gowenrw/g0dzilla_vs/art/g0dzilla_vs_3D_proto_combined.jpg

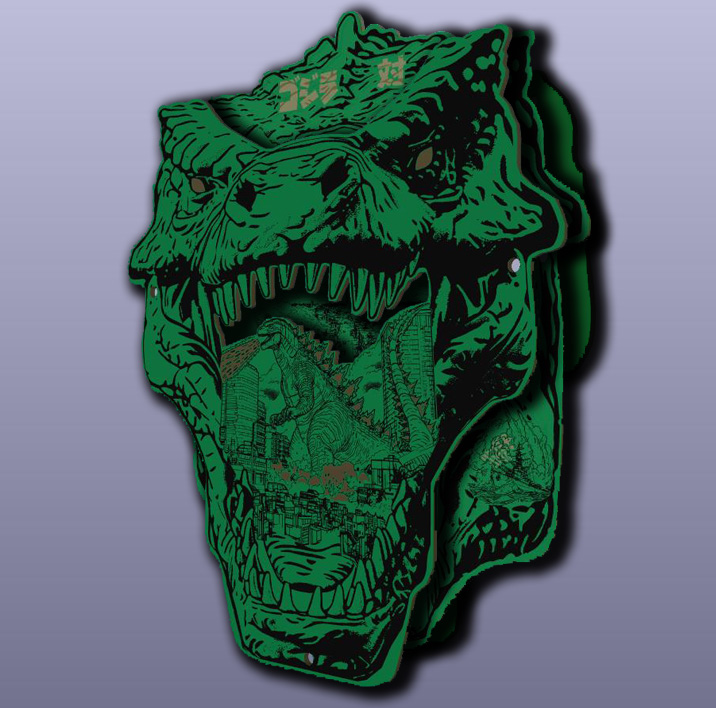
art/g0dzilla_vs_3D_proto_combined.jpg
