gowenrw/g0dzilla_vs/art/g0dzilla_vs_rev02_EdgeCuts-Export-04-01.jpg

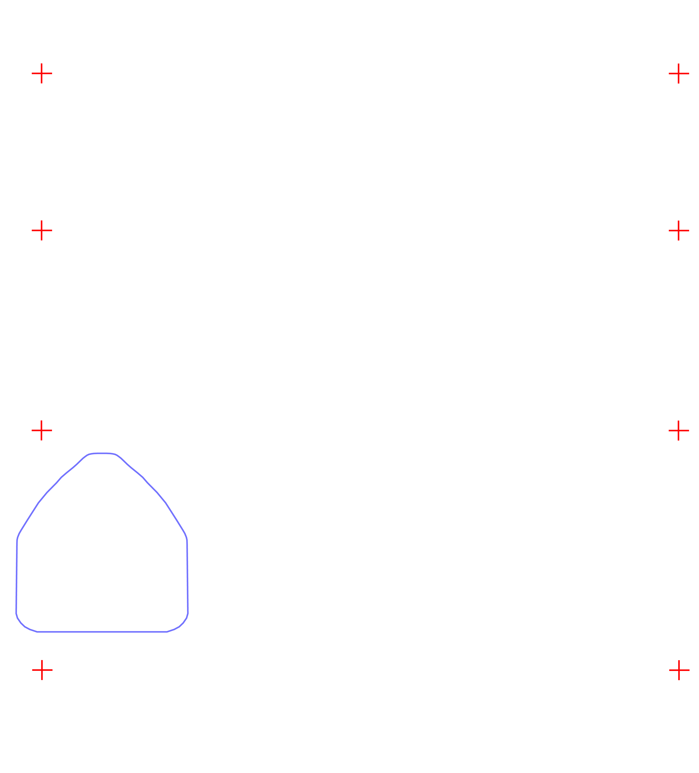
art/g0dzilla_vs_rev02_EdgeCuts-Export-04-01.jpg
