gowenrw/g0dzilla_vs/art/g0dzilla_vs_rev02_face_front.jpg

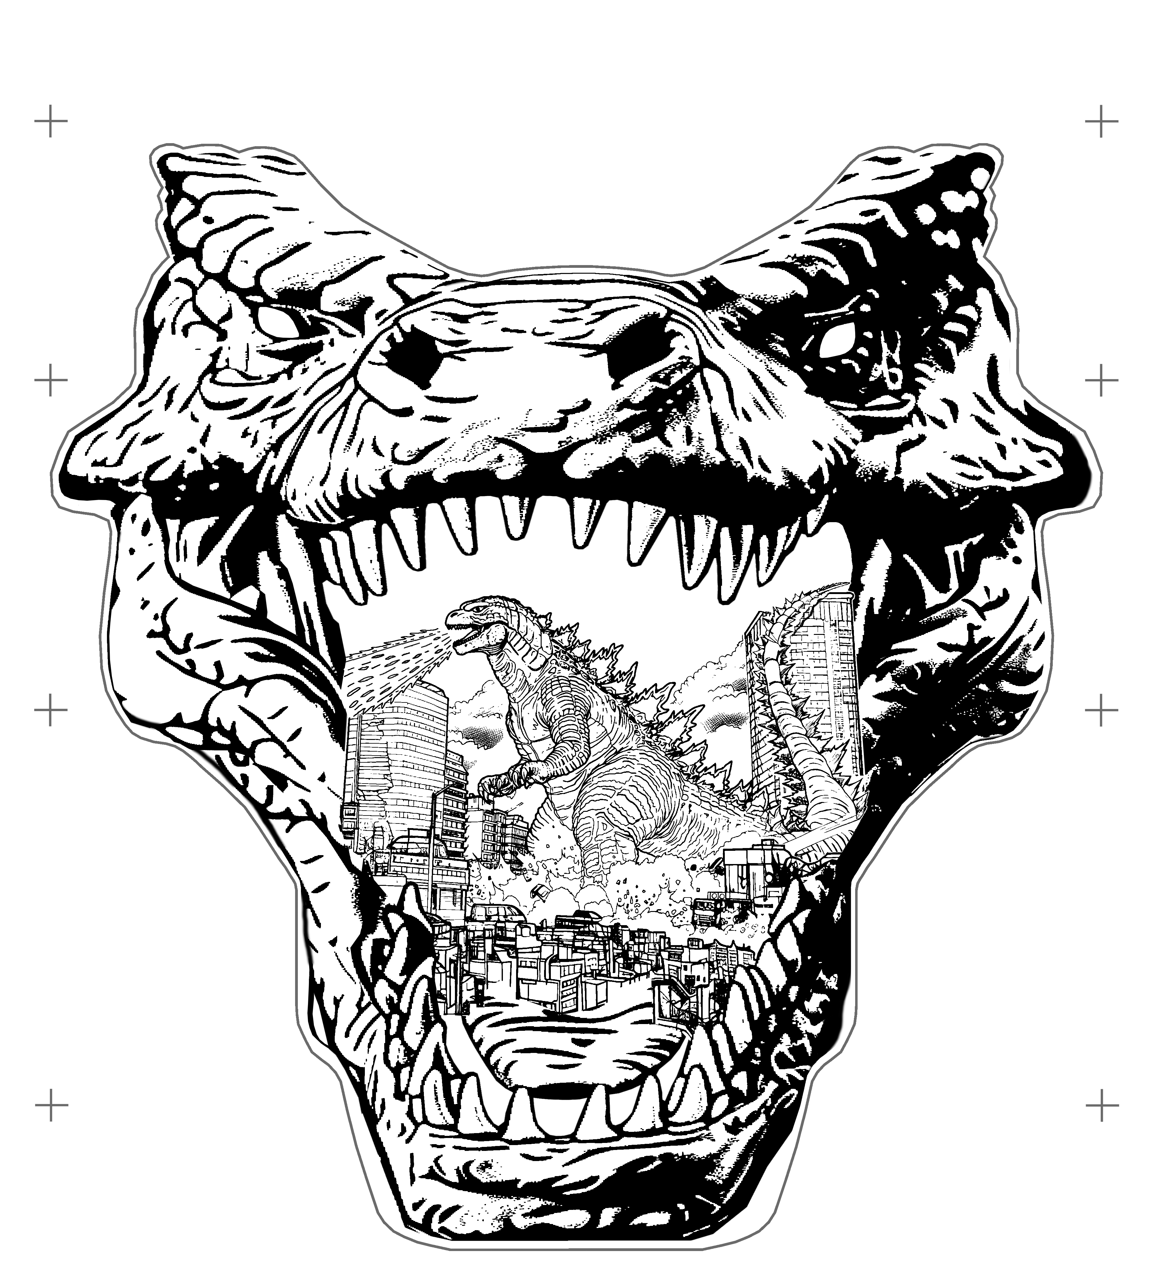
art/g0dzilla_vs_rev02_face_front.jpg
