gowenrw/g0dzilla_vs/art/g0dzilla_vs_rev02_face_front_centerg0dzilla_sm.png

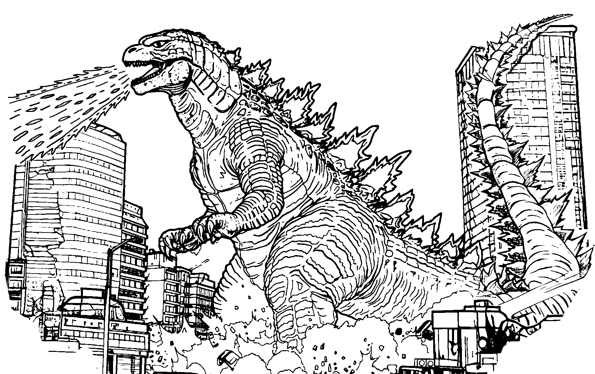
art/g0dzilla_vs_rev02_face_front_centerg0dzilla_sm.png
