gowenrw/g0dzilla_vs/art/g0dzilla_vs_rev02_face_mask_b.jpg

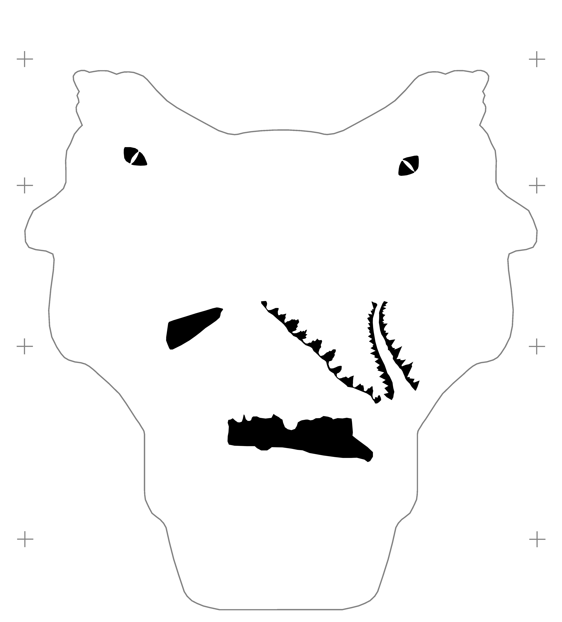
art/g0dzilla_vs_rev02_face_mask_b.jpg
