gowenrw/g0dzilla_vs/art/g0dzilla_vs_rev02_face_mask_f.jpg

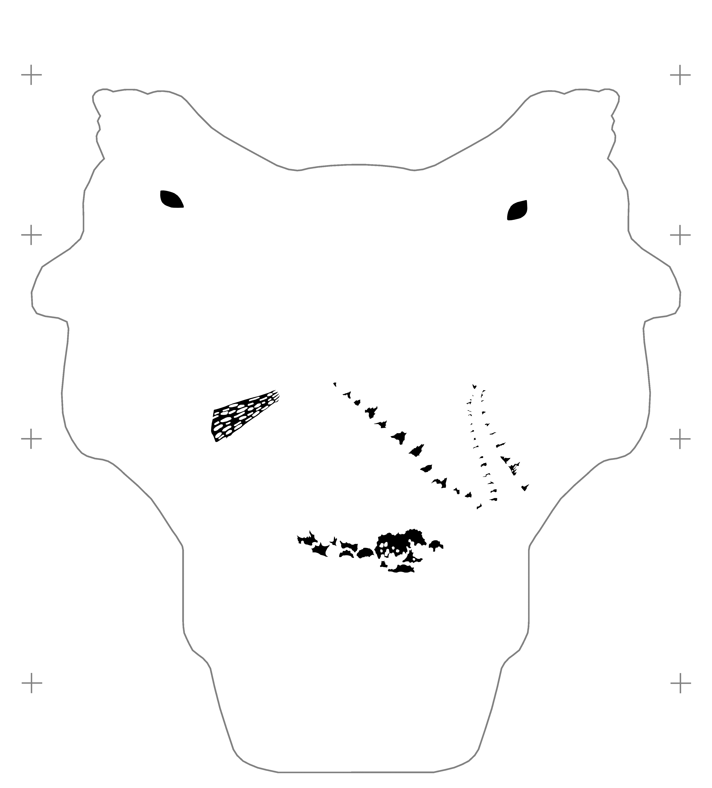
art/g0dzilla_vs_rev02_face_mask_f.jpg
