gowenrw/g0dzilla_vs/art/g0dzilla_vs_rev02_middle_back_mask.jpg

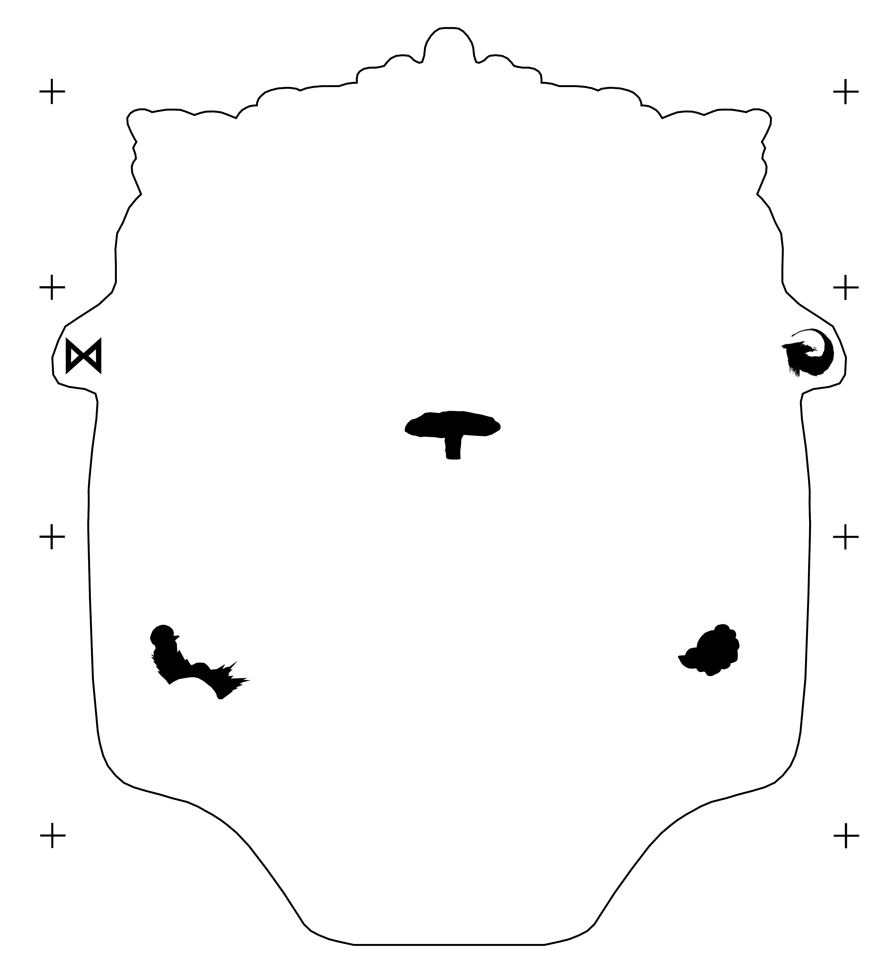
art/g0dzilla_vs_rev02_middle_back_mask.jpg
