gowenrw/g0dzilla_vs/art/g0dzilla_vs_rev02_middle_front_centermod_silk.jpg

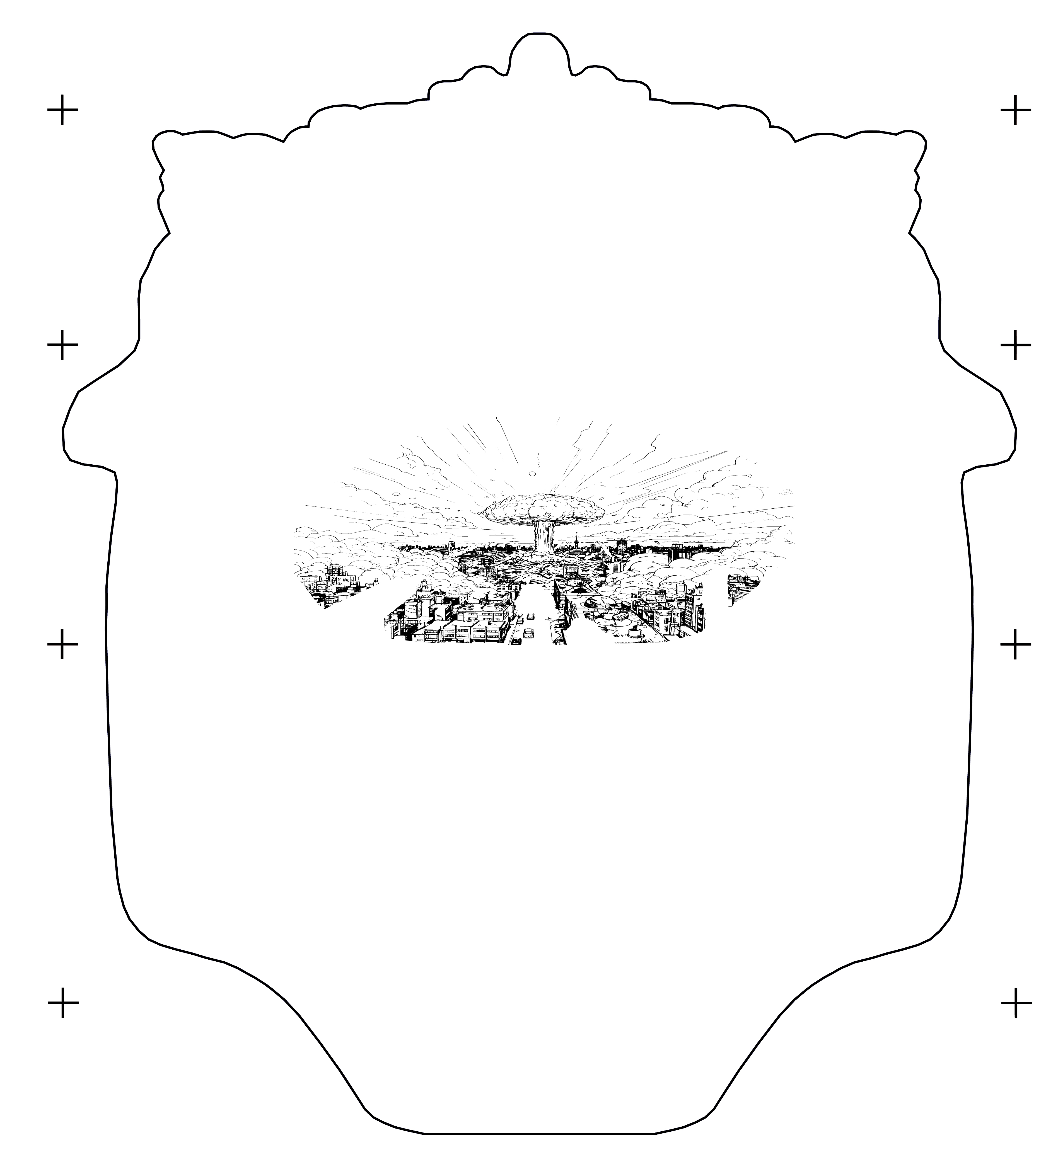
art/g0dzilla_vs_rev02_middle_front_centermod_silk.jpg
