gowenrw/g0dzilla_vs/art/g0dzilla_vs_rev02_middle_reference.jpg

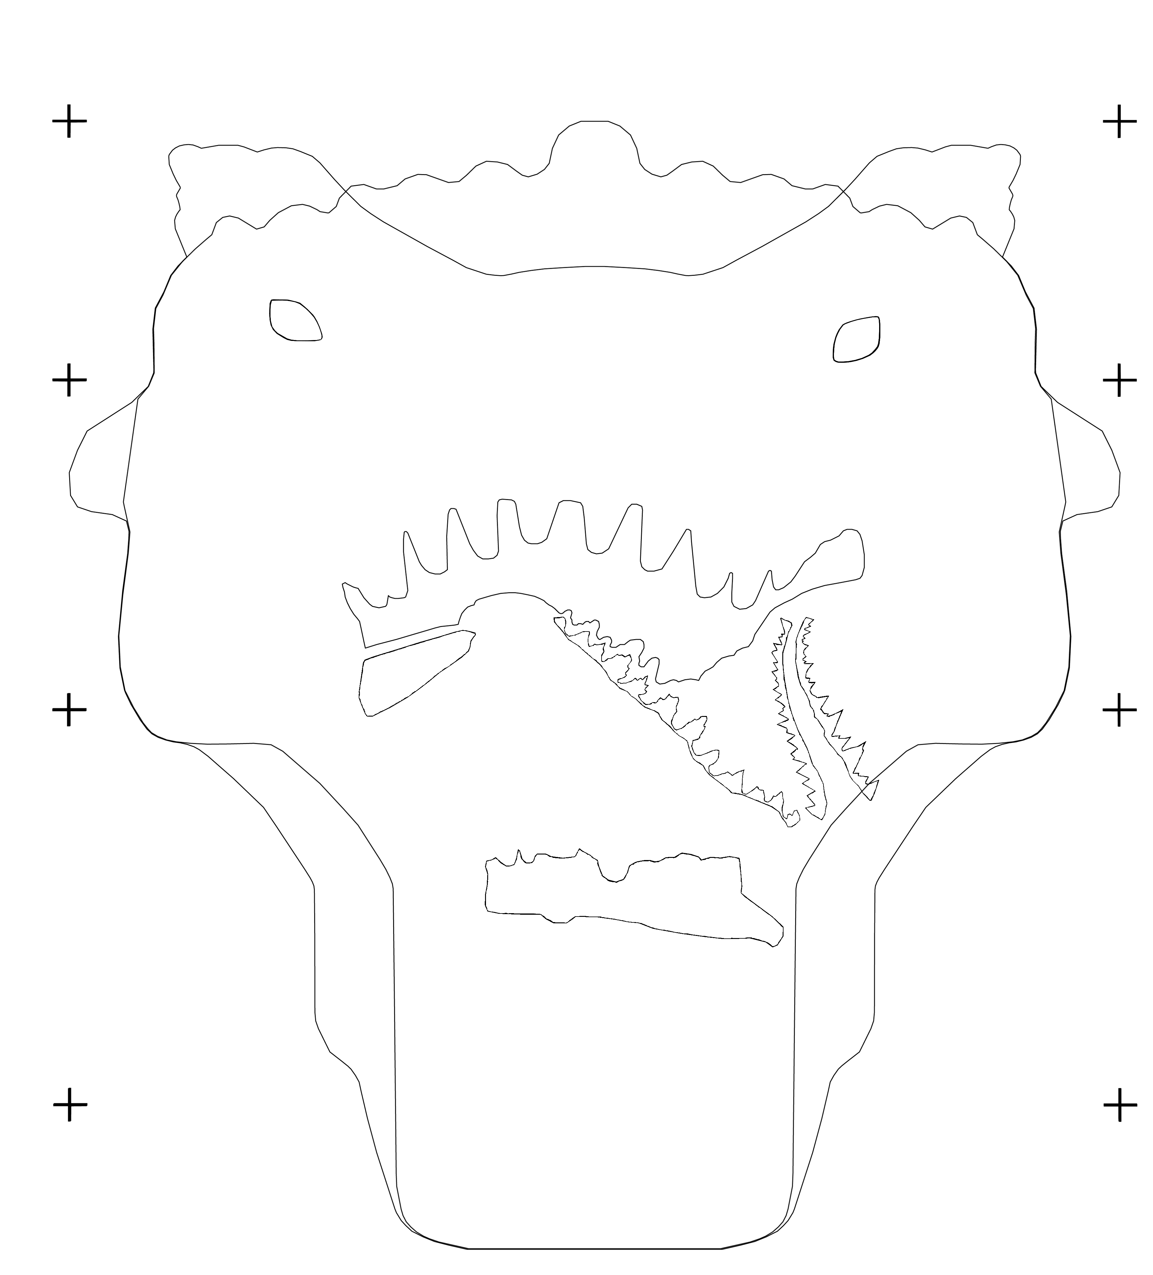
art/g0dzilla_vs_rev02_middle_reference.jpg
