gowenrw/g0dzilla_vs/art/g0dzilla_vs_rev02_SAO_H3lloKitty_mask_b.jpg

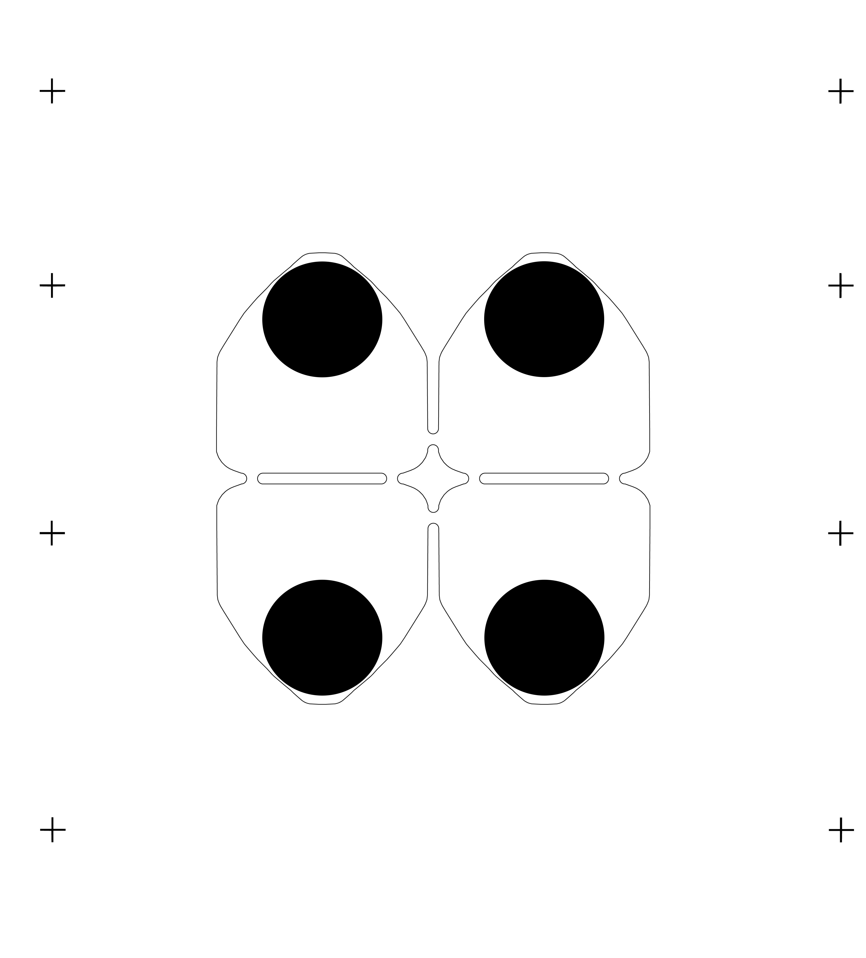
art/g0dzilla_vs_rev02_SAO_H3lloKitty_mask_b.jpg
