gowenrw/g0dzilla_vs/art/g0dzilla_vs_rev02_SAO_silk_f_flipped.jpg

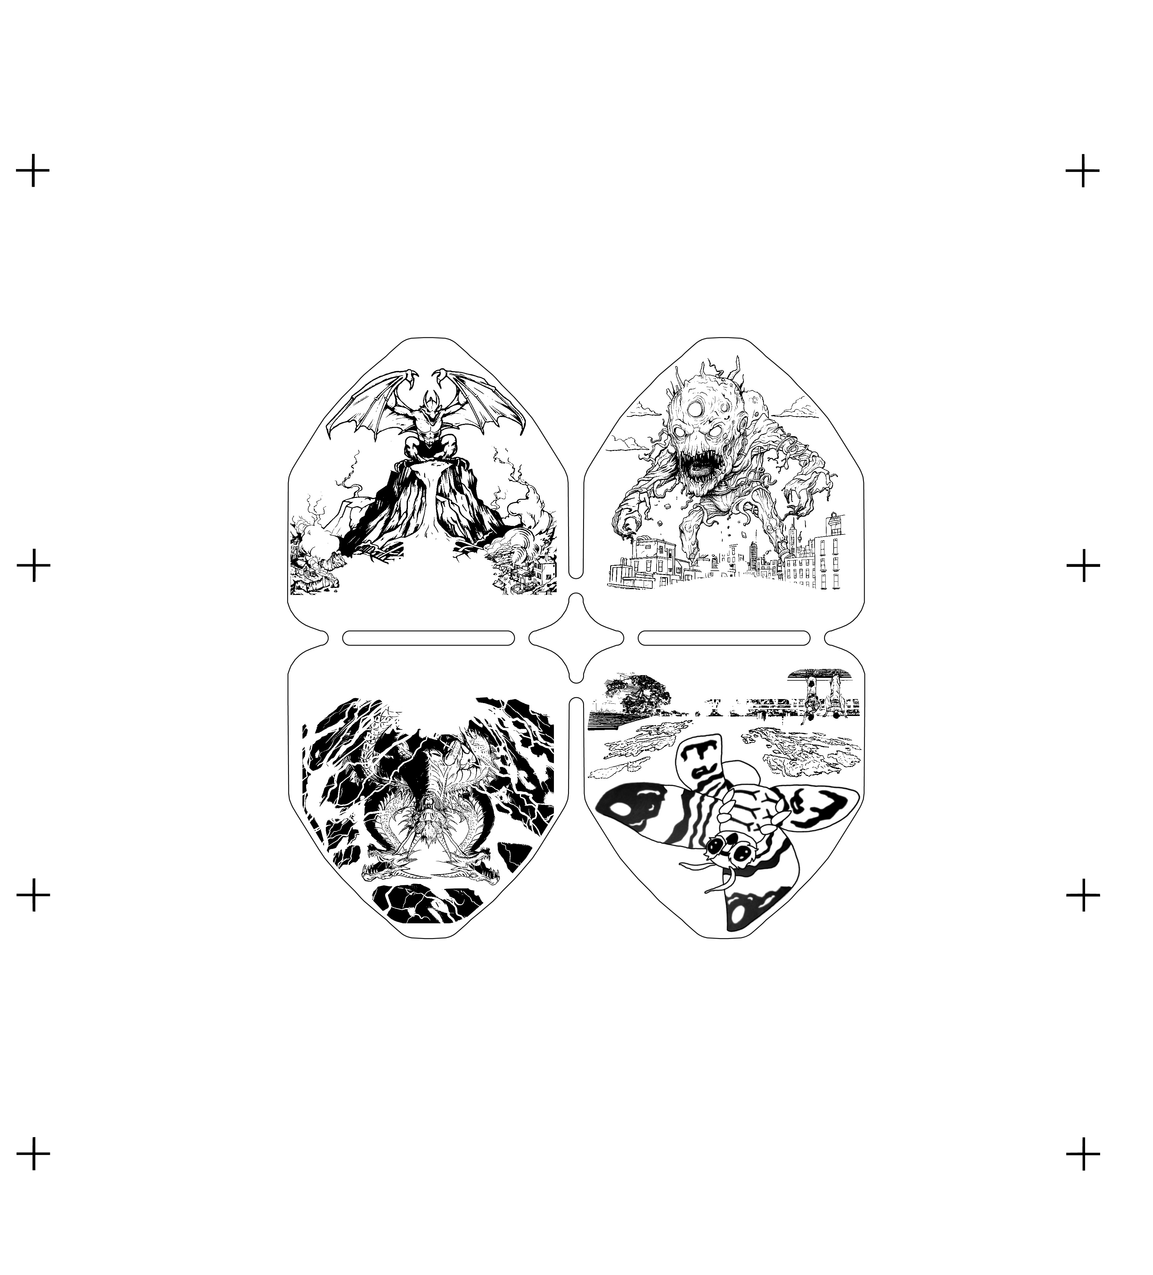
art/g0dzilla_vs_rev02_SAO_silk_f_flipped.jpg
