gowenrw/g0dzilla_vs/art/H3llo_Kitty-01.jpg

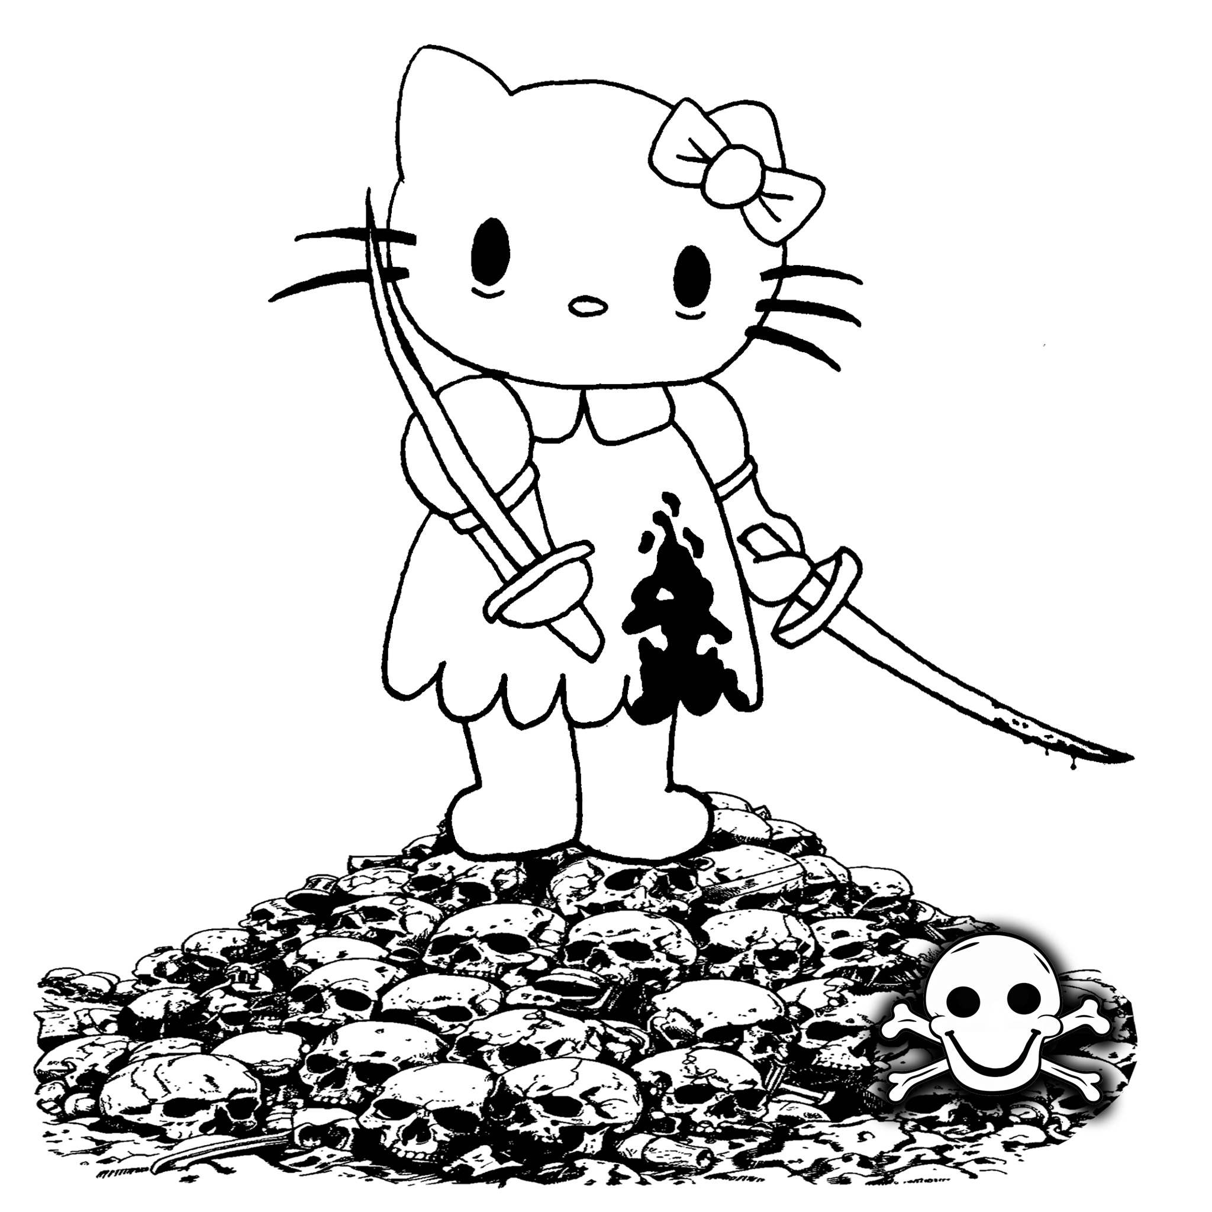
art/H3llo_Kitty-01.jpg
