gowenrw/g0dzilla_vs/art/H3llo_Kitty-02.jpg

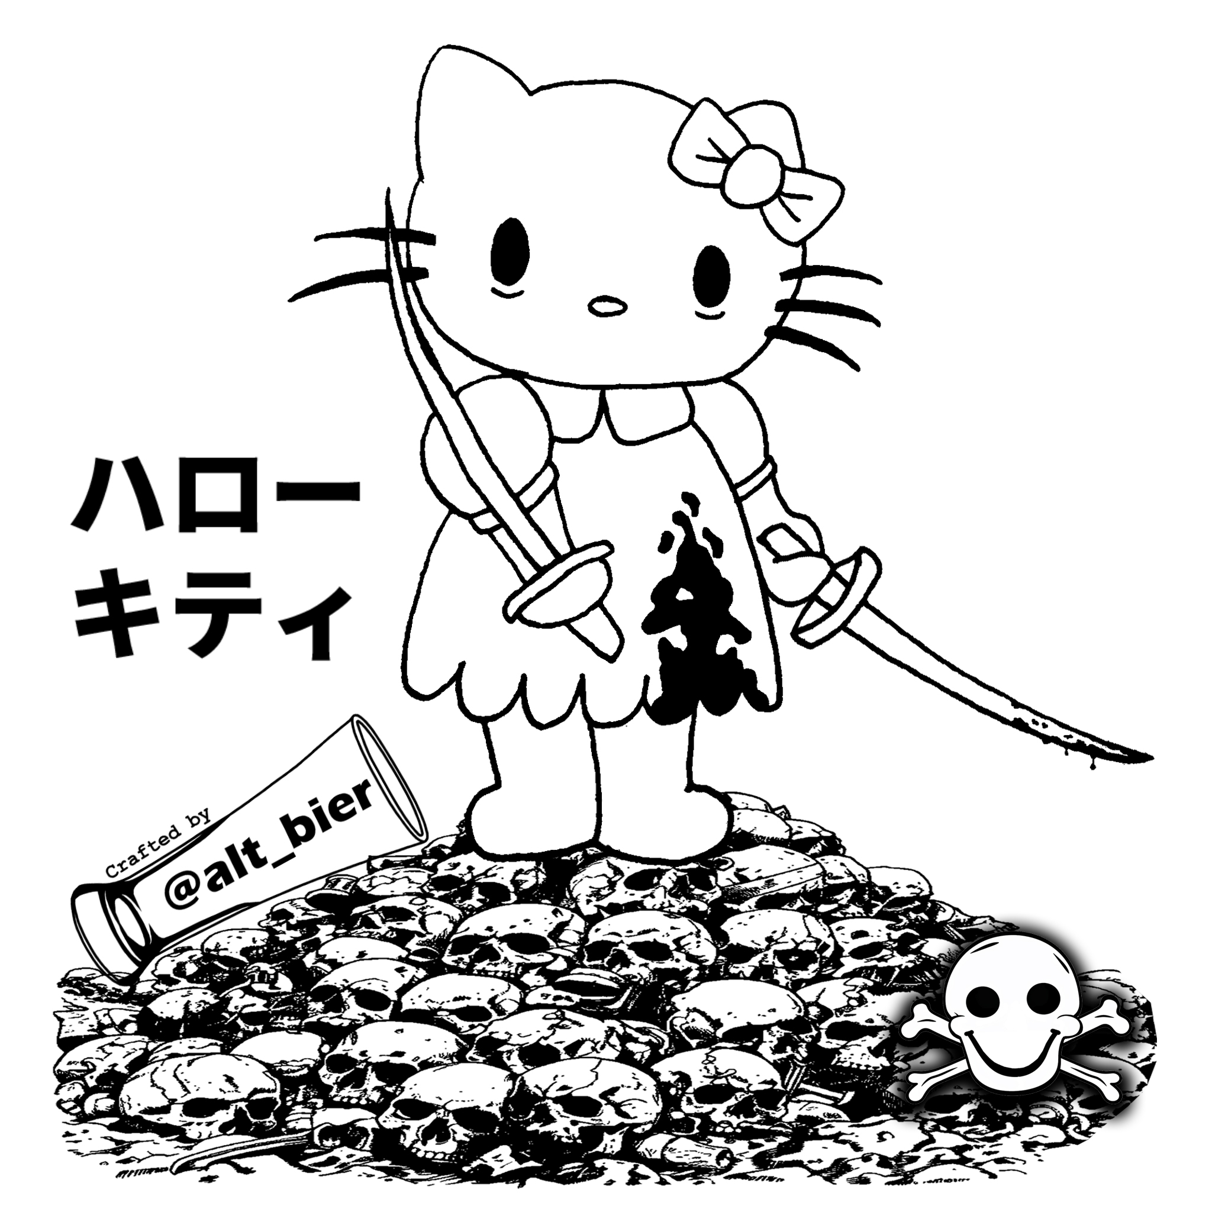
art/H3llo_Kitty-02.jpg
