gowenrw/g0dzilla_vs/art/H3lloKitty3Dexample.png

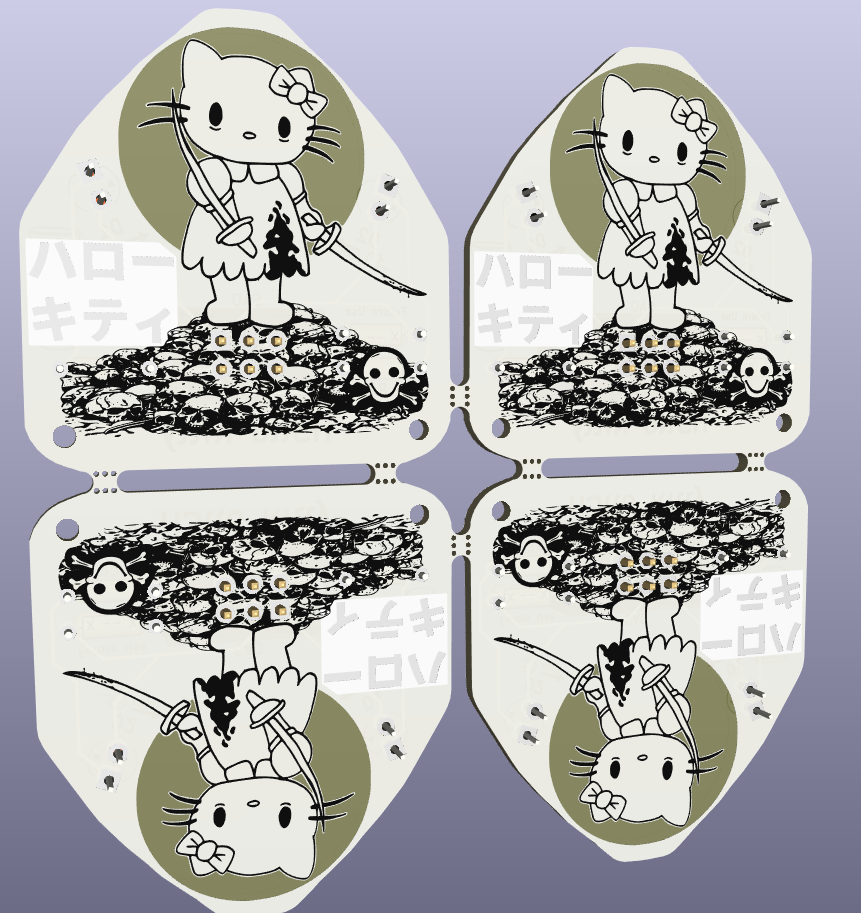
art/H3lloKitty3Dexample.png
