gowenrw/g0dzilla_vs/art/Happy_hacker_sticker.jpg

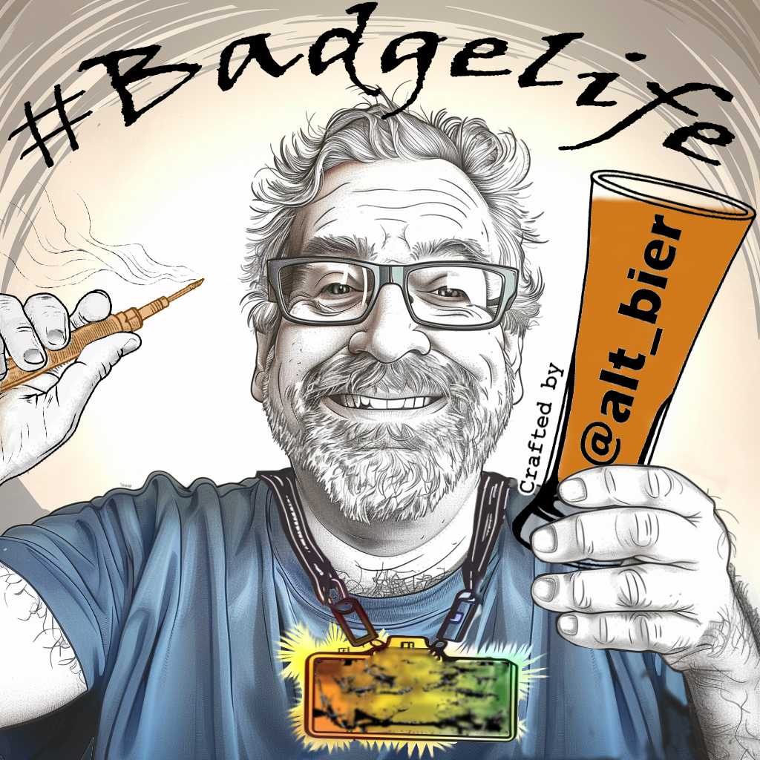
art/Happy_hacker_sticker.jpg
