gowenrw/g0dzilla_vs/art/hellokittty.jpg

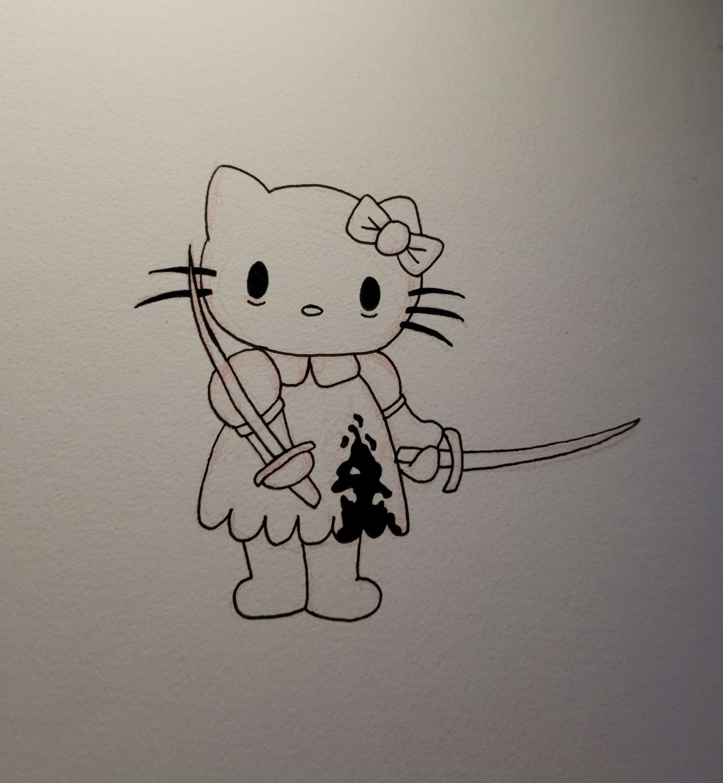
art/hellokittty.jpg
