gowenrw/g0dzilla_vs/art/inspiration/alt_bier_a_battleship_shooting_at_a_distant_target_with_smoke_p_59e326bd-52f1-43b2-ad76-d917be9670b9.png

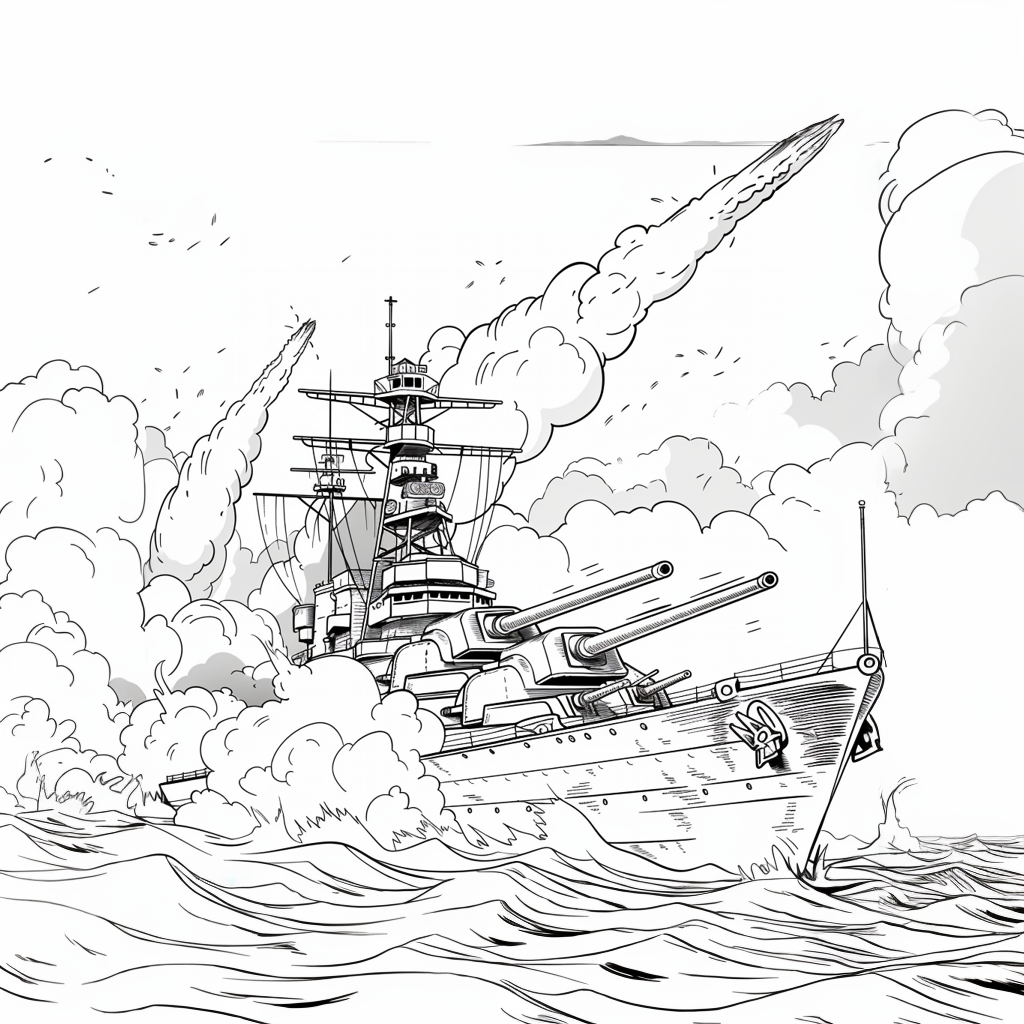
art/inspiration/alt_bier_a_battleship_shooting_at_a_distant_target_with_smoke_p_59e326bd-52f1-43b2-ad76-d917be9670b9.png
