gowenrw/g0dzilla_vs/art/inspiration/alt_bier_a_battleship_shooting_at_a_distant_target_with_smoke_p_f5903057-d492-474e-93da-c5aac78df1b0.png

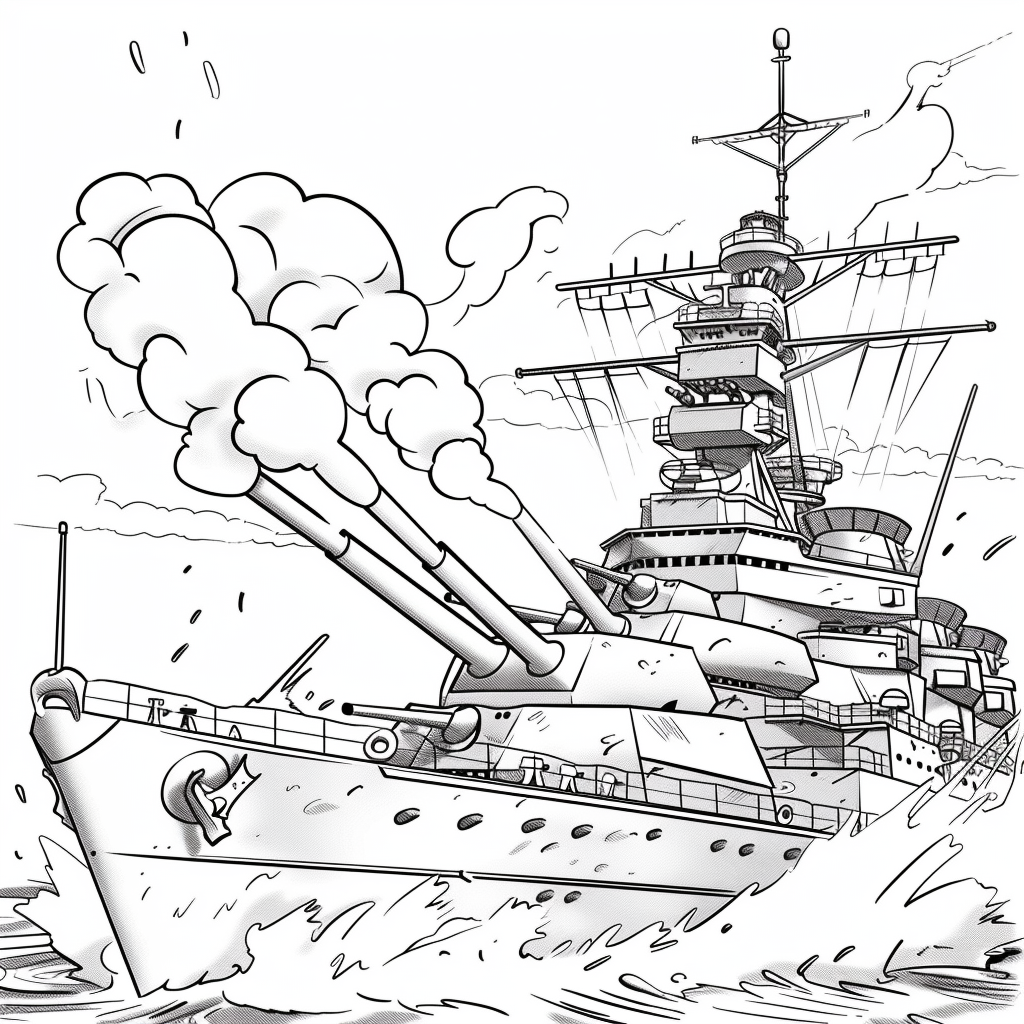
art/inspiration/alt_bier_a_battleship_shooting_at_a_distant_target_with_smoke_p_f5903057-d492-474e-93da-c5aac78df1b0.png
