gowenrw/g0dzilla_vs/art/inspiration/alt_bier_a_battleship_shooting_at_a_distant_target_with_smoke_p_fb66c47e-e783-47bd-8b08-65bacfc6591c.png

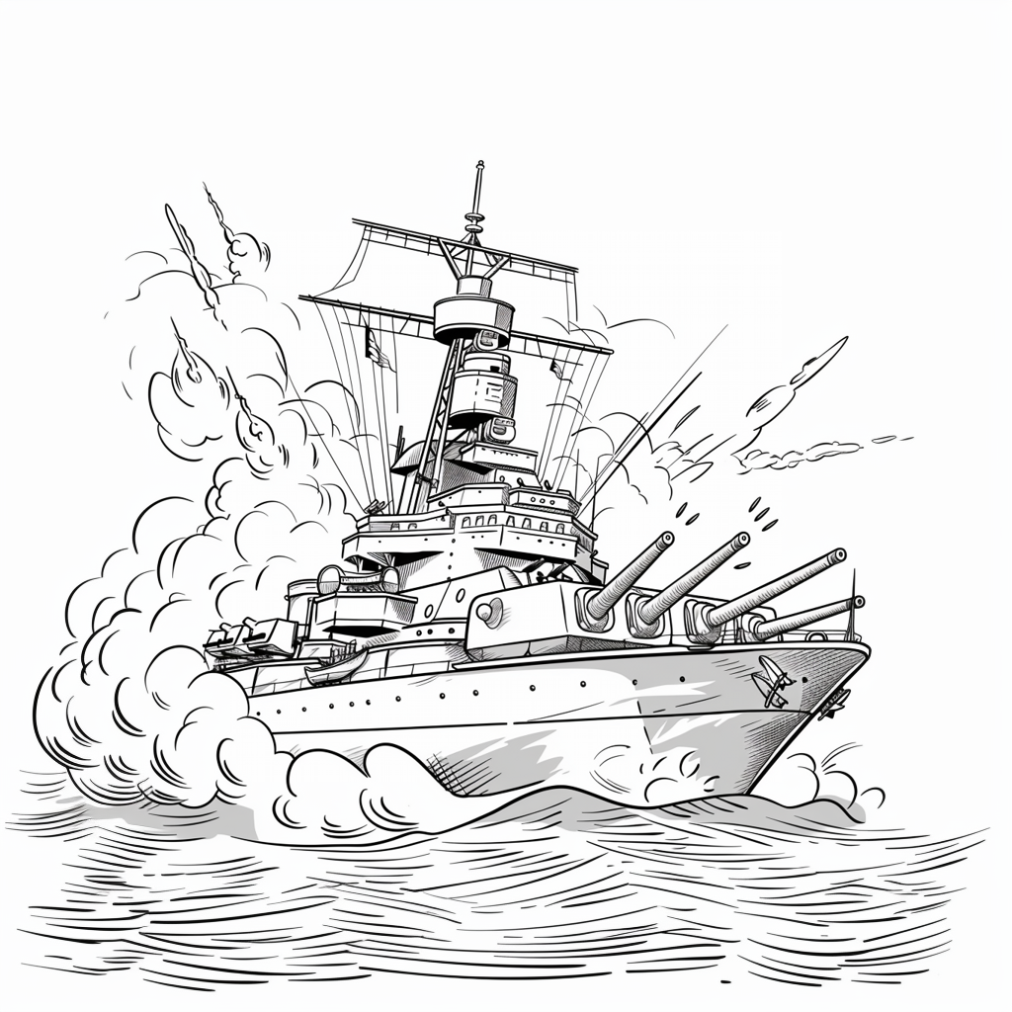
art/inspiration/alt_bier_a_battleship_shooting_at_a_distant_target_with_smoke_p_fb66c47e-e783-47bd-8b08-65bacfc6591c.png
