gowenrw/g0dzilla_vs/art/inspiration/alt_bier_black_and_white_coloring_page_black_lines_no_color_no__a32ff452-0e3a-46d1-adf2-12769ea9052f.png

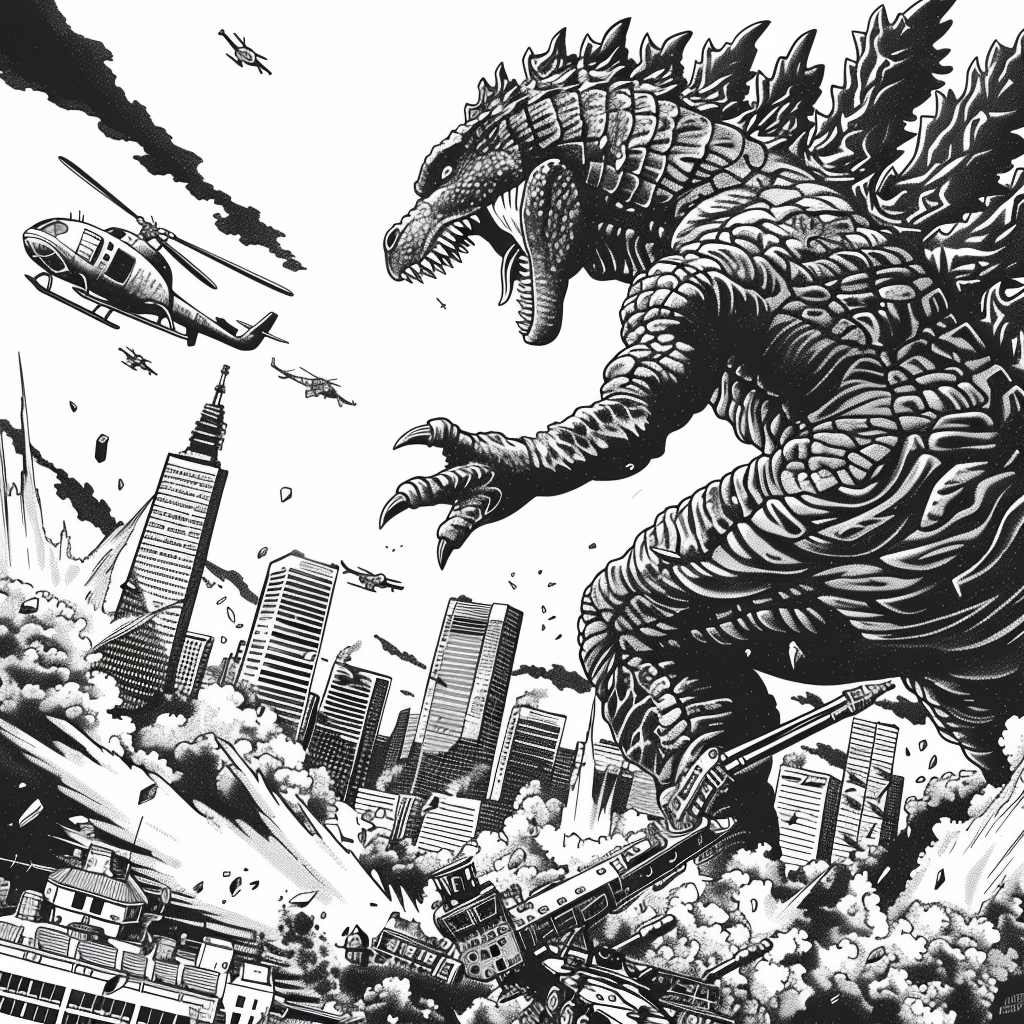
art/inspiration/alt_bier_black_and_white_coloring_page_black_lines_no_color_no__a32ff452-0e3a-46d1-adf2-12769ea9052f.png
