gowenrw/g0dzilla_vs/art/inspiration/alt_bier_black_and_white_coloring_page_black_lines_no_color_no__cfd4e92b-0c43-4593-8ce6-b8f9310a5832.png

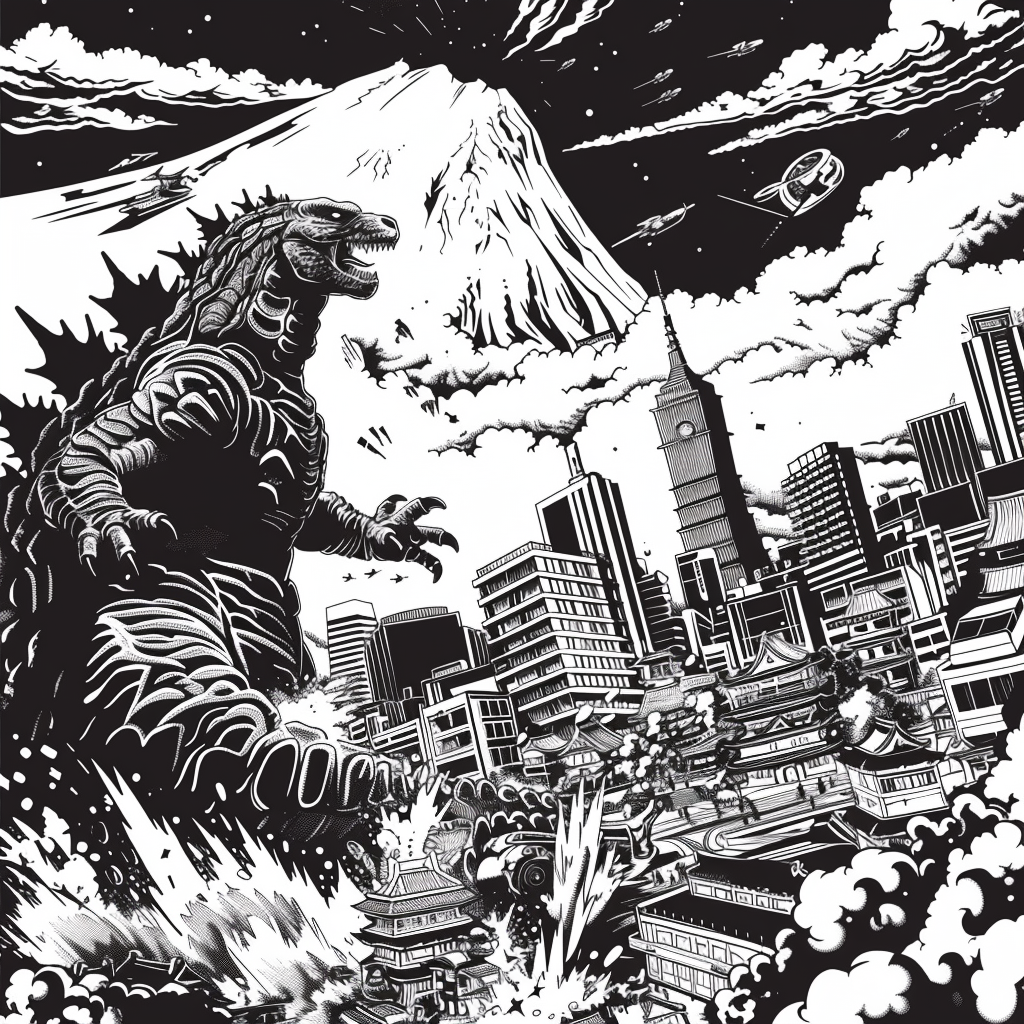
art/inspiration/alt_bier_black_and_white_coloring_page_black_lines_no_color_no__cfd4e92b-0c43-4593-8ce6-b8f9310a5832.png
