gowenrw/g0dzilla_vs/art/inspiration/alt_bier_black_and_white_coloring_page_black_outlines_no_shadin_79cd9181-edb0-4174-a10c-7cebca9cc1b9.png

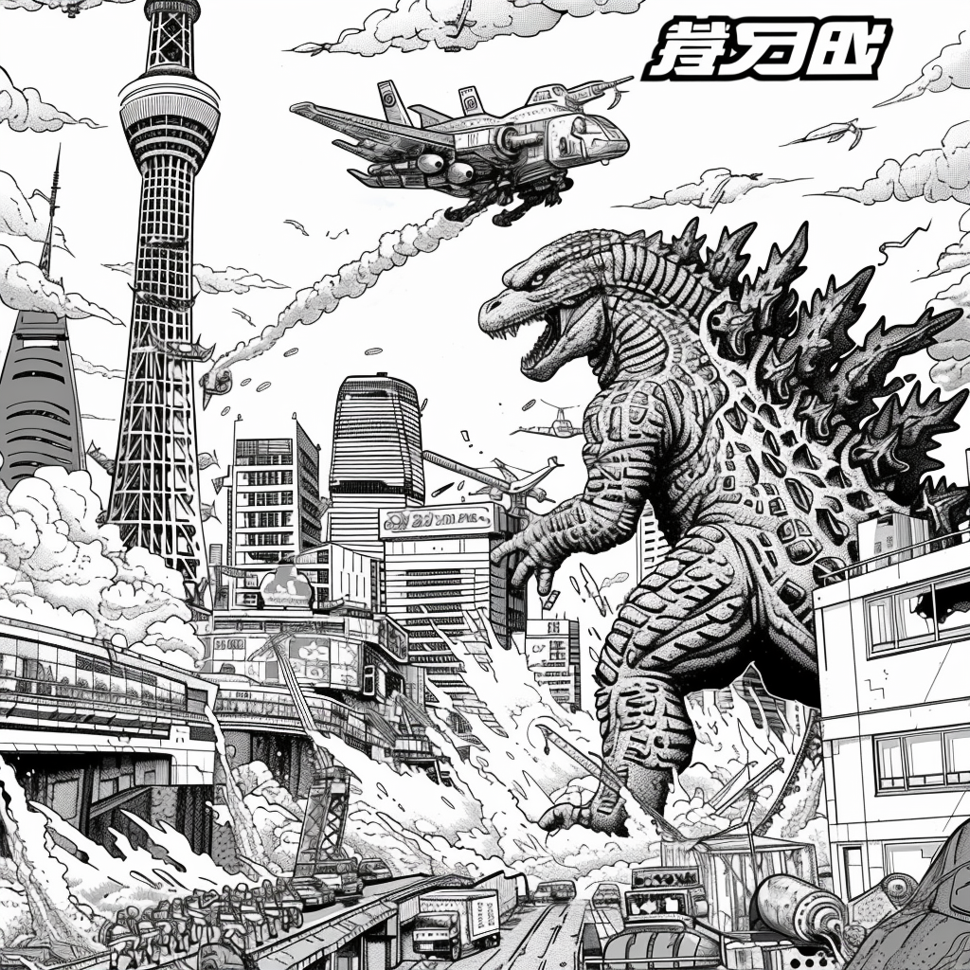
art/inspiration/alt_bier_black_and_white_coloring_page_black_outlines_no_shadin_79cd9181-edb0-4174-a10c-7cebca9cc1b9.png
