gowenrw/g0dzilla_vs/art/inspiration/alt_bier_Ghidorah_The_Three-Headed_Monster_lineart_in_the_style_86dc54b7-110f-4f28-985a-e487389cda8e.png

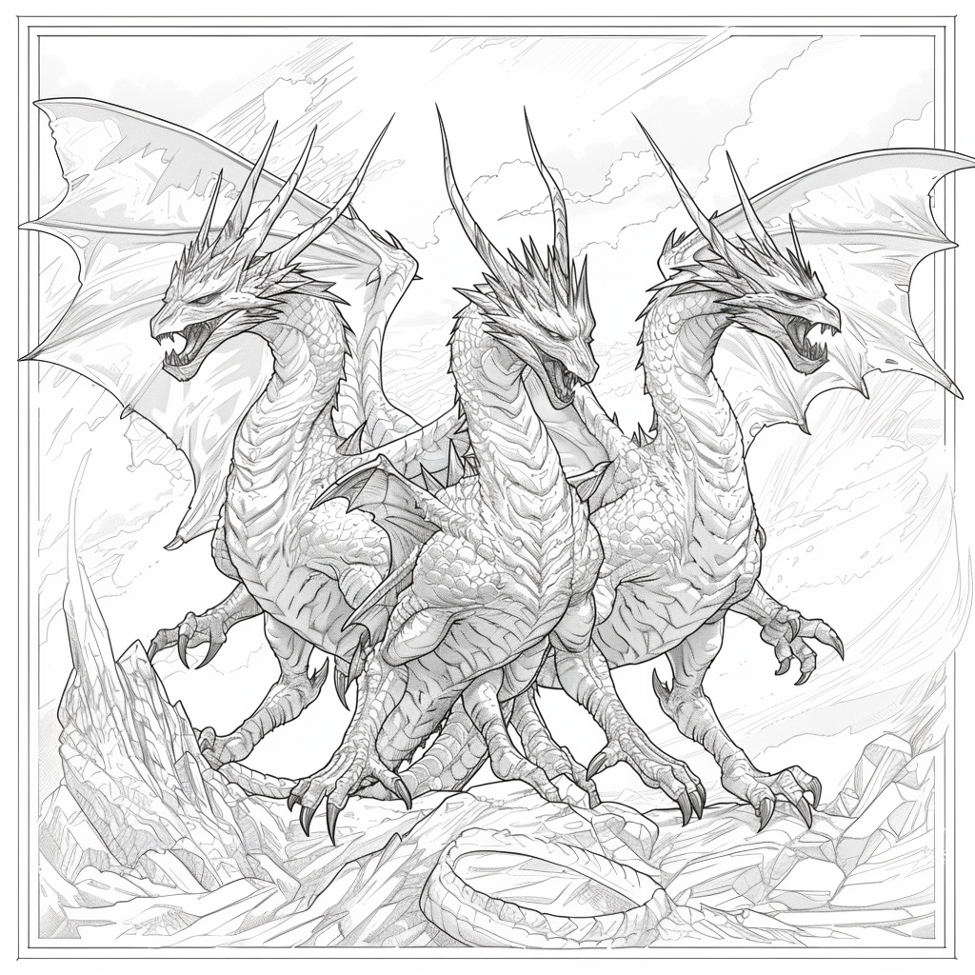
art/inspiration/alt_bier_Ghidorah_The_Three-Headed_Monster_lineart_in_the_style_86dc54b7-110f-4f28-985a-e487389cda8e.png
