gowenrw/g0dzilla_vs/art/inspiration/alt_bier_godzilla_destroying_a_city_while_tanks_shoot_at_him_si_82caa747-4cf3-47df-a6cb-602a75737ce2.png

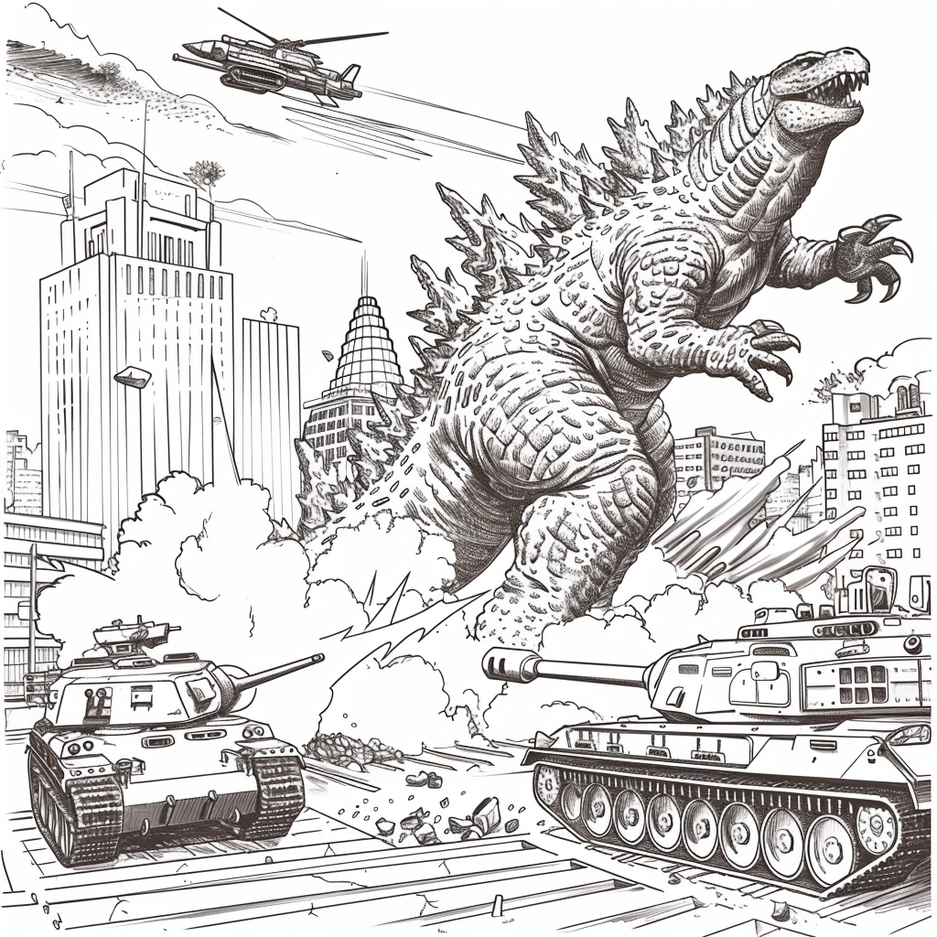
art/inspiration/alt_bier_godzilla_destroying_a_city_while_tanks_shoot_at_him_si_82caa747-4cf3-47df-a6cb-602a75737ce2.png
