gowenrw/g0dzilla_vs/art/inspiration/alt_bier_godzilla_destroying_a_city_while_tanks_shoot_at_him_si_bd4bd75f-41e4-4a65-852b-48508166c79f.png

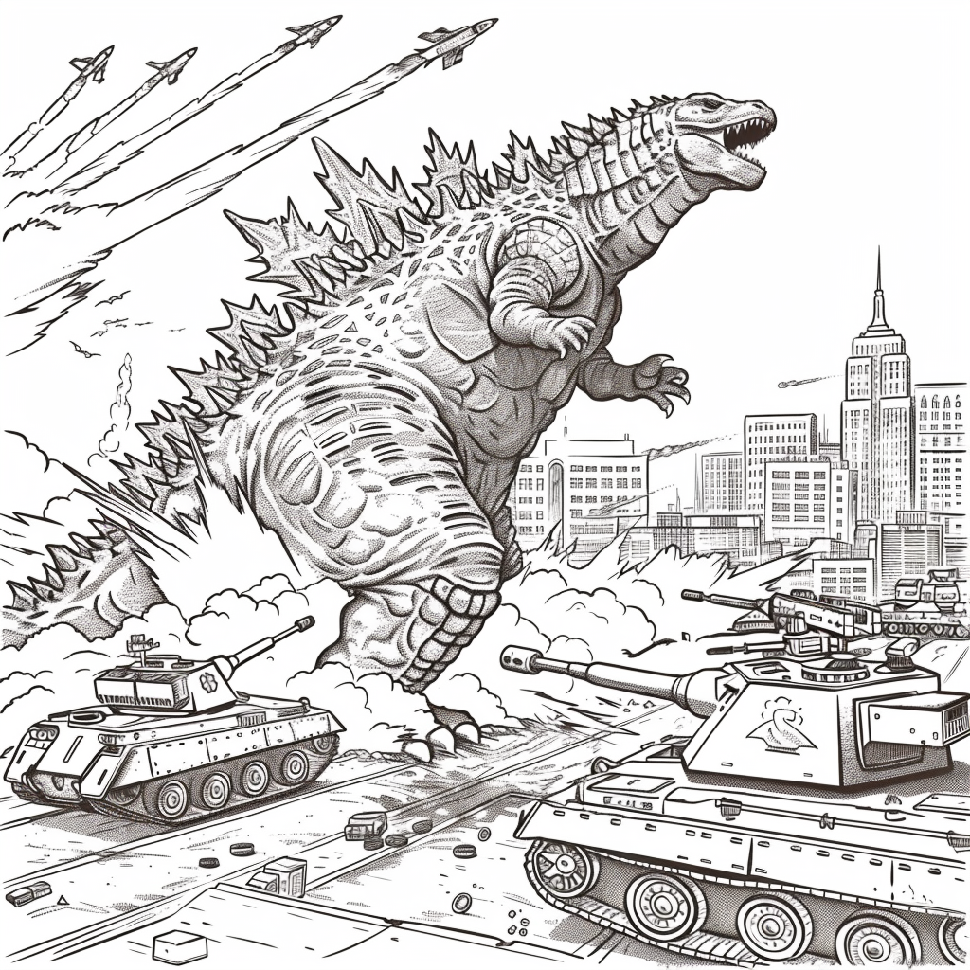
art/inspiration/alt_bier_godzilla_destroying_a_city_while_tanks_shoot_at_him_si_bd4bd75f-41e4-4a65-852b-48508166c79f.png
