gowenrw/g0dzilla_vs/art/inspiration/alt_bier_Godzilla_destroying_Tokyo_lineart_in_the_style_of_colo_4d4a2086-2009-444f-8c58-504ba2b92d18.png

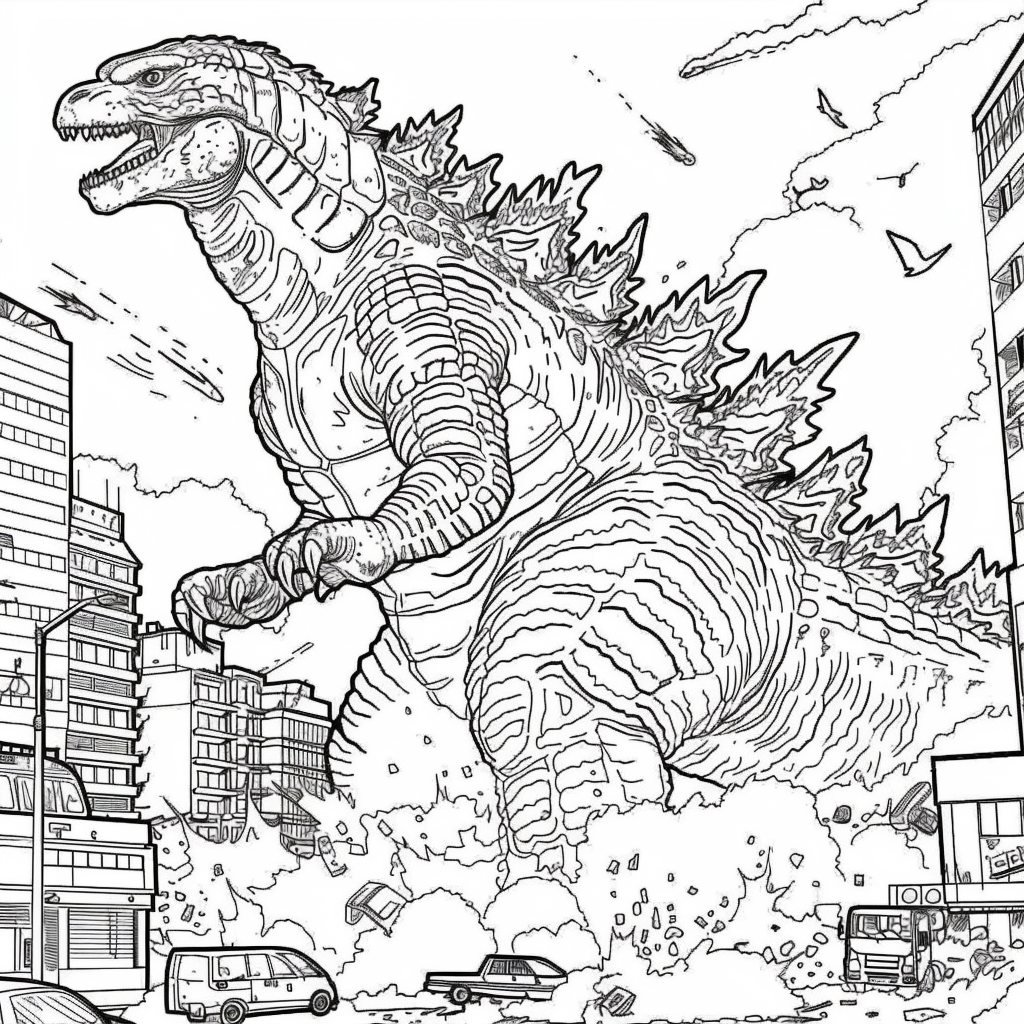
art/inspiration/alt_bier_Godzilla_destroying_Tokyo_lineart_in_the_style_of_colo_4d4a2086-2009-444f-8c58-504ba2b92d18.png
