gowenrw/g0dzilla_vs/art/inspiration/alt_bier_Godzilla_destroying_Tokyo_lineart_in_the_style_of_colo_d7bfe551-c640-41c3-b317-bbeb8b02db80.png

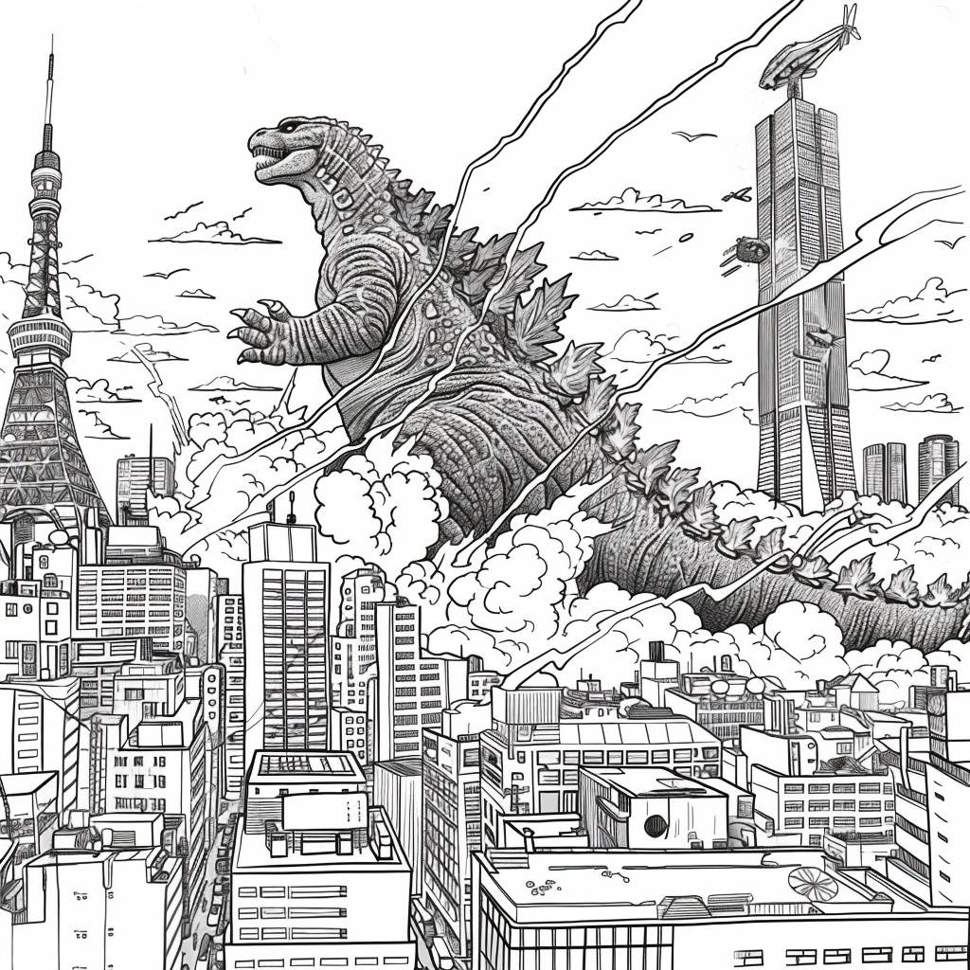
art/inspiration/alt_bier_Godzilla_destroying_Tokyo_lineart_in_the_style_of_colo_d7bfe551-c640-41c3-b317-bbeb8b02db80.png
