gowenrw/g0dzilla_vs/art/inspiration/alt_bier_Godzilla_destroying_Tokyo_lineart_in_the_style_of_colo_e03cd96b-dc8a-4526-982b-66ee4f9de8dd.png

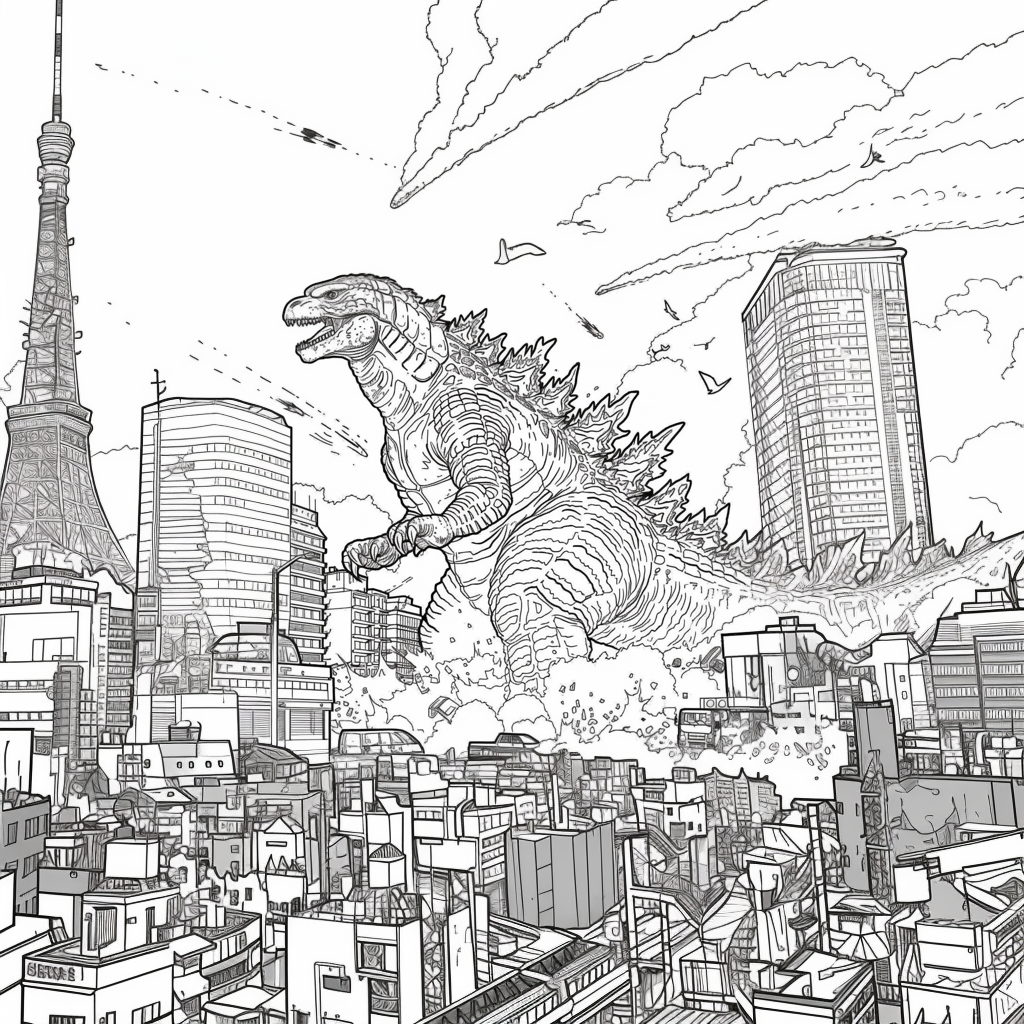
art/inspiration/alt_bier_Godzilla_destroying_Tokyo_lineart_in_the_style_of_colo_e03cd96b-dc8a-4526-982b-66ee4f9de8dd.png
