gowenrw/g0dzilla_vs/art/inspiration/alt_bier_Godzilla_destrying_Tokyo_while_military_defends_linear_1b44dcd3-306b-4535-a66b-cad9bfdc10d3.png

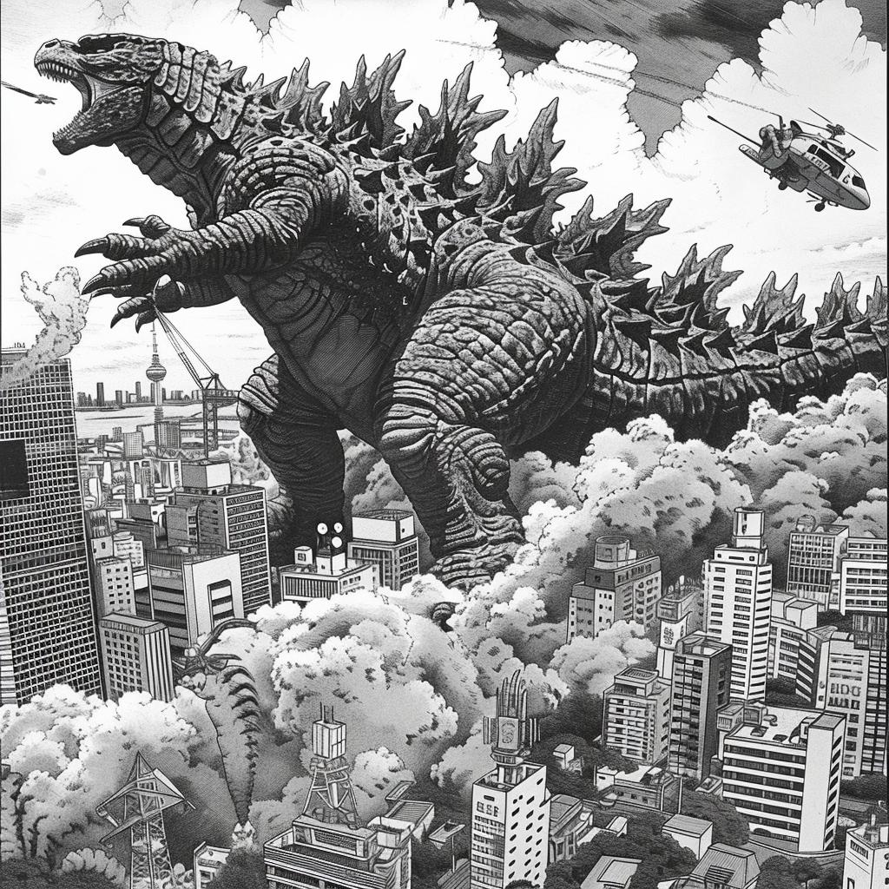
art/inspiration/alt_bier_Godzilla_destrying_Tokyo_while_military_defends_linear_1b44dcd3-306b-4535-a66b-cad9bfdc10d3.png
