gowenrw/g0dzilla_vs/art/inspiration/alt_bier_Godzilla_destrying_Tokyo_while_military_defends_linear_4e497d5a-1747-450a-990a-830911315ccd.png

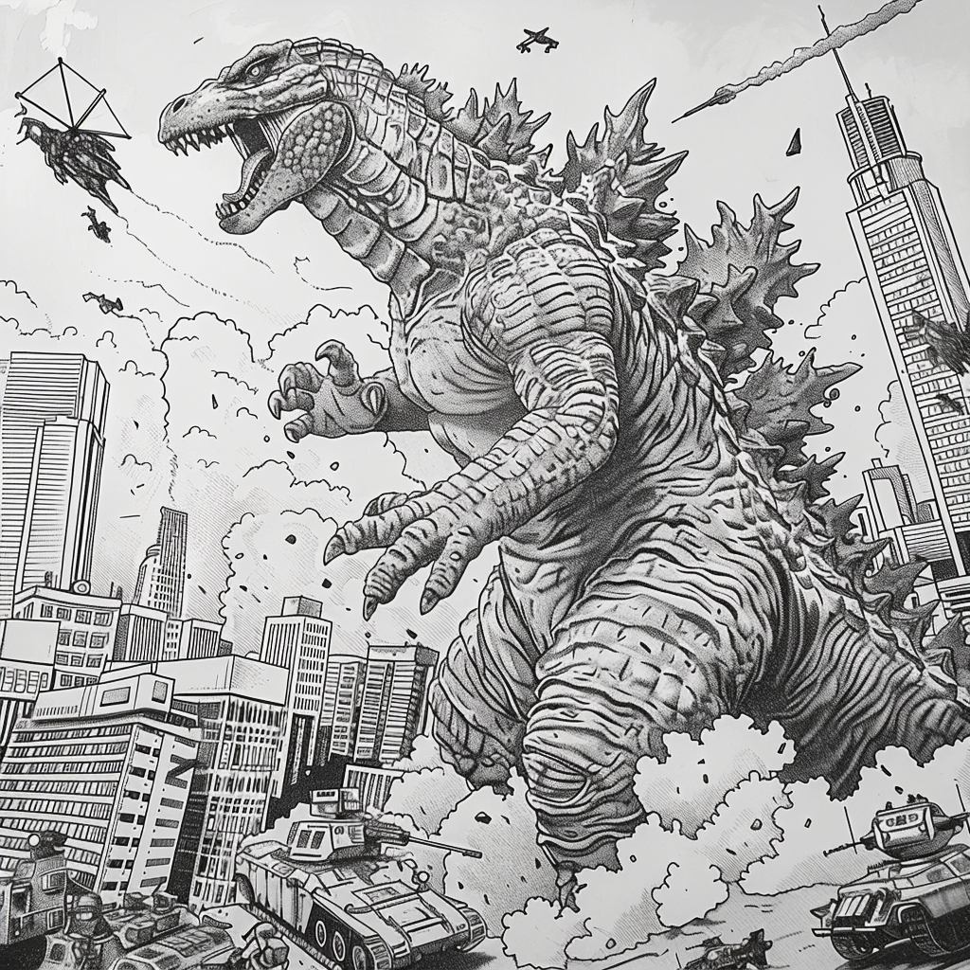
art/inspiration/alt_bier_Godzilla_destrying_Tokyo_while_military_defends_linear_4e497d5a-1747-450a-990a-830911315ccd.png
