gowenrw/g0dzilla_vs/art/inspiration/alt_bier_Godzilla_destrying_Tokyo_while_military_defends_linear_92e3e7ca-580a-4b75-b6aa-51d95cd60097.png

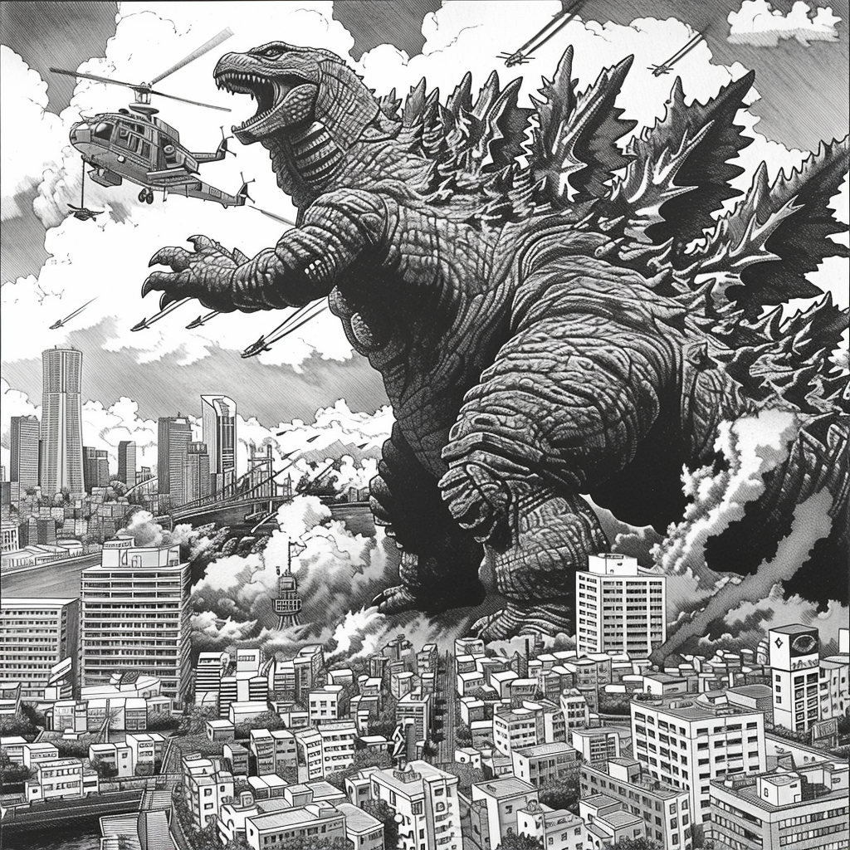
art/inspiration/alt_bier_Godzilla_destrying_Tokyo_while_military_defends_linear_92e3e7ca-580a-4b75-b6aa-51d95cd60097.png
