gowenrw/g0dzilla_vs/art/inspiration/alt_bier_Godzilla_destrying_Tokyo_while_military_defends_linear_70911870-9460-499b-9aaa-d368c7292fe0.png

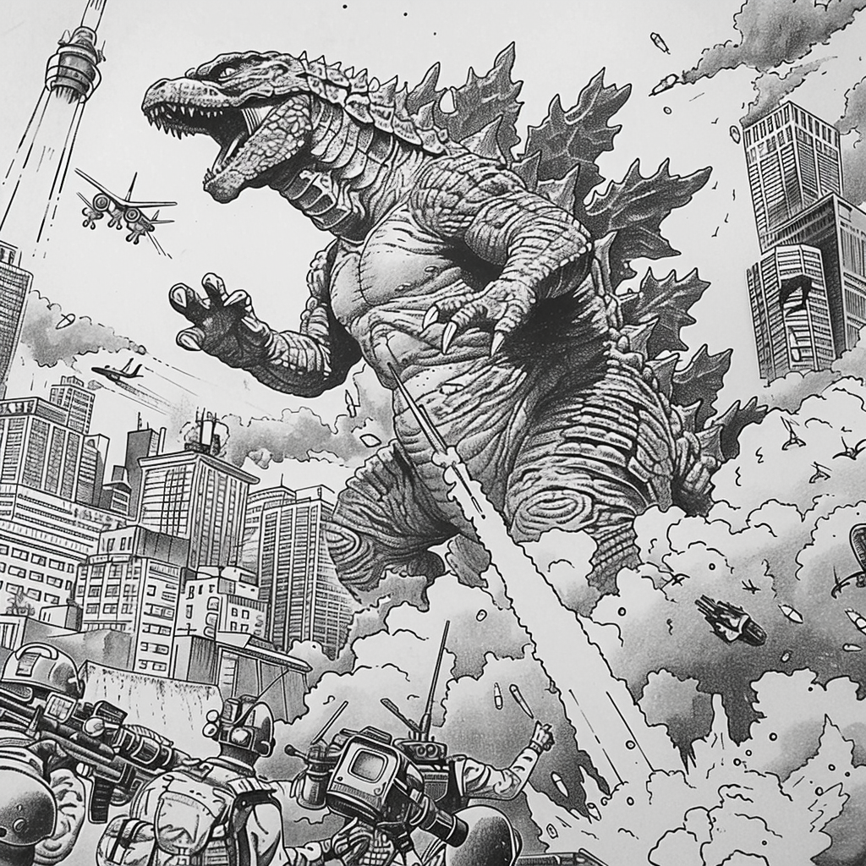
art/inspiration/alt_bier_Godzilla_destrying_Tokyo_while_military_defends_linear_70911870-9460-499b-9aaa-d368c7292fe0.png
