gowenrw/g0dzilla_vs/art/inspiration/alt_bier_Godzilla_destrying_Tokyo_while_military_defends_linear_e468670f-f13b-4f14-8b61-33f82d4c3400.png

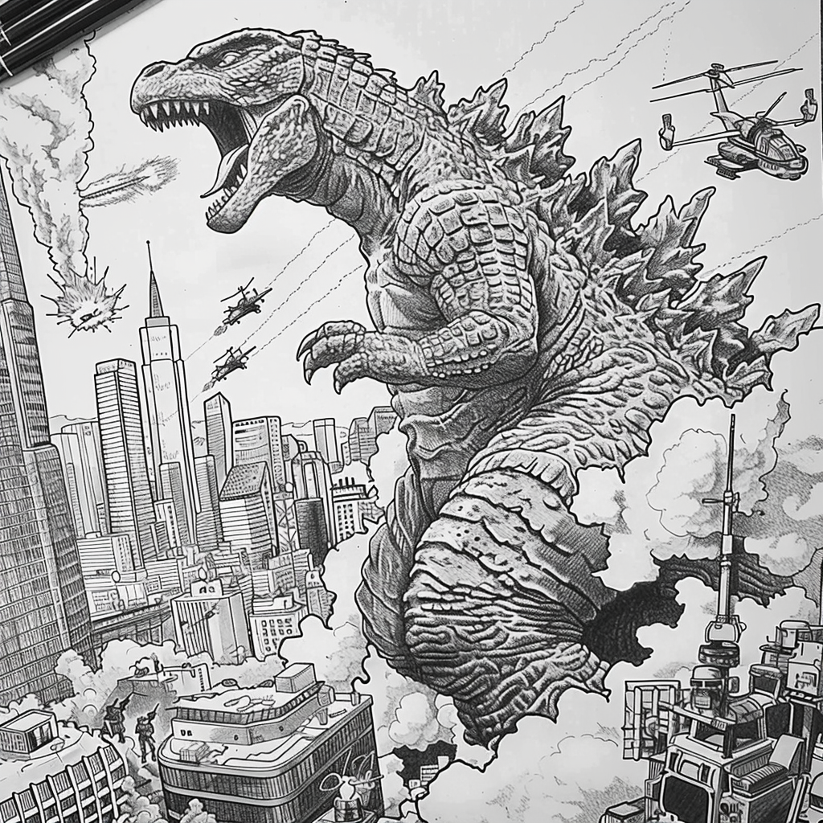
art/inspiration/alt_bier_Godzilla_destrying_Tokyo_while_military_defends_linear_e468670f-f13b-4f14-8b61-33f82d4c3400.png
