gowenrw/g0dzilla_vs/art/inspiration/alt_bier_godzilla_head_looking_at_you_with_mouth_partially_open_0b8898f7-95fb-49da-ae73-ee845933c083.png

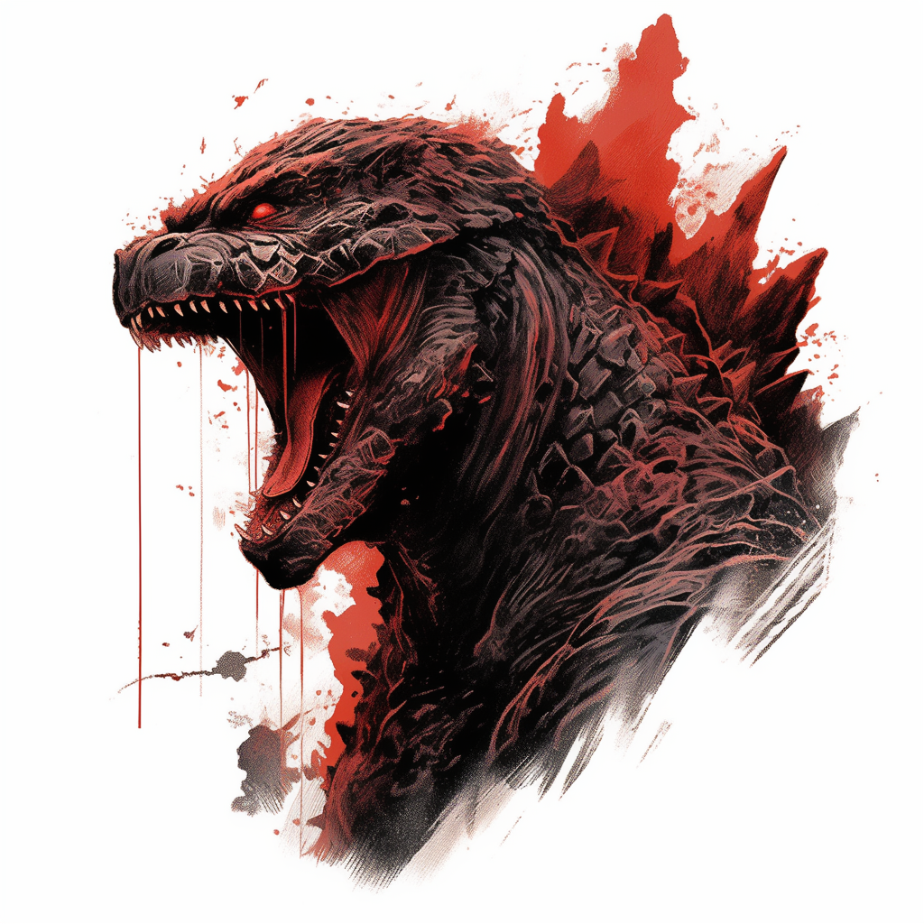
art/inspiration/alt_bier_godzilla_head_looking_at_you_with_mouth_partially_open_0b8898f7-95fb-49da-ae73-ee845933c083.png
