gowenrw/g0dzilla_vs/art/inspiration/alt_bier_godzilla_head_looking_at_you_with_mouth_partially_open_1bab6a91-75e9-4c20-a77d-6843088557c4.png

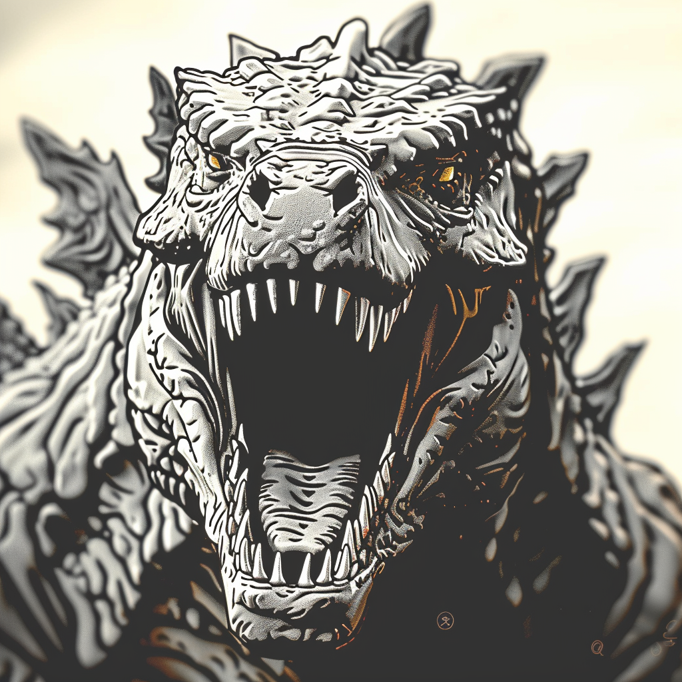
art/inspiration/alt_bier_godzilla_head_looking_at_you_with_mouth_partially_open_1bab6a91-75e9-4c20-a77d-6843088557c4.png
