gowenrw/g0dzilla_vs/art/inspiration/alt_bier_Godzilla_head_looking_at_you_with_mouth_partially_open_52278a28-6683-4eaa-83e5-dbef07206d8f.png

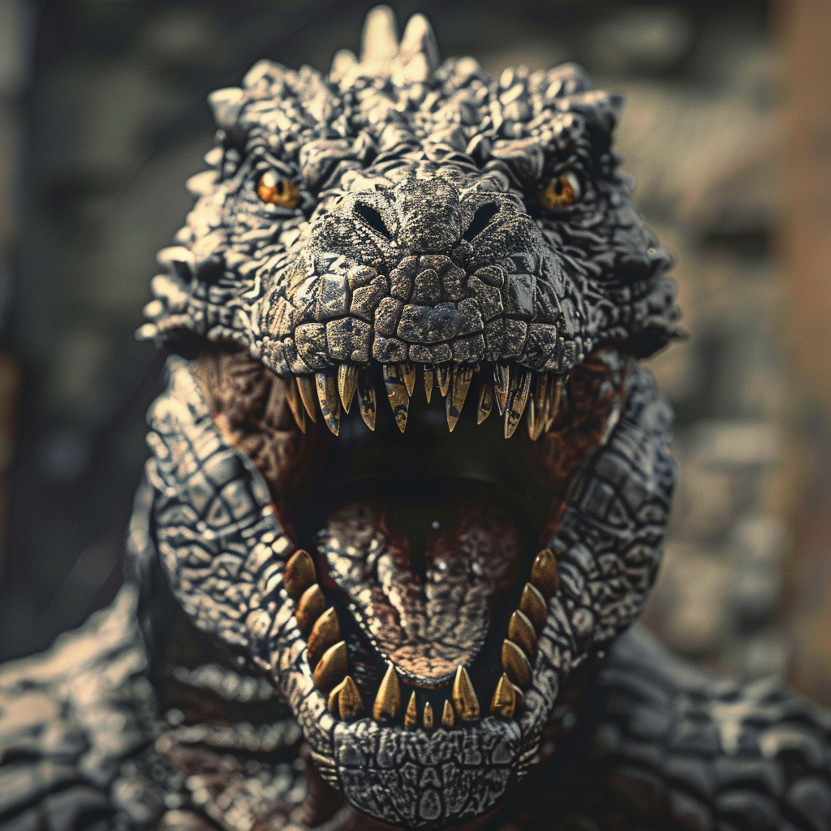
art/inspiration/alt_bier_Godzilla_head_looking_at_you_with_mouth_partially_open_52278a28-6683-4eaa-83e5-dbef07206d8f.png
