gowenrw/g0dzilla_vs/art/inspiration/alt_bier_jolly_roger_skull_and_crossed_bones_flag_with_a_smiley_87e2d1b3-ee7f-448f-9c2d-6f15fb3d7c87.png

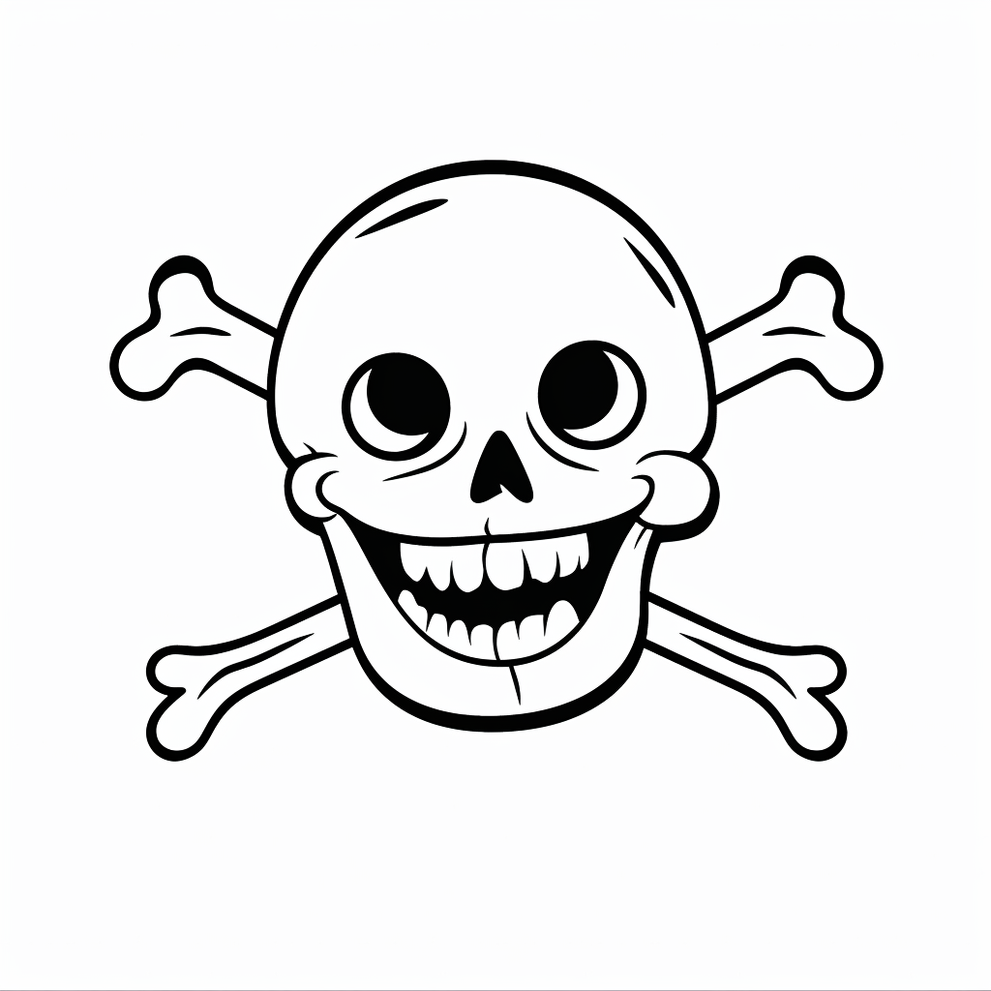
art/inspiration/alt_bier_jolly_roger_skull_and_crossed_bones_flag_with_a_smiley_87e2d1b3-ee7f-448f-9c2d-6f15fb3d7c87.png
