gowenrw/g0dzilla_vs/art/inspiration/alt_bier_lava_flowing_through_a_town_simple_lineart_in_the_styl_1f57ad40-6335-4cef-8548-7c2922ece847.png

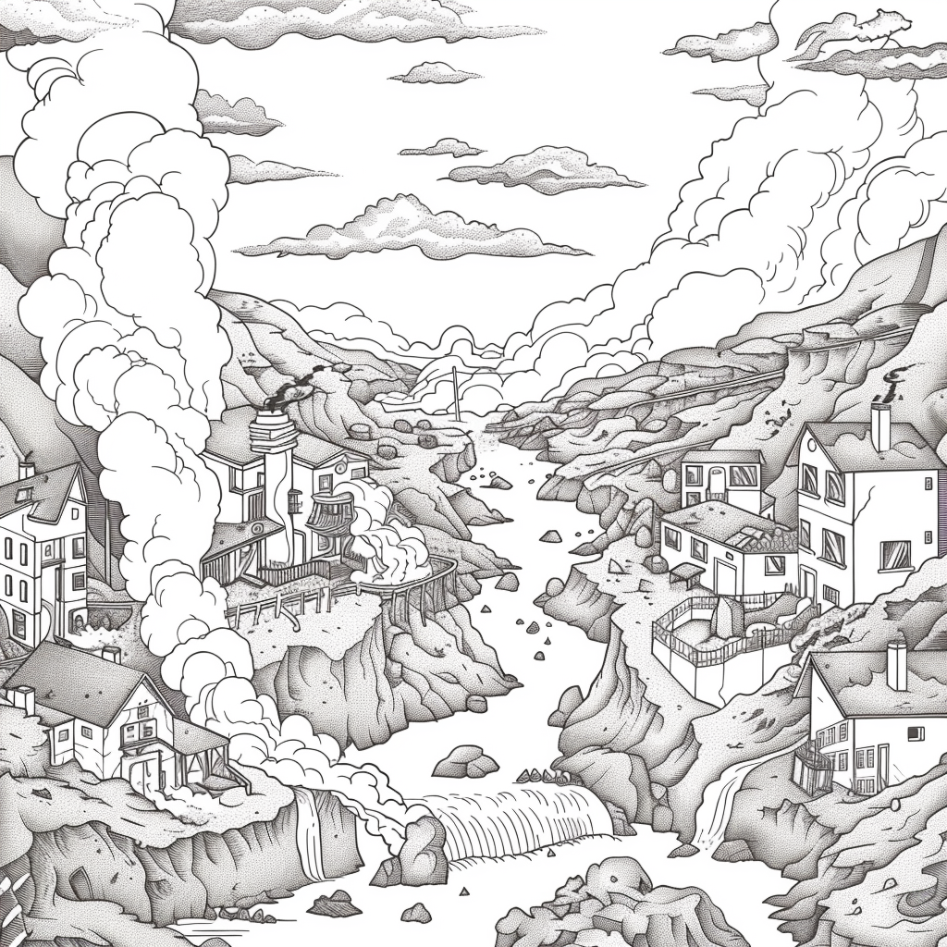
art/inspiration/alt_bier_lava_flowing_through_a_town_simple_lineart_in_the_styl_1f57ad40-6335-4cef-8548-7c2922ece847.png
