gowenrw/g0dzilla_vs/art/inspiration/alt_bier_Mechagodzilla_lineart_in_the_style_of_coloring_book_no_96901458-da0a-4c3d-b2eb-8a57ddeca94c.png

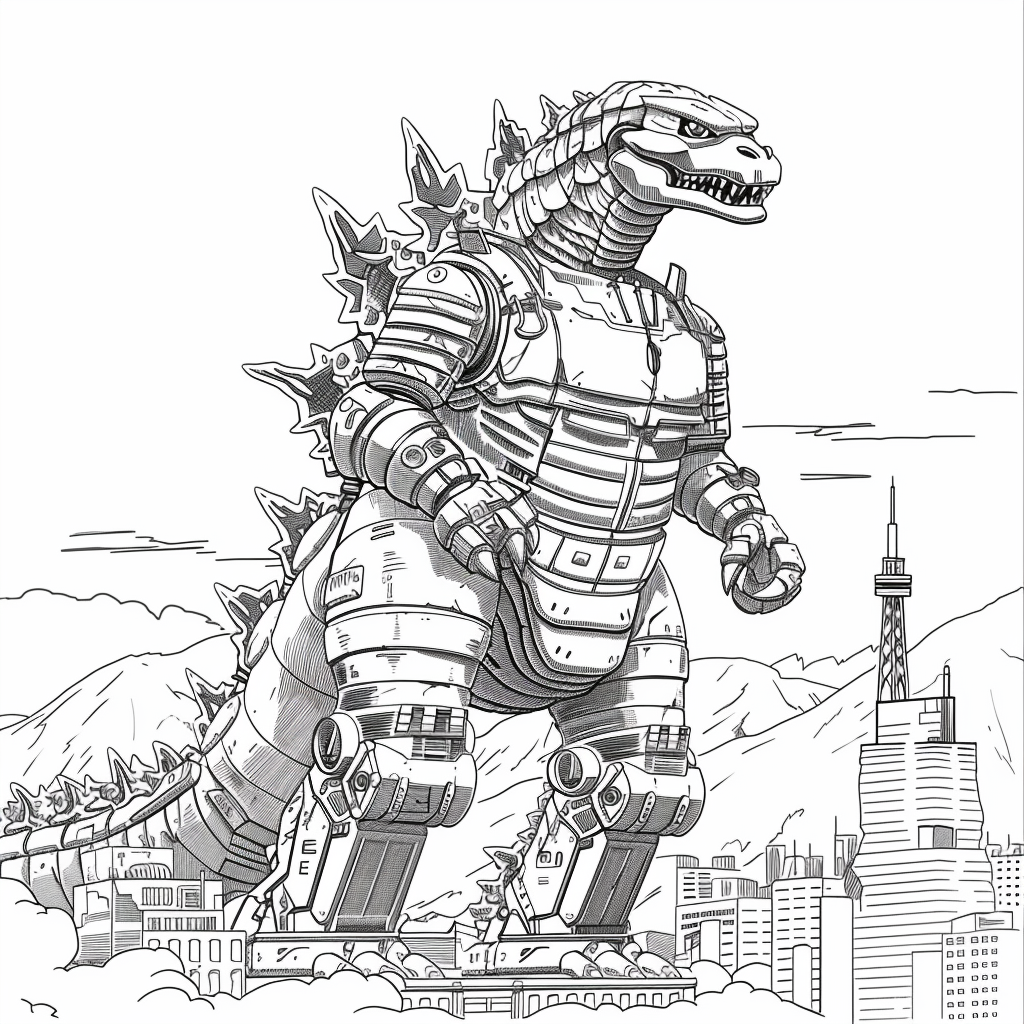
art/inspiration/alt_bier_Mechagodzilla_lineart_in_the_style_of_coloring_book_no_96901458-da0a-4c3d-b2eb-8a57ddeca94c.png
