gowenrw/g0dzilla_vs/art/inspiration/alt_bier_Mechagodzilla_lineart_in_the_style_of_coloring_book_no_f79dde8a-acef-4c68-b87b-5c6adfe6ed24.png

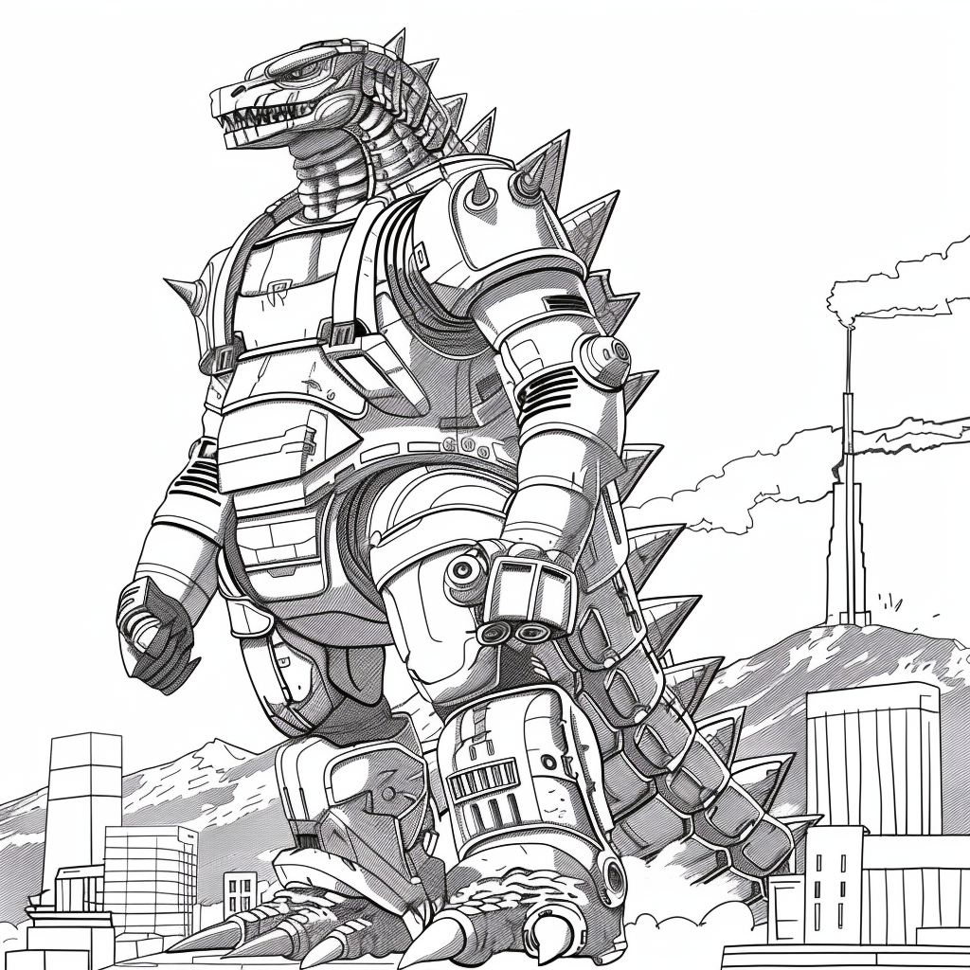
art/inspiration/alt_bier_Mechagodzilla_lineart_in_the_style_of_coloring_book_no_f79dde8a-acef-4c68-b87b-5c6adfe6ed24.png
