gowenrw/g0dzilla_vs/art/inspiration/alt_bier_Mothra_lineart_in_the_style_of_coloring_book_48df3580-6a39-4654-8a3f-f91f7401f0fe.png

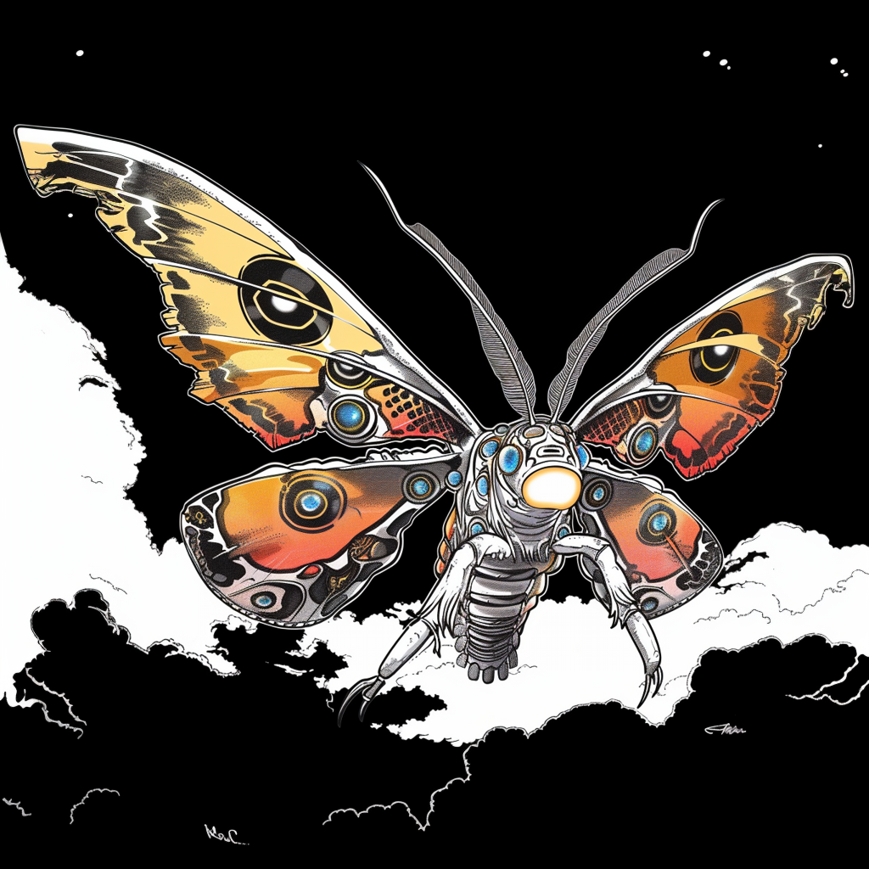
art/inspiration/alt_bier_Mothra_lineart_in_the_style_of_coloring_book_48df3580-6a39-4654-8a3f-f91f7401f0fe.png
