gowenrw/g0dzilla_vs/art/inspiration/alt_bier_Mothra_the_giant_flying_over_a_city_while_two_tiny_Gei_ae6aa13b-44c8-41c0-bbf3-922003255982.png

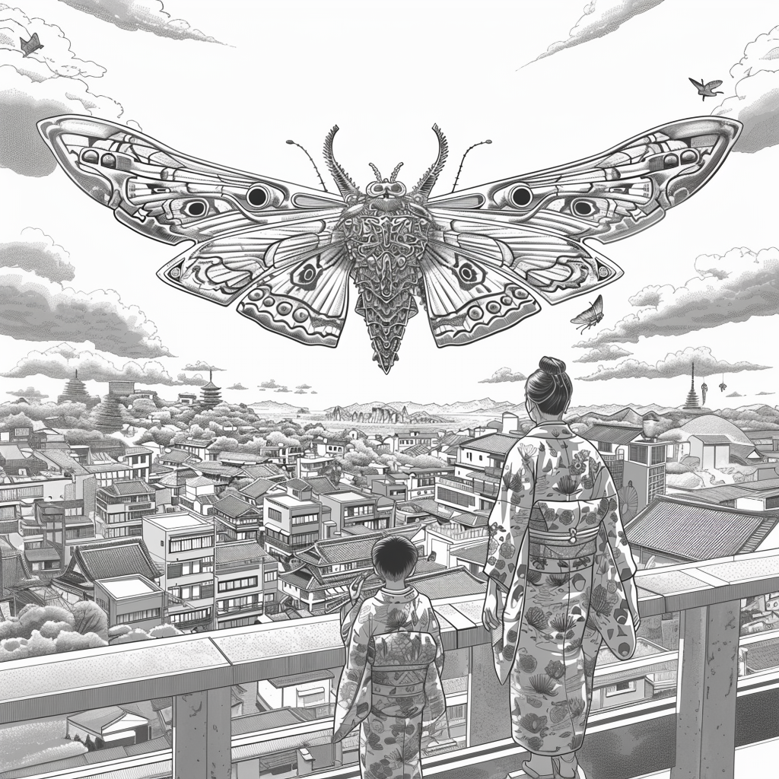
art/inspiration/alt_bier_Mothra_the_giant_flying_over_a_city_while_two_tiny_Gei_ae6aa13b-44c8-41c0-bbf3-922003255982.png
