gowenrw/g0dzilla_vs/art/inspiration/alt_bier_Mothra_using_ray_beam_while_two_tiny_Geisha_watch_in_t_78e0ea6d-941f-46cc-8e84-dd8c5e0b37d0.png

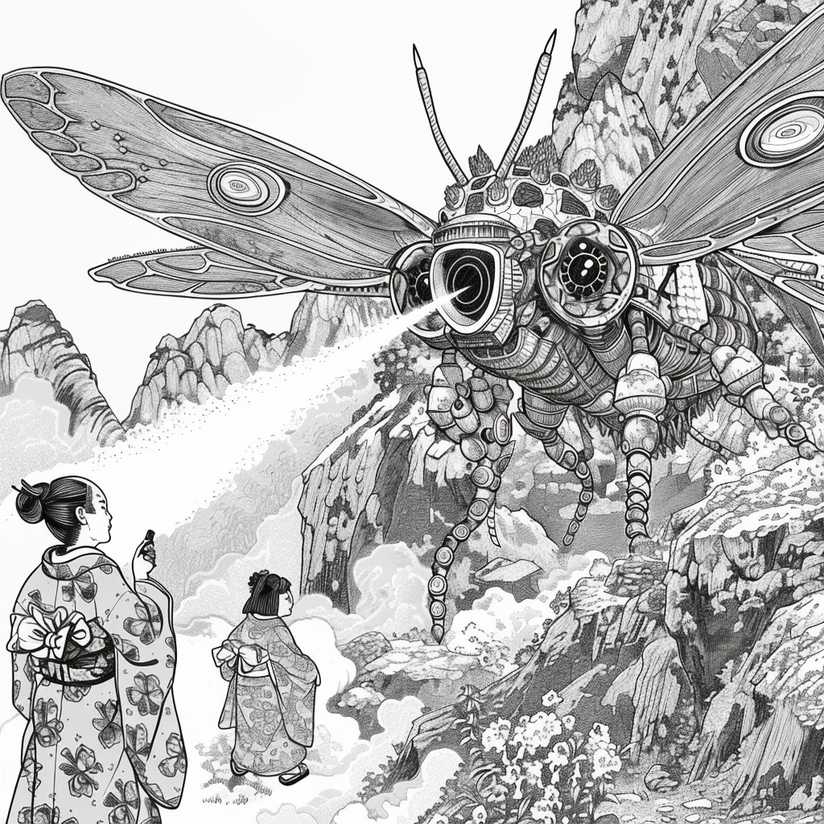
art/inspiration/alt_bier_Mothra_using_ray_beam_while_two_tiny_Geisha_watch_in_t_78e0ea6d-941f-46cc-8e84-dd8c5e0b37d0.png
