gowenrw/g0dzilla_vs/art/inspiration/alt_bier_Mothra_using_ray_beam_while_two_tiny_Geisha_watch_in_t_d98671a3-452d-44f1-8783-05ac841f5003.png

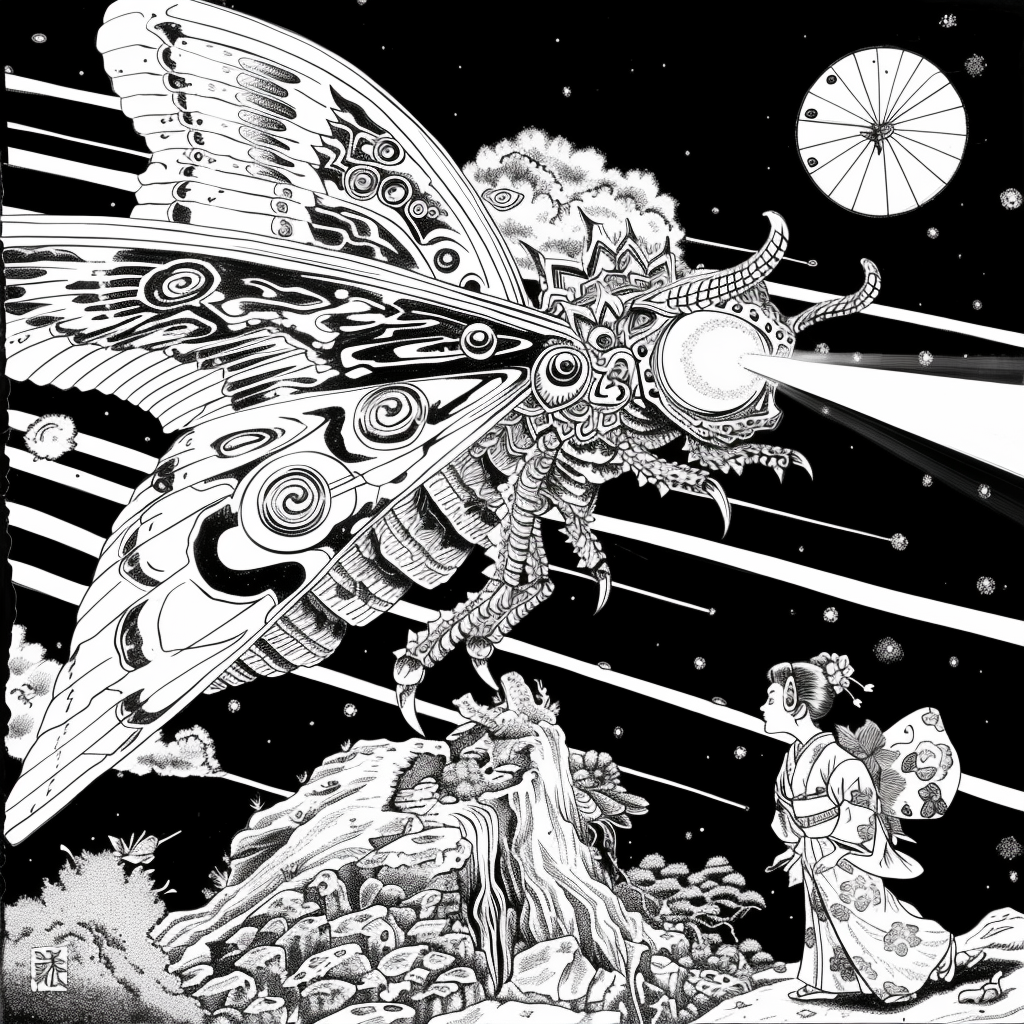
art/inspiration/alt_bier_Mothra_using_ray_beam_while_two_tiny_Geisha_watch_in_t_d98671a3-452d-44f1-8783-05ac841f5003.png
