gowenrw/g0dzilla_vs/art/inspiration/alt_bier_shoreline_of_a_city_with_a_dock_with_fishing_boats_moo_64d2cbc6-8444-4f8b-a3ce-91c841158d9d.png

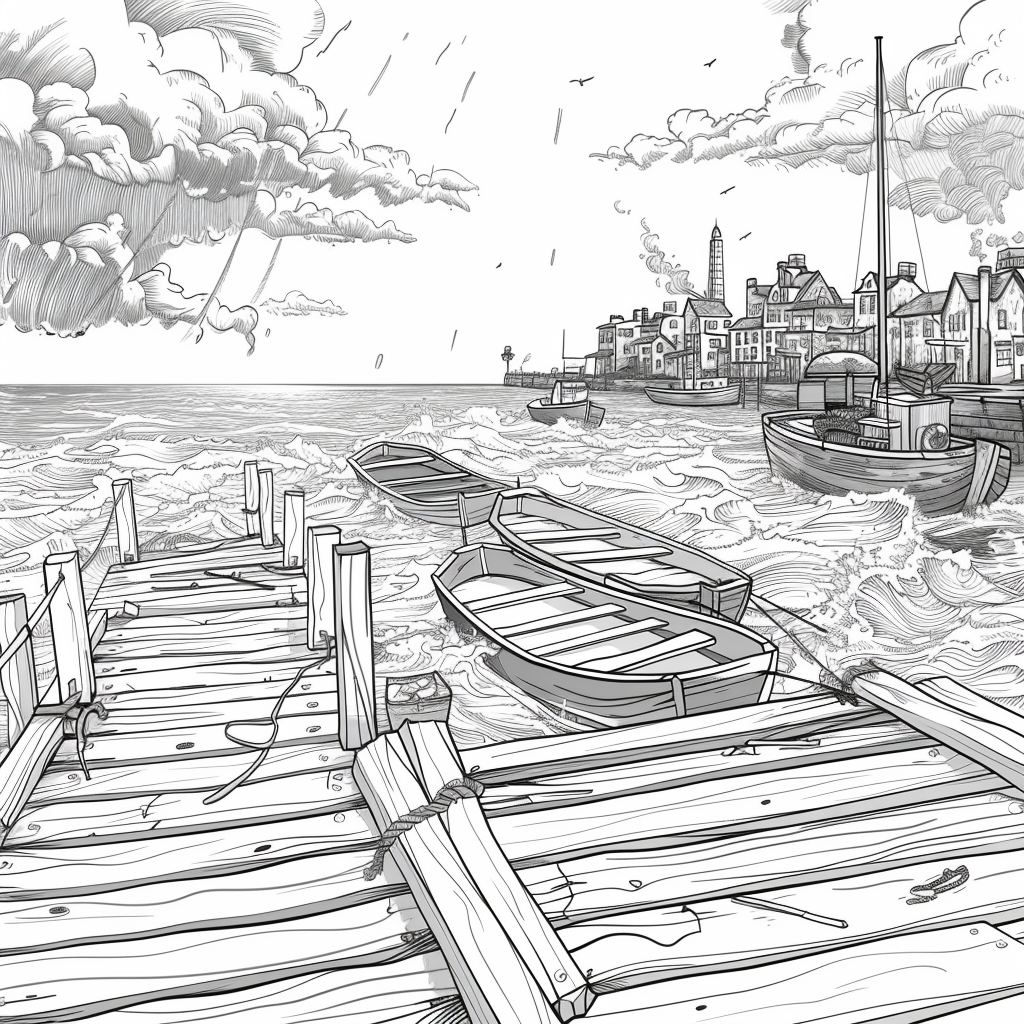
art/inspiration/alt_bier_shoreline_of_a_city_with_a_dock_with_fishing_boats_moo_64d2cbc6-8444-4f8b-a3ce-91c841158d9d.png
