gowenrw/g0dzilla_vs/art/inspiration/alt_bier_small_nuclear_bomb_mushroom_cloud_rising_over_a_partia_0d8cb61f-c745-4f72-831a-7eec388ae7d0.png

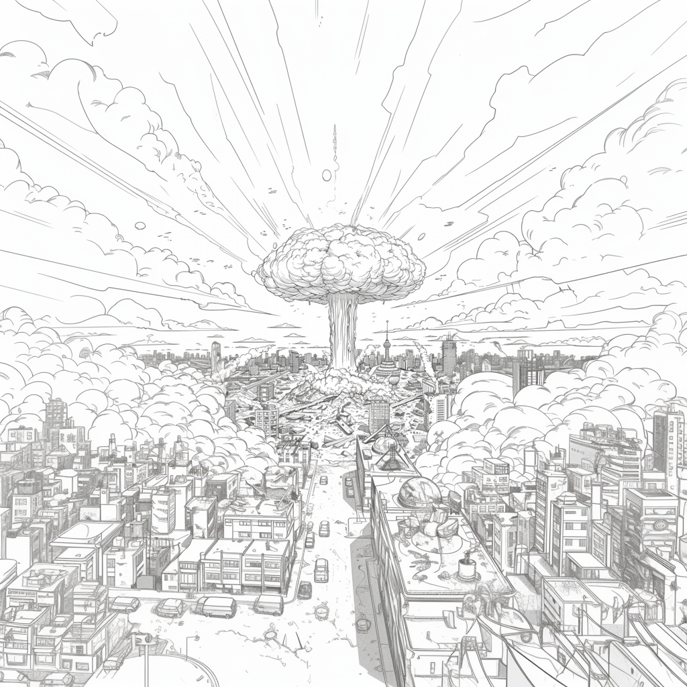
art/inspiration/alt_bier_small_nuclear_bomb_mushroom_cloud_rising_over_a_partia_0d8cb61f-c745-4f72-831a-7eec388ae7d0.png
