gowenrw/g0dzilla_vs/art/inspiration/alt_bier_small_nuclear_bomb_mushroom_cloud_rising_over_a_partia_11aa1017-53c8-43d2-bed4-64161a7c9c63.png

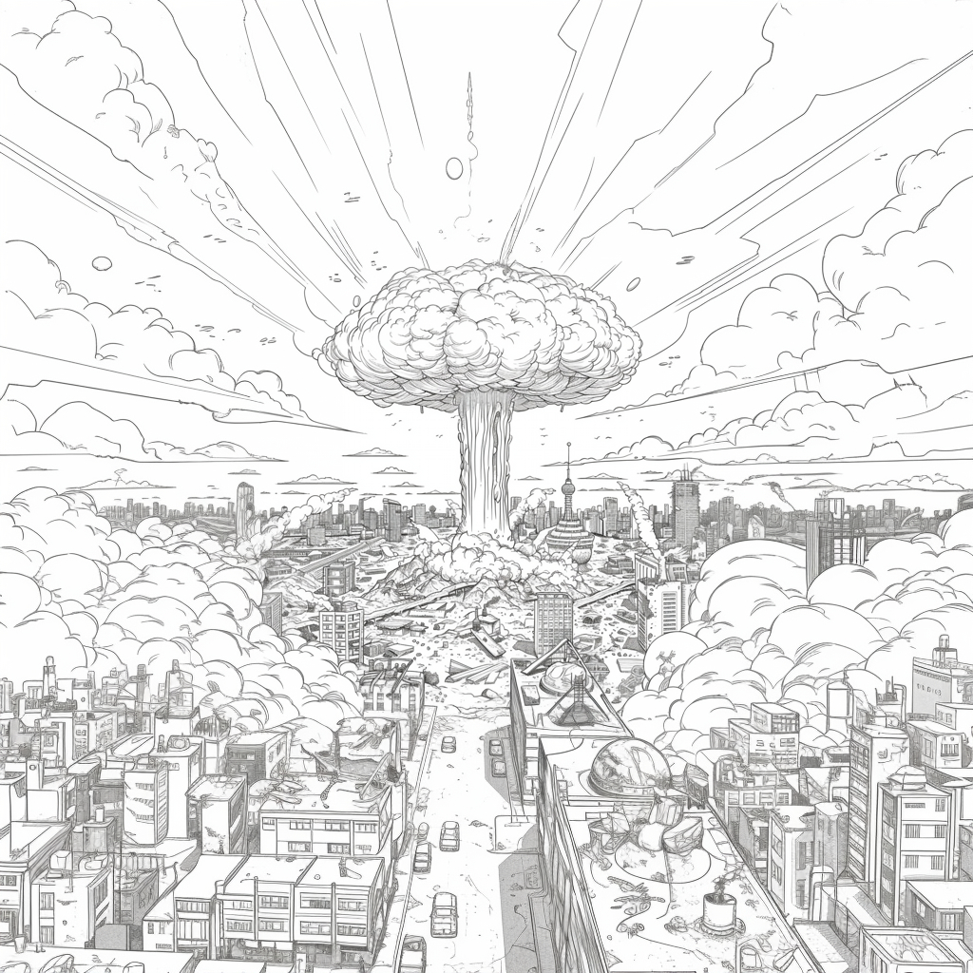
art/inspiration/alt_bier_small_nuclear_bomb_mushroom_cloud_rising_over_a_partia_11aa1017-53c8-43d2-bed4-64161a7c9c63.png
