gowenrw/g0dzilla_vs/art/inspiration/alt_bier_the_monster_Hedorah_shambling_in_front_of_a_city_simpl_2c43f70f-2d32-4b4f-991f-c1513a4c3c92.png

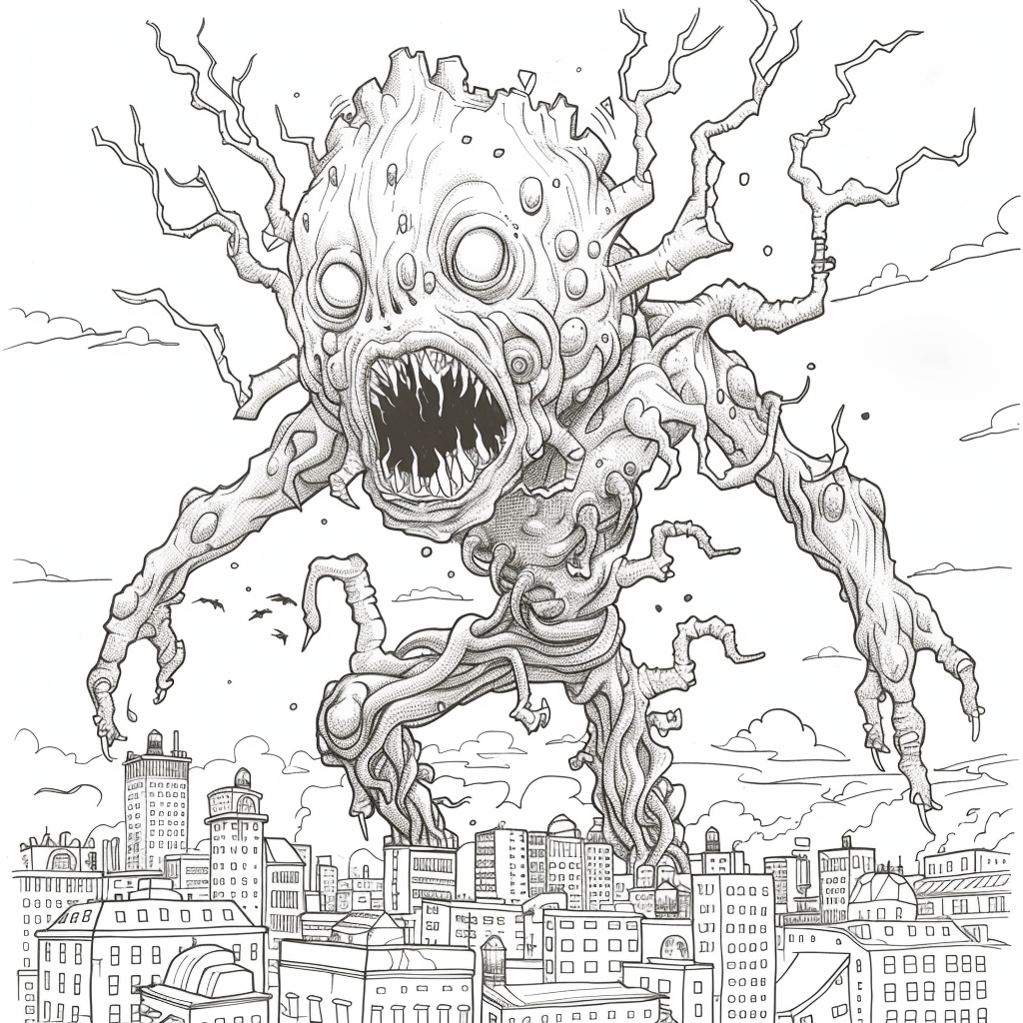
art/inspiration/alt_bier_the_monster_Hedorah_shambling_in_front_of_a_city_simpl_2c43f70f-2d32-4b4f-991f-c1513a4c3c92.png
