gowenrw/g0dzilla_vs/art/inspiration/alt_bier_the_monster_Hedorah_shambling_in_front_of_a_city_simpl_acc92da0-928f-4acc-9d33-e61beeaf953a.png

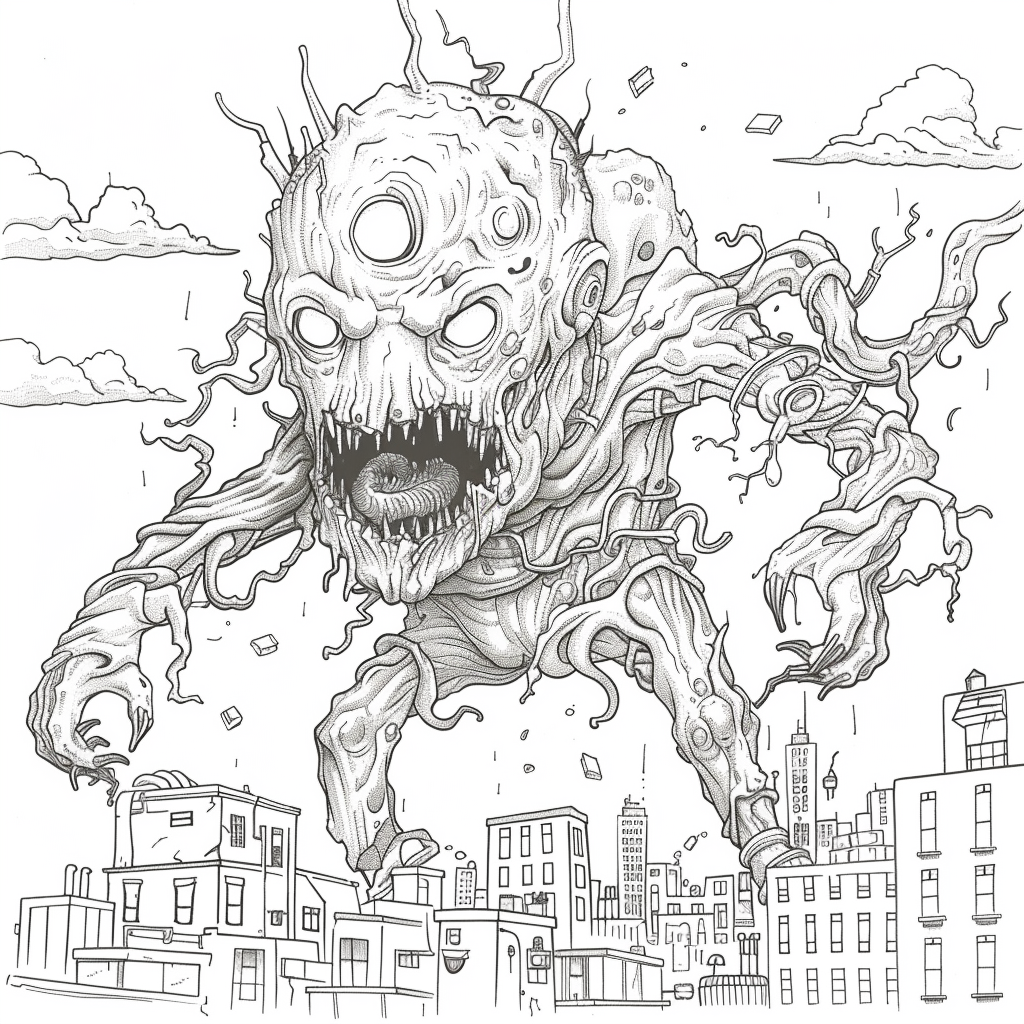
art/inspiration/alt_bier_the_monster_Hedorah_shambling_in_front_of_a_city_simpl_acc92da0-928f-4acc-9d33-e61beeaf953a.png
