gowenrw/g0dzilla_vs/art/inspiration/alt_bier_the_monster_Hedorah_shambling_in_front_of_a_city_simpl_ddb33e47-8375-4678-a6fa-bb4bef1c6af9.png

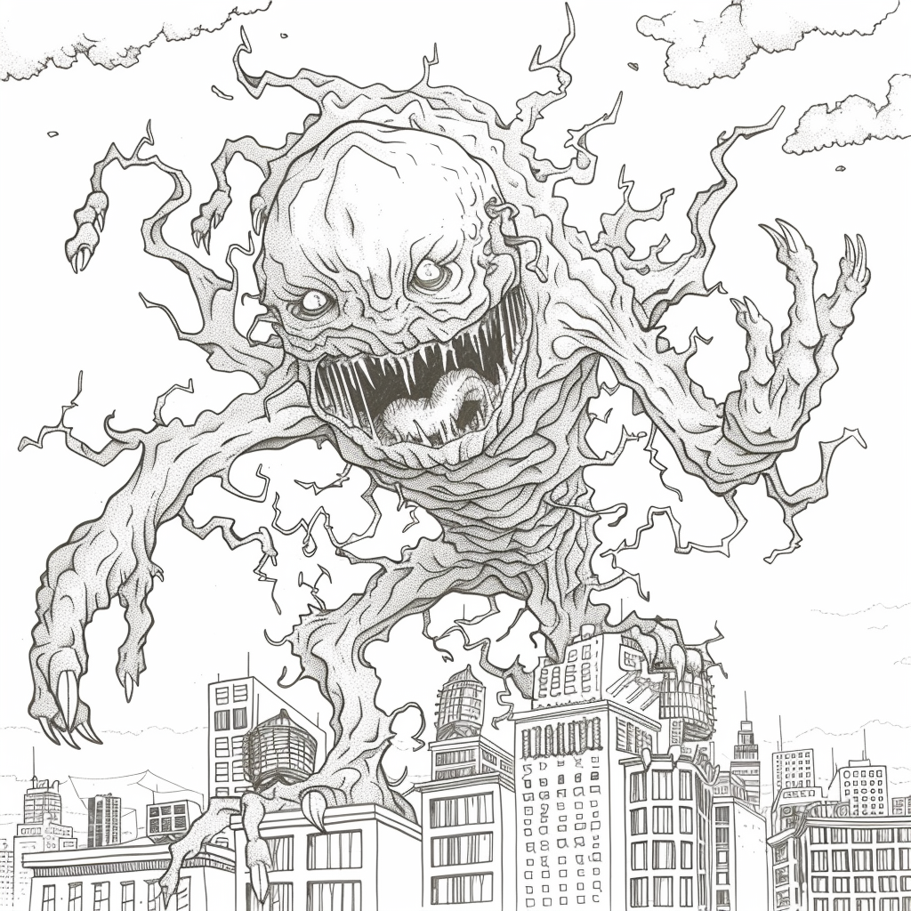
art/inspiration/alt_bier_the_monster_Hedorah_shambling_in_front_of_a_city_simpl_ddb33e47-8375-4678-a6fa-bb4bef1c6af9.png
