gowenrw/g0dzilla_vs/art/inspiration/alt_bier_The_monster_Rodan_sitting_atop_a_volcano_that_is_slowl_3f09e8ae-7736-4b16-860c-a2afcce04a64.png

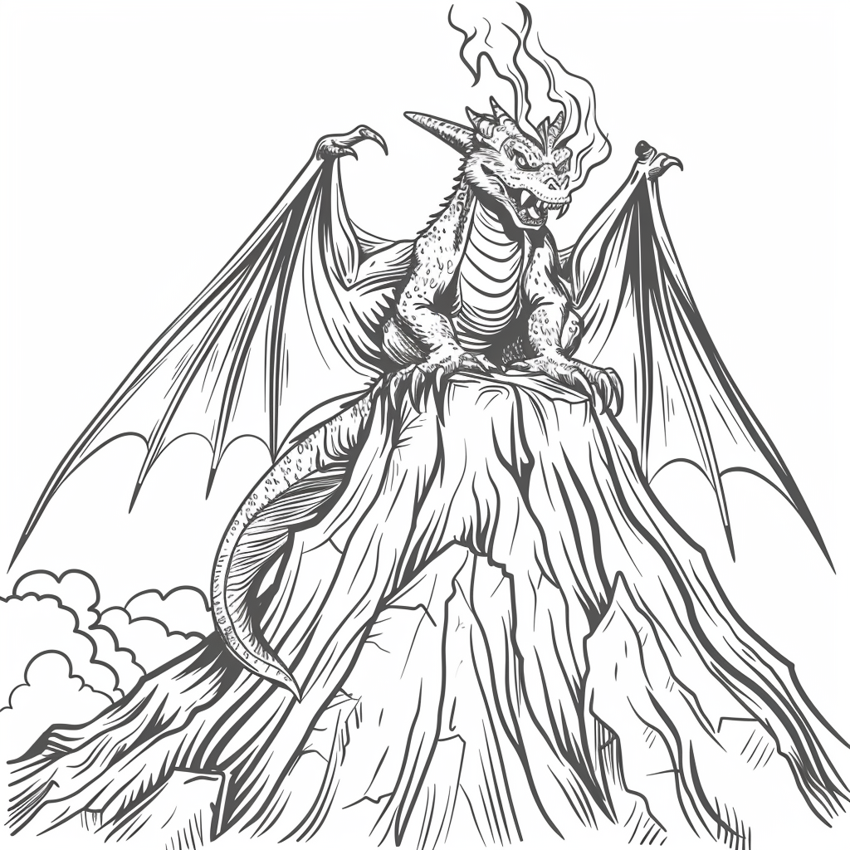
art/inspiration/alt_bier_The_monster_Rodan_sitting_atop_a_volcano_that_is_slowl_3f09e8ae-7736-4b16-860c-a2afcce04a64.png
