gowenrw/g0dzilla_vs/art/inspiration/alt_bier_The_monster_Rodan_sitting_atop_a_volcano_that_is_slowl_23420ab5-489f-4014-96b2-38bbddb8e027.png

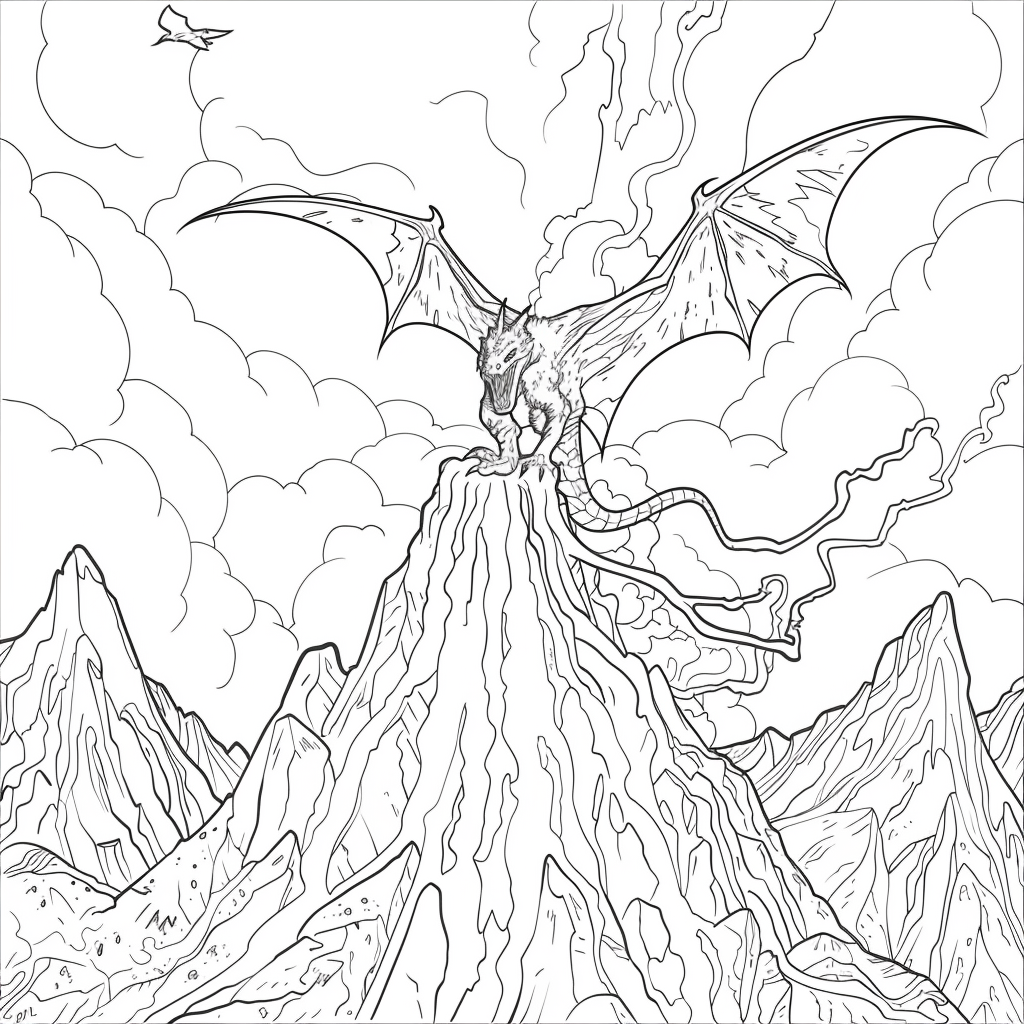
art/inspiration/alt_bier_The_monster_Rodan_sitting_atop_a_volcano_that_is_slowl_23420ab5-489f-4014-96b2-38bbddb8e027.png
