gowenrw/g0dzilla_vs/art/inspiration/alt_bier_The_monster_Rodan_sitting_atop_a_volcano_that_is_spill_4df87373-bd6a-4001-beb0-b10062e9341d.png

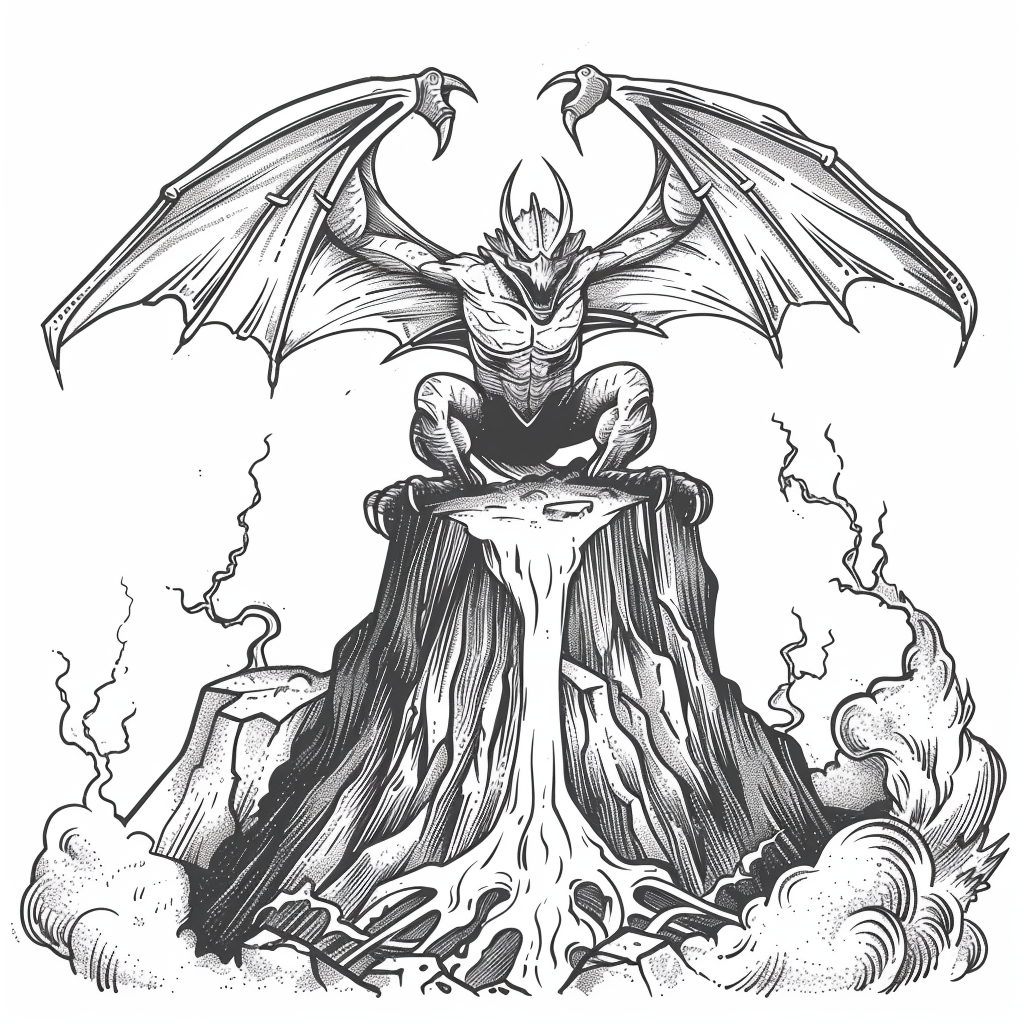
art/inspiration/alt_bier_The_monster_Rodan_sitting_atop_a_volcano_that_is_spill_4df87373-bd6a-4001-beb0-b10062e9341d.png
