gowenrw/g0dzilla_vs/art/inspiration/alt_bier_the_three_headed_monster_Ghidorah_emerging_from_a_ligh_da27f297-d812-4c6a-9261-70f89c6ff449.png

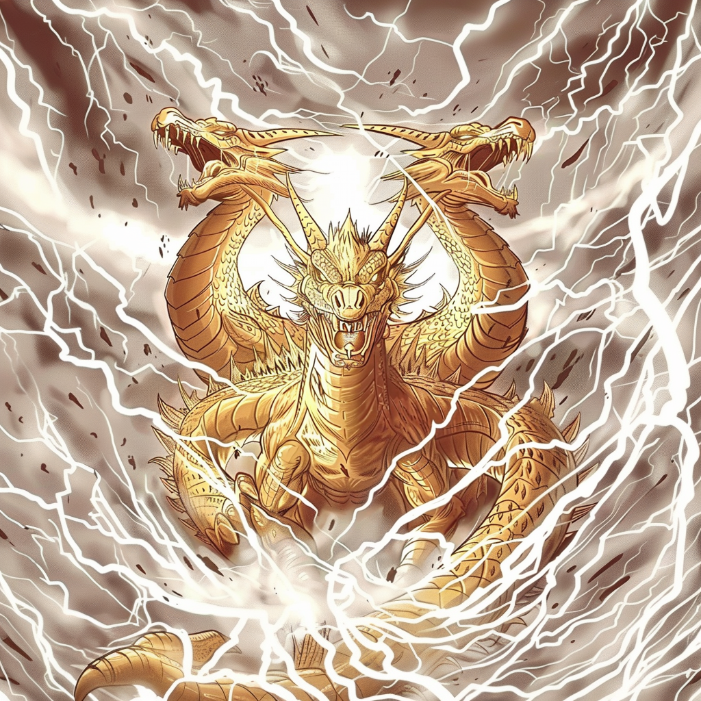
art/inspiration/alt_bier_the_three_headed_monster_Ghidorah_emerging_from_a_ligh_da27f297-d812-4c6a-9261-70f89c6ff449.png
