gowenrw/g0dzilla_vs/art/inspiration/alt_bier_the_three_headed_monster_Ghidorah_standing_on_a_hill_w_38749248-adf1-4c30-9d63-d67eda2d2715.png

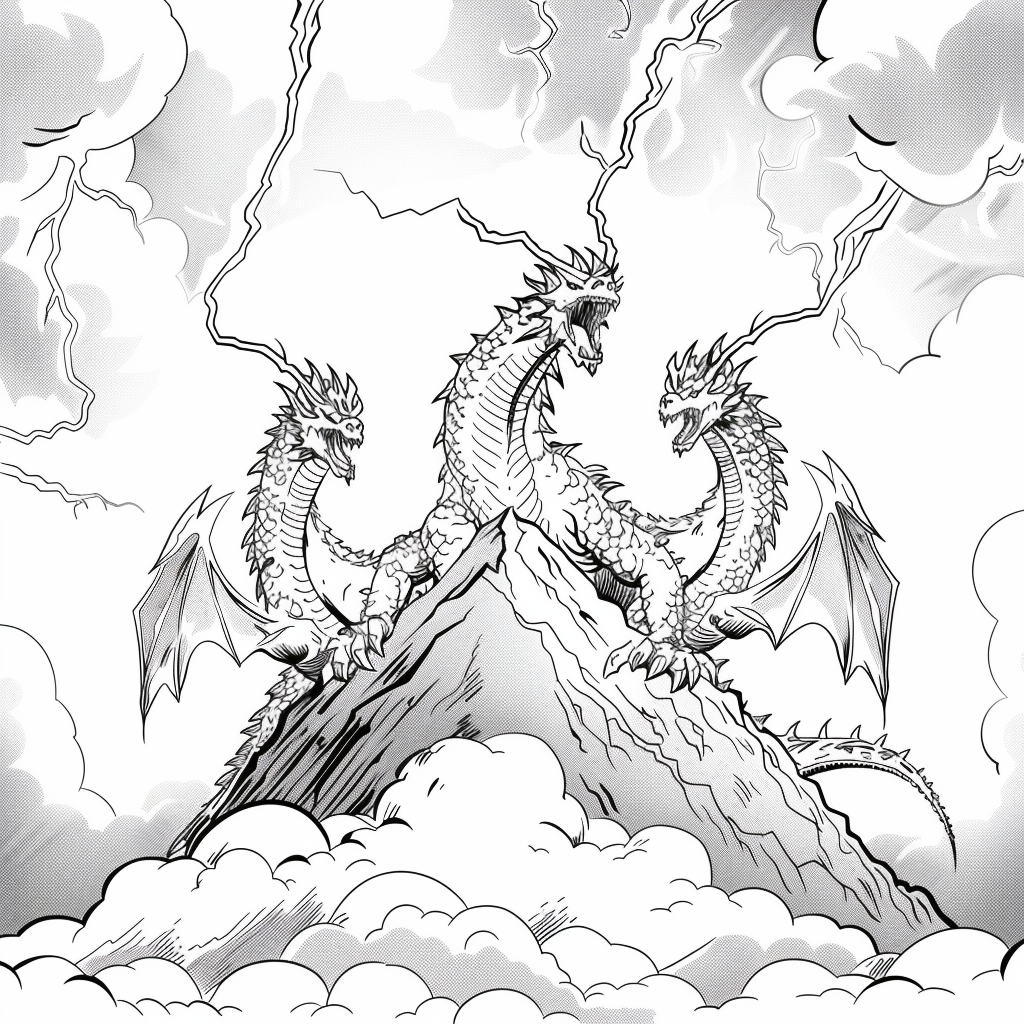
art/inspiration/alt_bier_the_three_headed_monster_Ghidorah_standing_on_a_hill_w_38749248-adf1-4c30-9d63-d67eda2d2715.png
