gowenrw/g0dzilla_vs/art/inspiration/alt_bier_the_three_headed_monster_Ghidorah_standing_on_a_hill_w_a1d58abf-09e7-48d5-892f-40f7e4255292.png

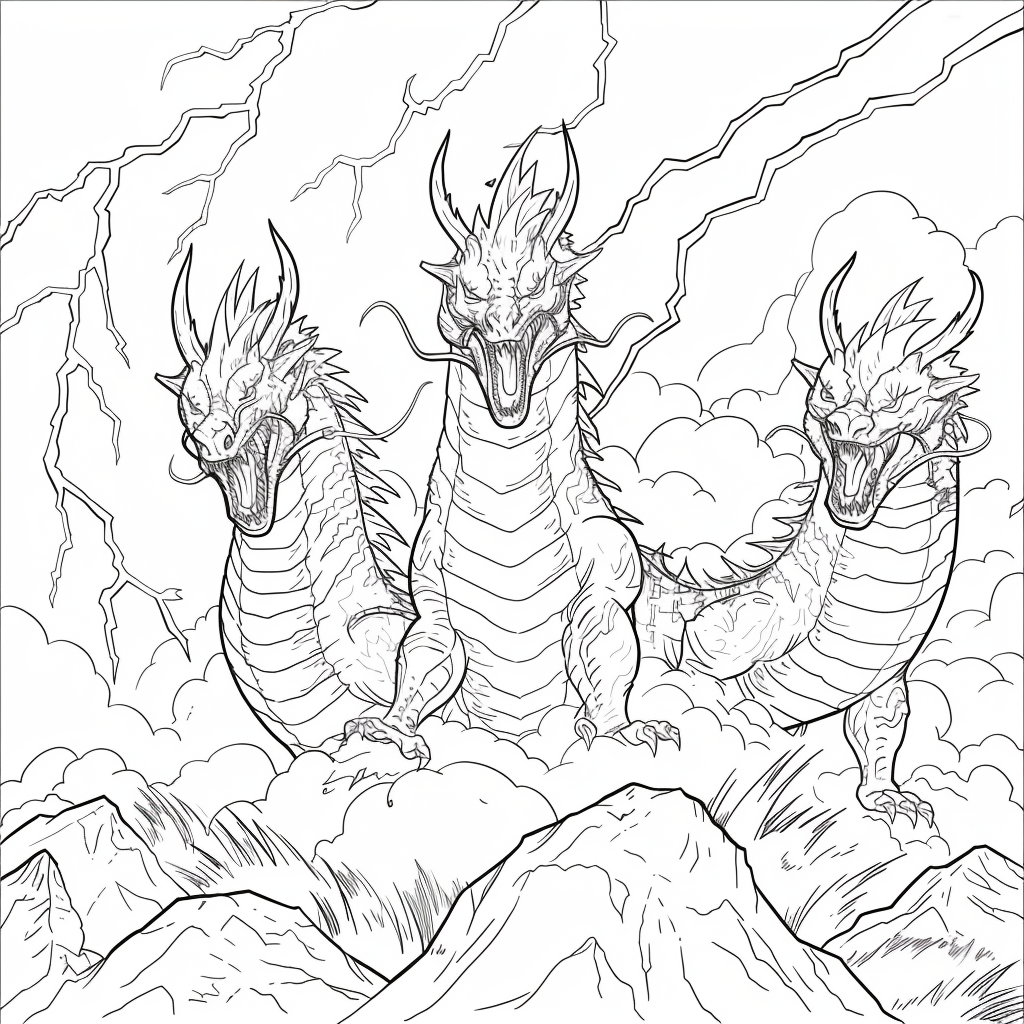
art/inspiration/alt_bier_the_three_headed_monster_Ghidorah_standing_on_a_hill_w_a1d58abf-09e7-48d5-892f-40f7e4255292.png
