gowenrw/g0dzilla_vs/art/inspiration/alt_bier_the_three_headed_monster_Ghidorah_standing_on_a_hill_w_ab96b2ea-8f36-4bd5-af4f-45d2f77b7892.png

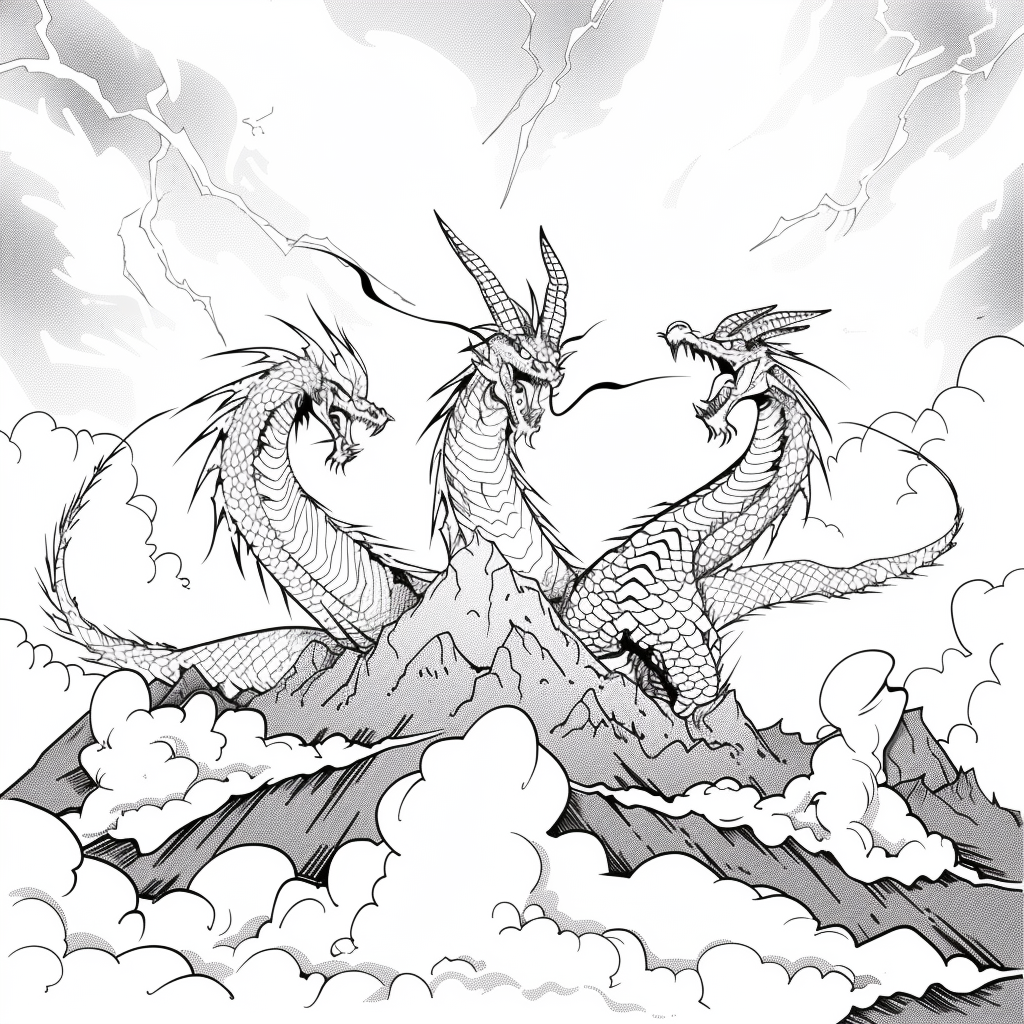
art/inspiration/alt_bier_the_three_headed_monster_Ghidorah_standing_on_a_hill_w_ab96b2ea-8f36-4bd5-af4f-45d2f77b7892.png
