gowenrw/g0dzilla_vs/art/inspiration/alt_bier_two_japanese_women_in_kimonos_cheering_as_they_look_at_8d69dab7-7077-4dbb-a567-56c513052c19.png

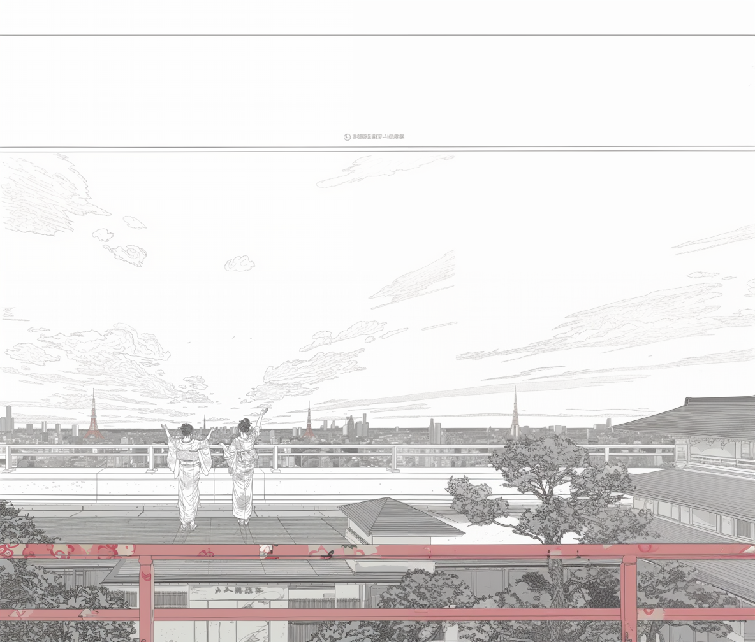
art/inspiration/alt_bier_two_japanese_women_in_kimonos_cheering_as_they_look_at_8d69dab7-7077-4dbb-a567-56c513052c19.png
