gowenrw/g0dzilla_vs/art/inspiration/alt_bier_two_japanese_women_in_kimonos_cheering_as_they_look_at_c8125bd4-6653-4464-a1d2-c411e7dfe8c3.png

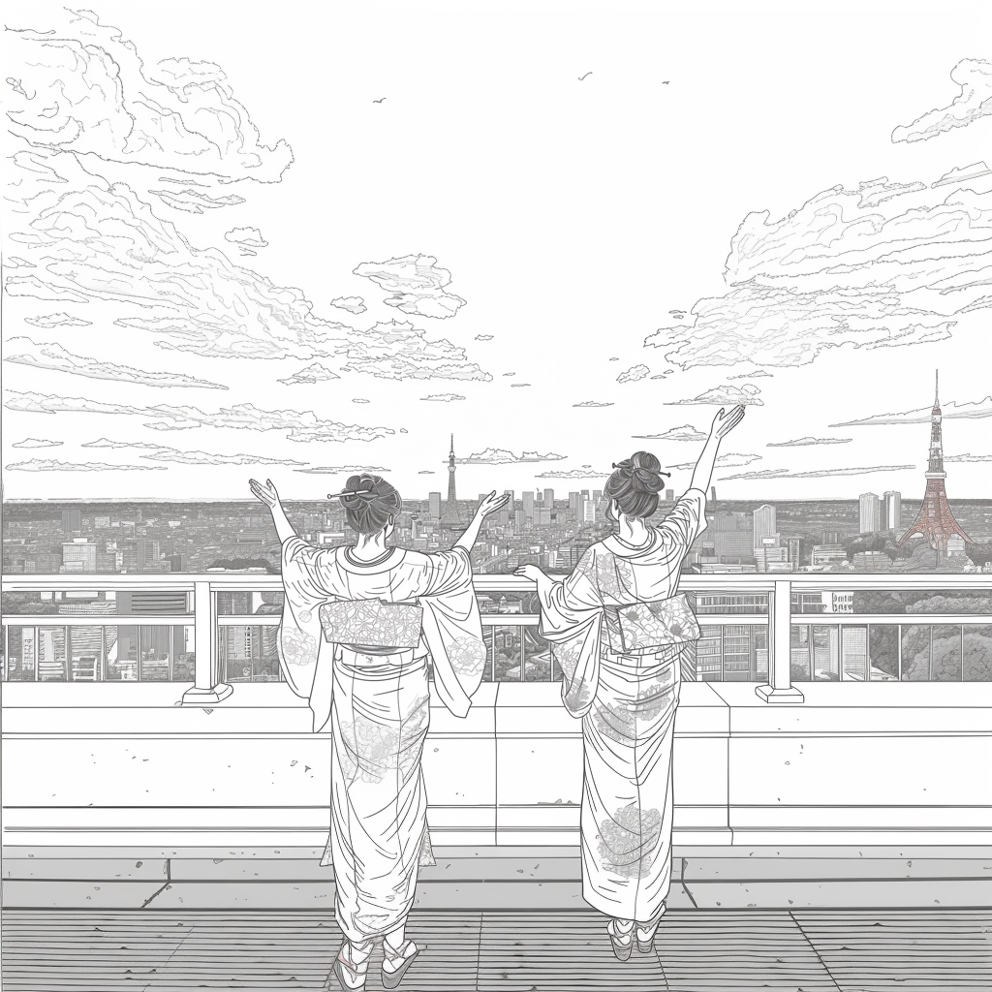
art/inspiration/alt_bier_two_japanese_women_in_kimonos_cheering_as_they_look_at_c8125bd4-6653-4464-a1d2-c411e7dfe8c3.png
