gowenrw/g0dzilla_vs/art/inspiration/alt_bier_view_of_the_back_of_Godzillas_head_as_he_walks_away_si_11cde483-af34-421c-b089-007aa3099c01.png

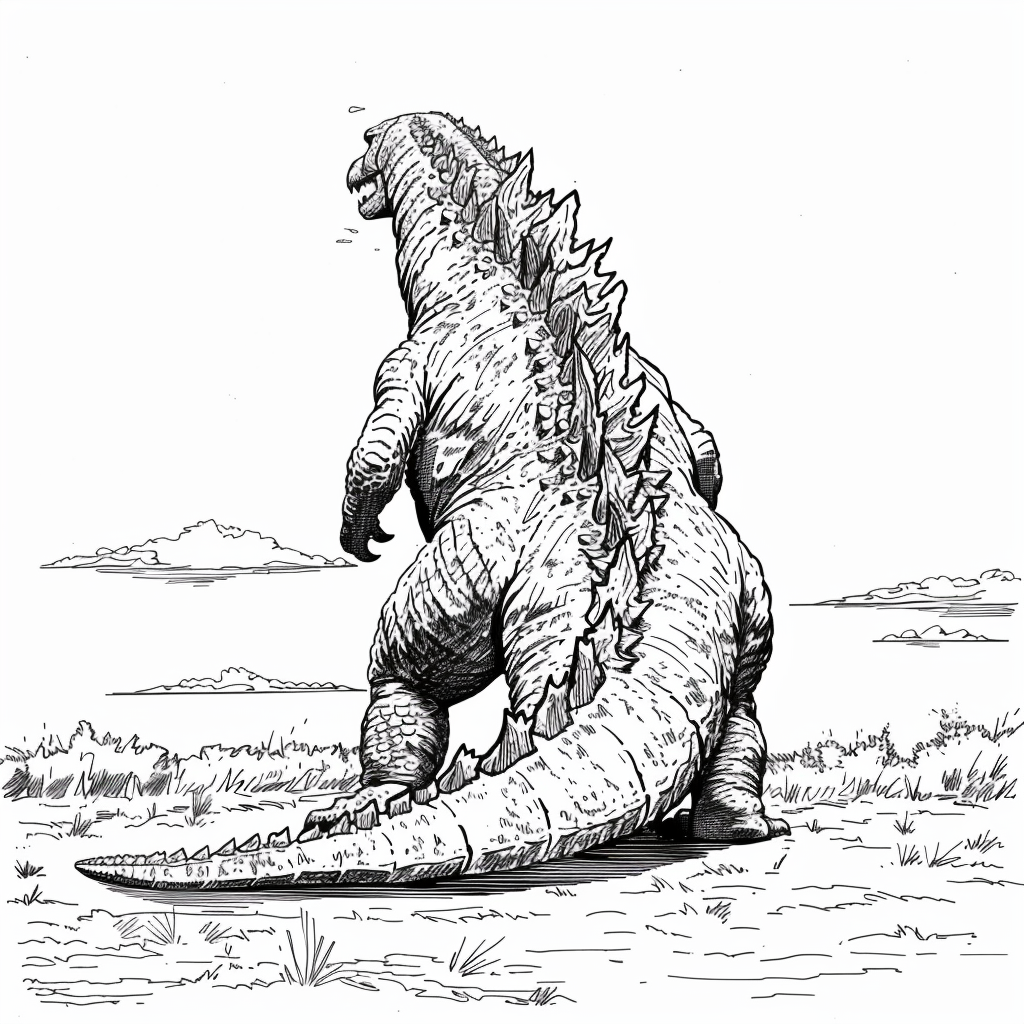
art/inspiration/alt_bier_view_of_the_back_of_Godzillas_head_as_he_walks_away_si_11cde483-af34-421c-b089-007aa3099c01.png
