gowenrw/g0dzilla_vs/art/inspiration/alt_bier_view_of_the_back_of_Godzillas_head_as_he_walks_away_si_c63f2a78-0717-4a35-bdf2-cee73eae2c97.png

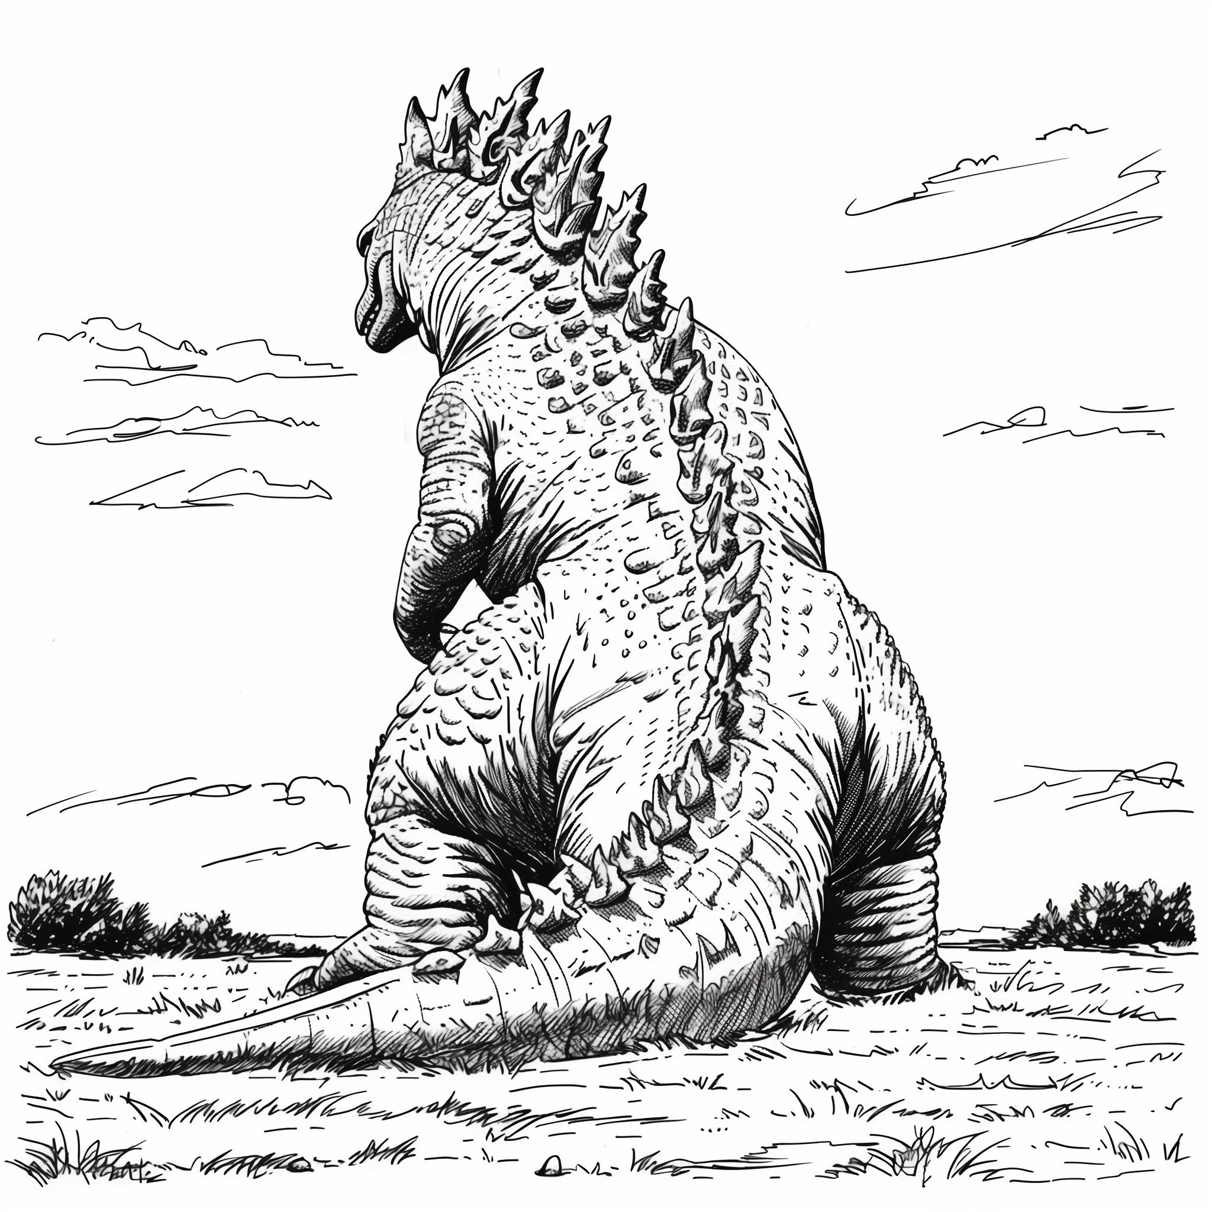
art/inspiration/alt_bier_view_of_the_back_of_Godzillas_head_as_he_walks_away_si_c63f2a78-0717-4a35-bdf2-cee73eae2c97.png
