gowenrw/g0dzilla_vs/art/inspiration/alt_bier_warrior_standing_on_a_large_pile_of_skulls_and_bones_s_6db6fc5f-2844-4cbb-b06e-7c1a0aa0c682.png

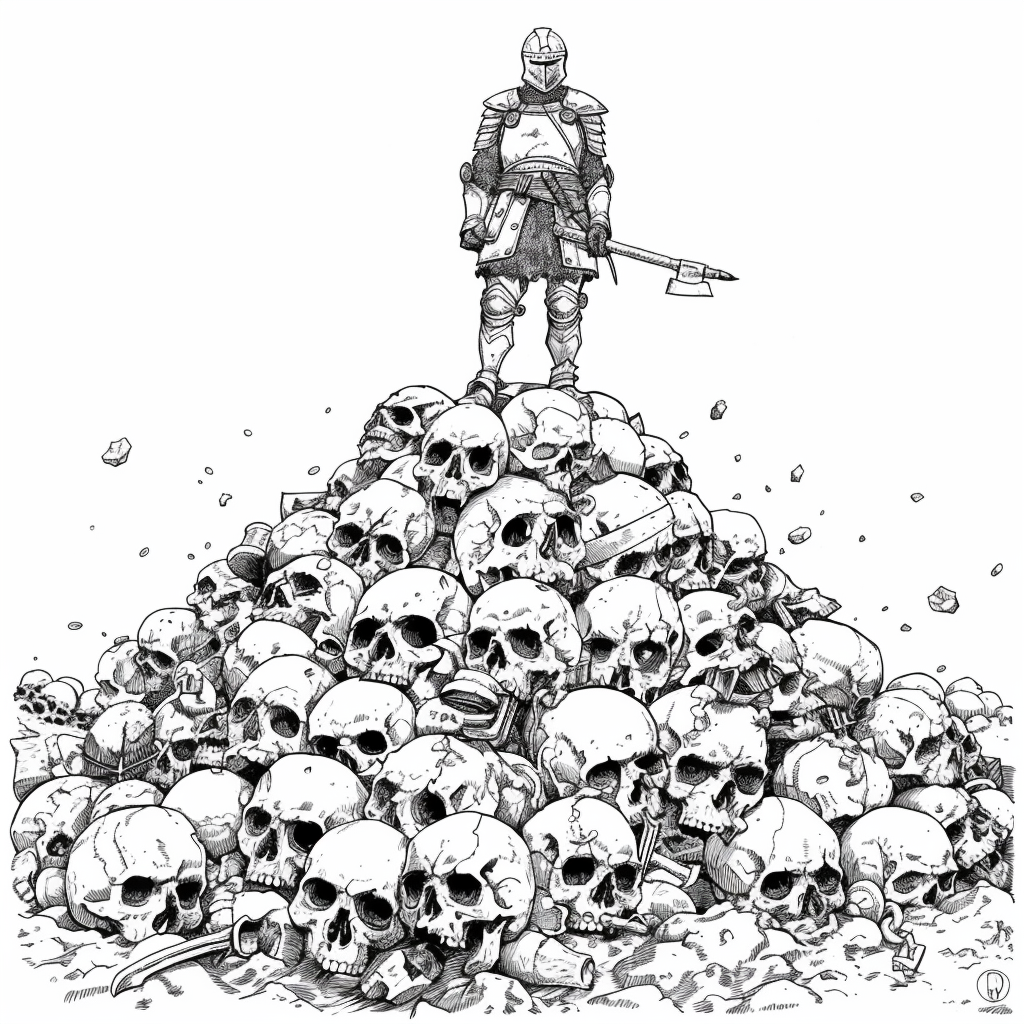
art/inspiration/alt_bier_warrior_standing_on_a_large_pile_of_skulls_and_bones_s_6db6fc5f-2844-4cbb-b06e-7c1a0aa0c682.png
