gowenrw/g0dzilla_vs/art/inspiration/GodzillavsGigan_1972.webp

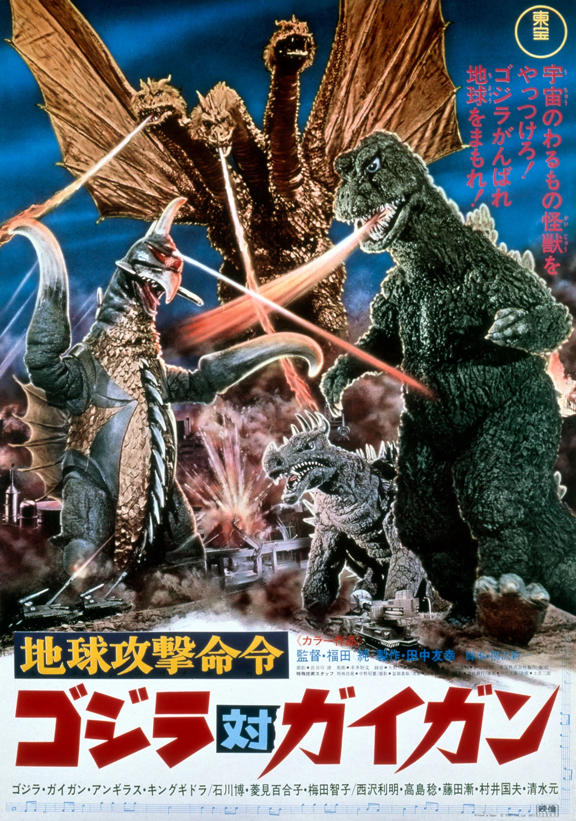
art/inspiration/GodzillavsGigan_1972.webp
