gowenrw/g0dzilla_vs/art/lanyard-proof.png

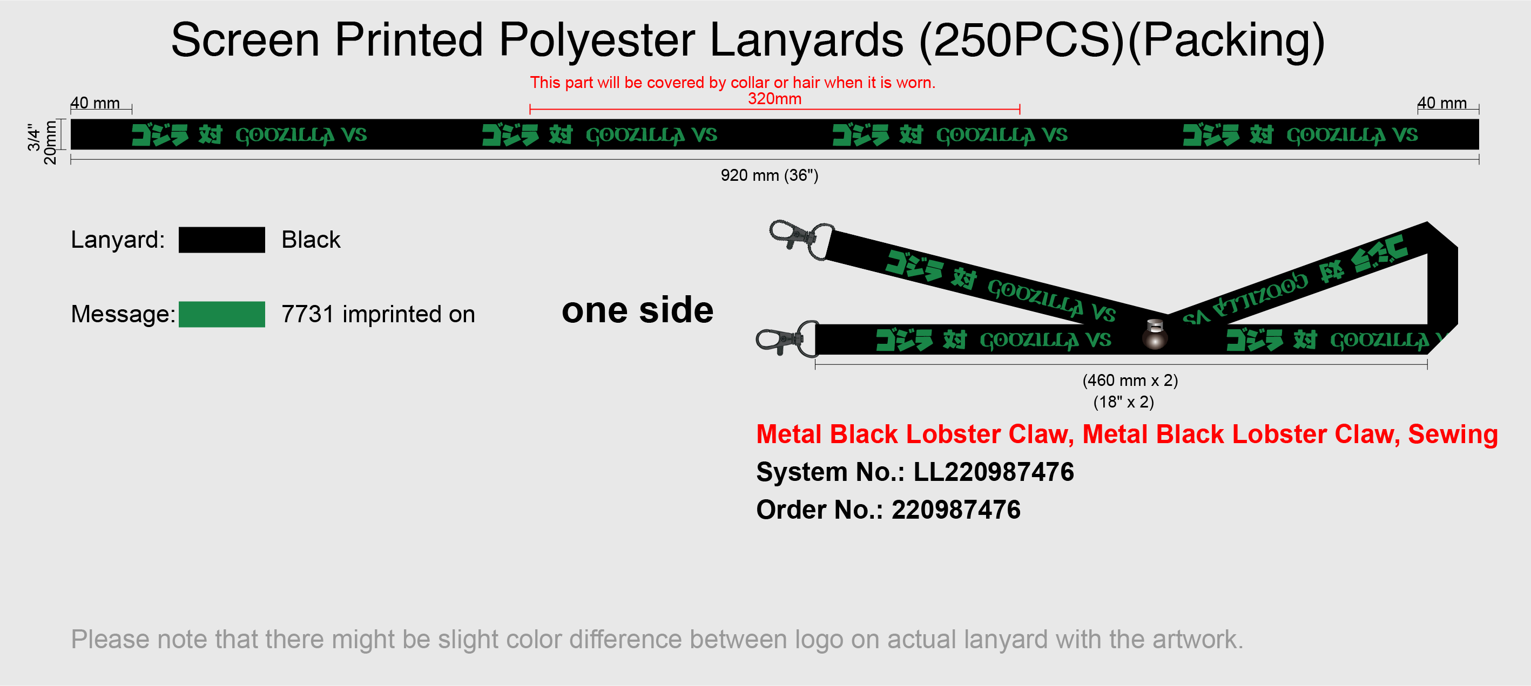
art/lanyard-proof.png
