gowenrw/g0dzilla_vs/art/mothra.jpg

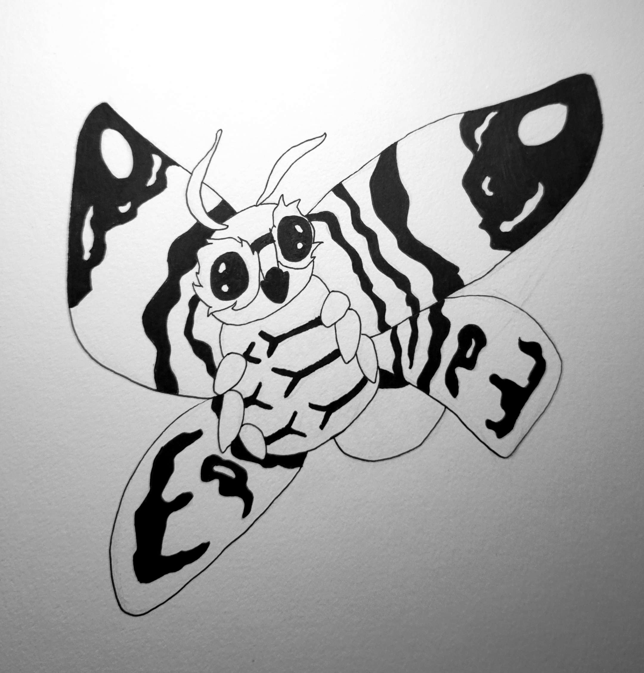
art/mothra.jpg
