gowenrw/g0dzilla_vs/docs/images/20240629_143737.gif

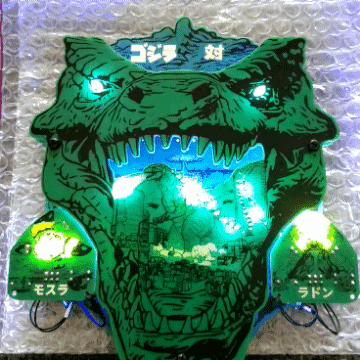
docs/images/20240629_143737.gif
