gowenrw/g0dzilla_vs/docs/images/20240701_172126.jpg

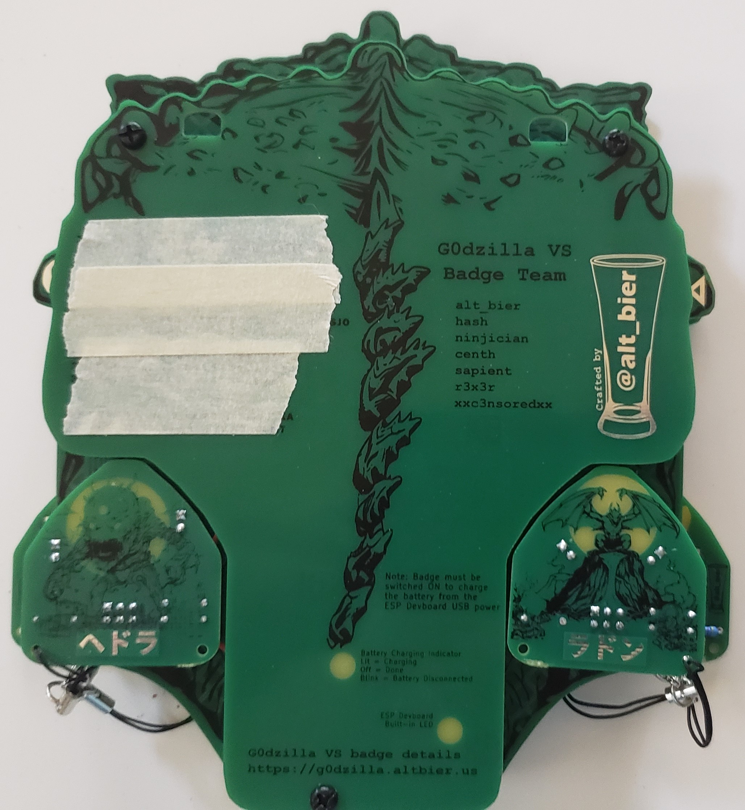
docs/images/20240701_172126.jpg
