gowenrw/g0dzilla_vs/docs/images/20240701_172140.jpg

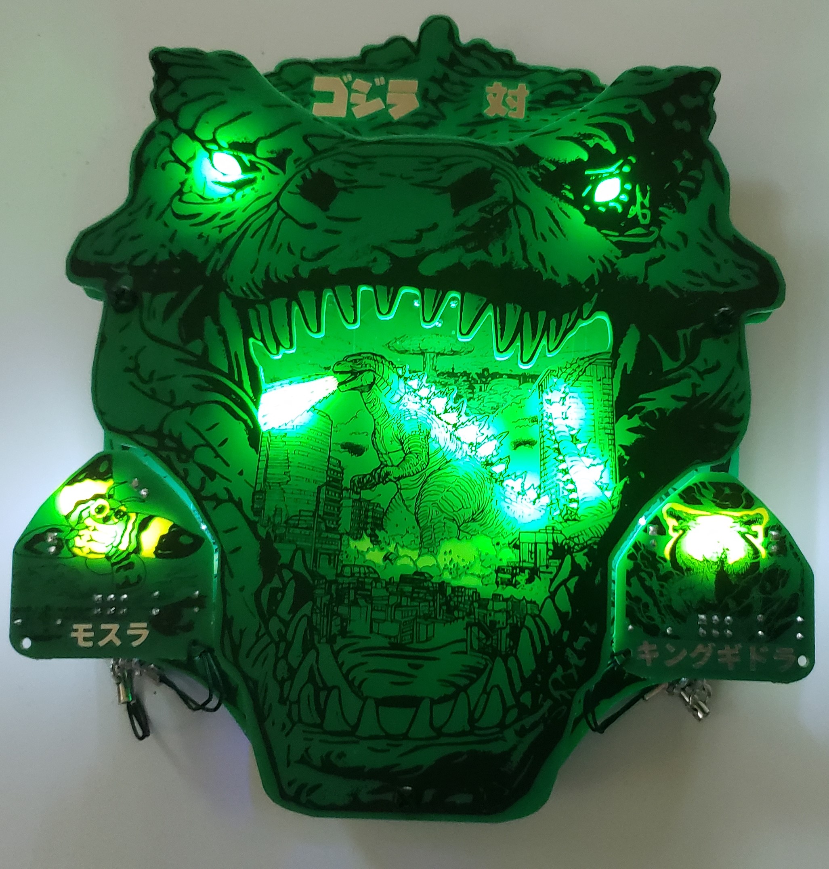
docs/images/20240701_172140.jpg
