gowenrw/g0dzilla_vs/docs/images/20240701_172142.jpg

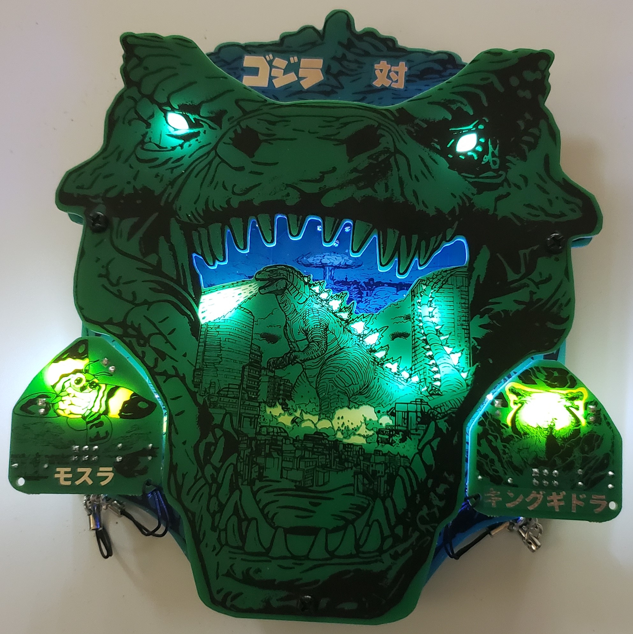
docs/images/20240701_172142.jpg
