gowenrw/g0dzilla_vs/docs/images/20240710_230409.jpg

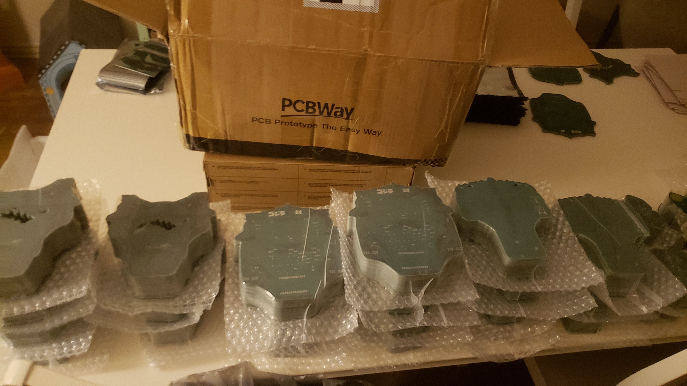
docs/images/20240710_230409.jpg
