gowenrw/g0dzilla_vs/docs/images/20240711_084048.jpg

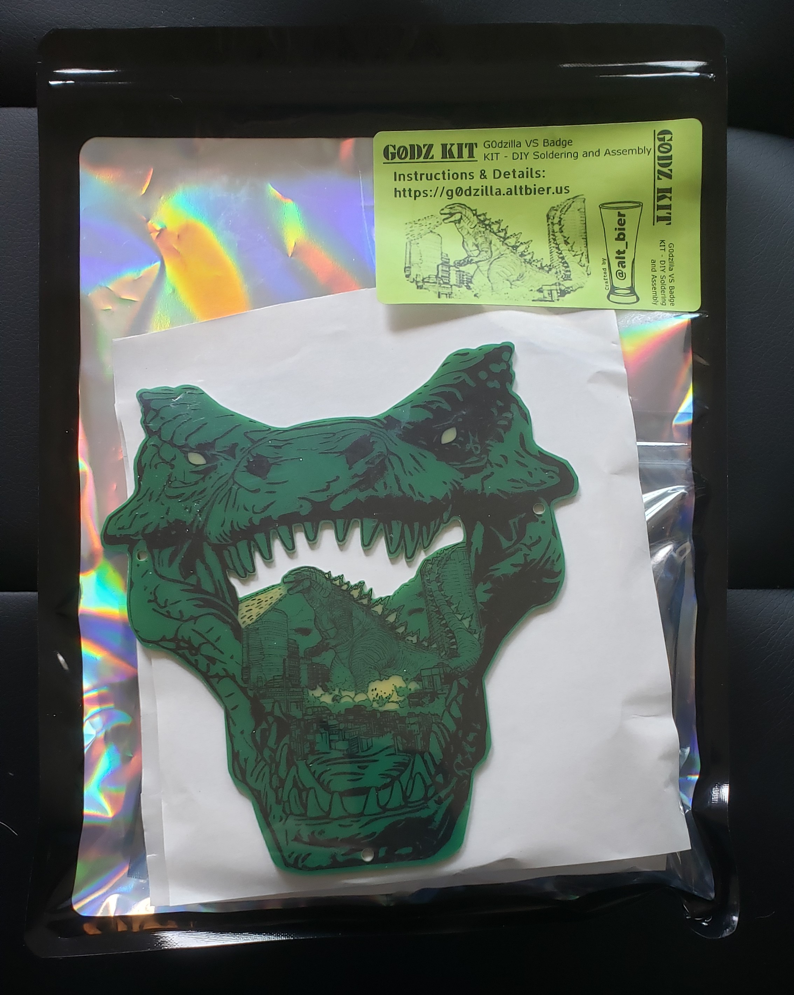
docs/images/20240711_084048.jpg
