gowenrw/g0dzilla_vs/docs/images/20240711_084146.jpg

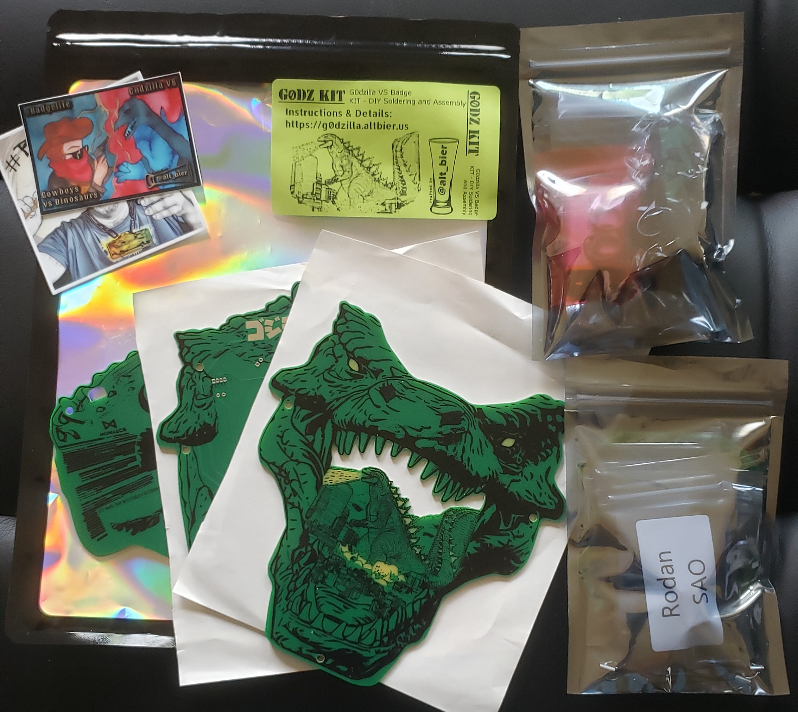
docs/images/20240711_084146.jpg
