gowenrw/g0dzilla_vs/docs/images/20240711_084327.jpg

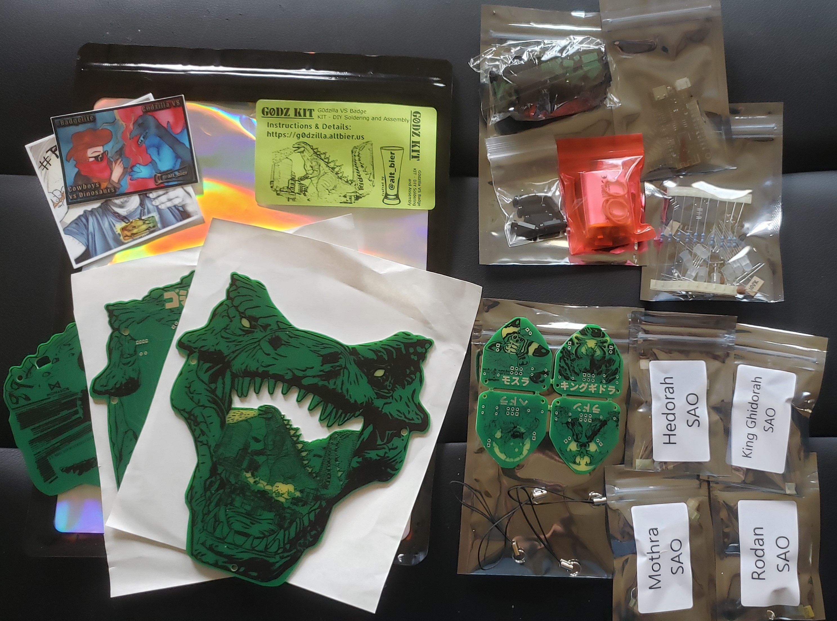
docs/images/20240711_084327.jpg
