gowenrw/g0dzilla_vs/docs/images/g0dzilla_vs_sao1_schematic_rev1.jpg

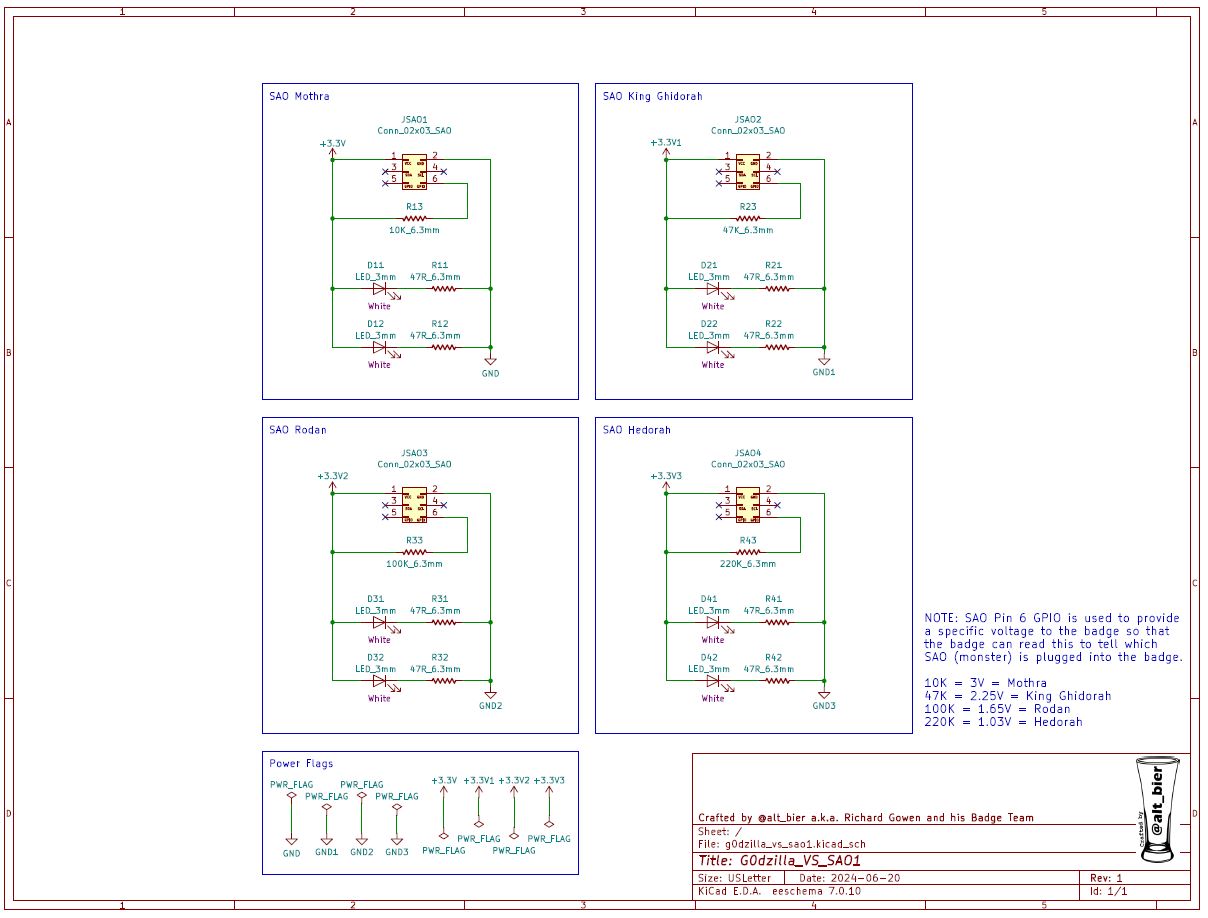
docs/images/g0dzilla_vs_sao1_schematic_rev1.jpg
