gowenrw/g0dzilla_vs/eda/g0dzilla_vs/snapshots/g0dzilla_vs_3D_proto23.jpg

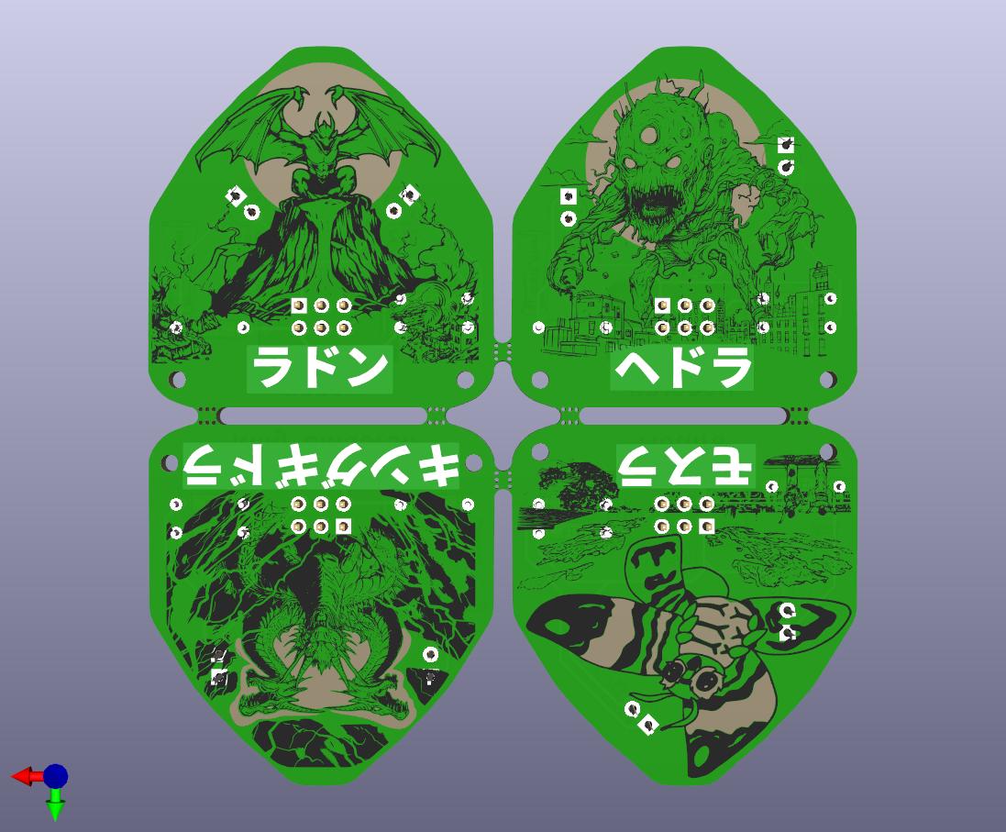
eda/g0dzilla_vs/snapshots/g0dzilla_vs_3D_proto23.jpg
