gowenrw/g0dzilla_vs/eda/g0dzilla_vs/3d_models/BatteryHolder_2466_1xAAA.step

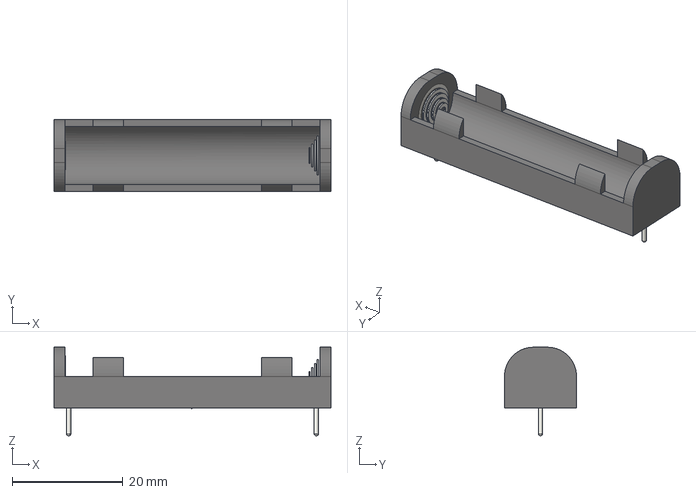
[picture p159: CAD file, 2024-03-11]
eda/g0dzilla_vs/3d_models/BatteryHolder_2466_1xAAA.step
50.0 x 13.0 x 16.0 mm
