gowenrw/g0dzilla_vs/eda/g0dzilla_vs/3d_models/PinHeader_1x08_P2.54mm_Vertical.step

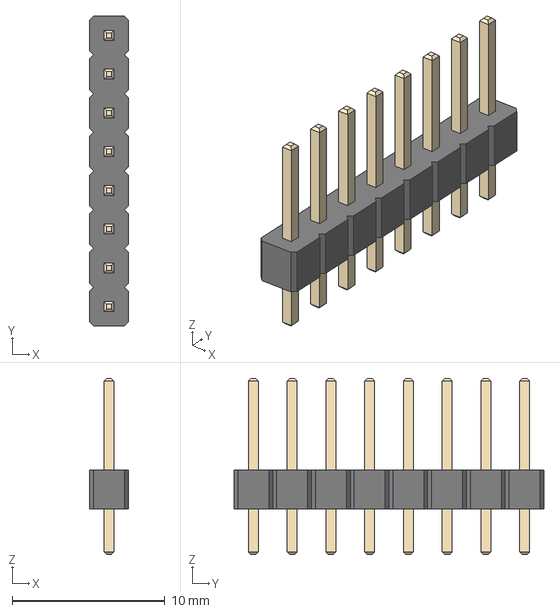
[picture p160: CAD file, 2024-03-11]
eda/g0dzilla_vs/3d_models/PinHeader_1x08_P2.54mm_Vertical.step
2.54 x 20.3 x 11.5 mm
