gowenrw/g0dzilla_vs/eda/g0dzilla_vs/3d_models/RJ45_Amphenol_RJHSE538X.step

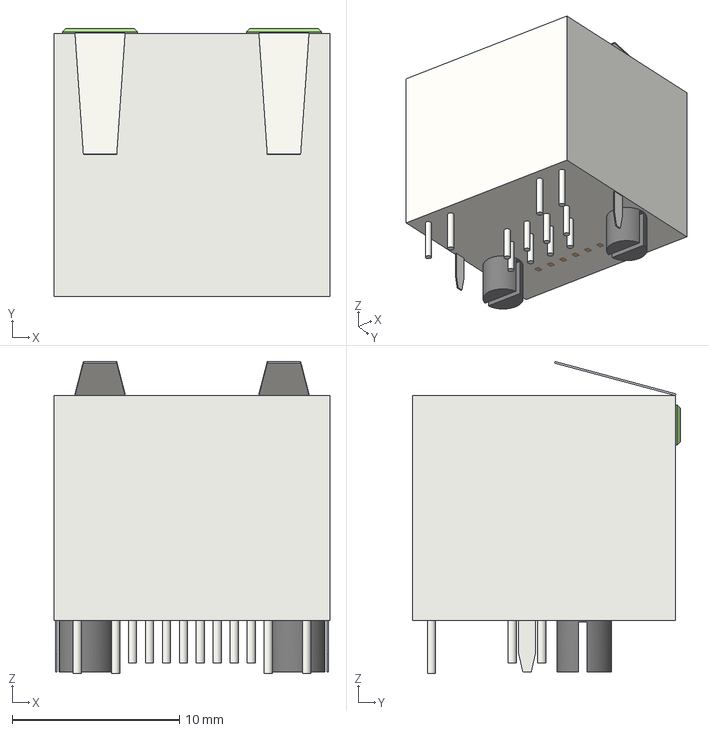
[picture p161: CAD file, 2024-03-11]
eda/g0dzilla_vs/3d_models/RJ45_Amphenol_RJHSE538X.step
16.5 x 16.1 x 18.7 mm
