gowenrw/g0dzilla_vs/eda/g0dzilla_vs/3d_models/CP_Radial_D6.3mm_P2.50mm.step

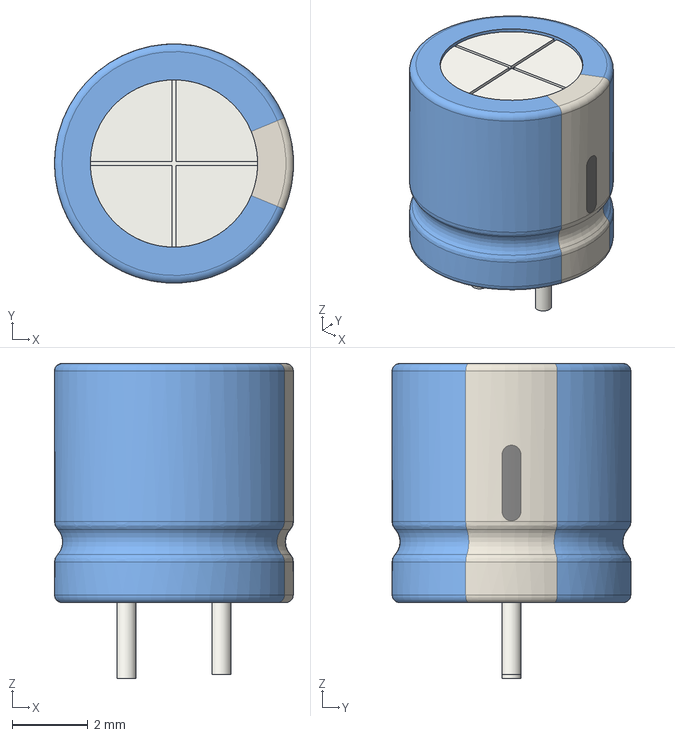
[picture p166: CAD file, 2024-03-11]
eda/g0dzilla_vs/3d_models/CP_Radial_D6.3mm_P2.50mm.step
6.30 x 6.30 x 8.30 mm
