gowenrw/g0dzilla_vs/eda/g0dzilla_vs/3d_models/SOIC-16_3.9x9.9mm_P1.27mm.step

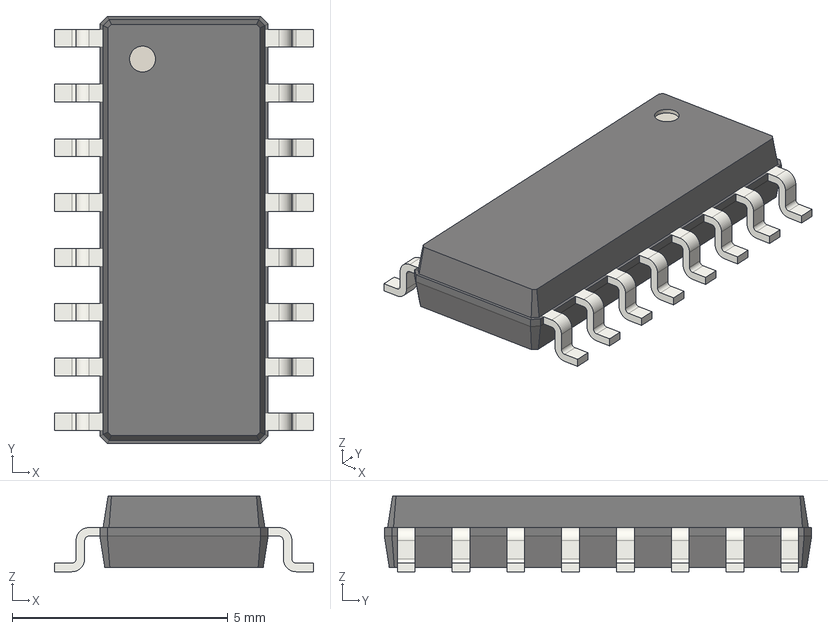
[picture p167: CAD file, 2024-03-11]
eda/g0dzilla_vs/3d_models/SOIC-16_3.9x9.9mm_P1.27mm.step
6.00 x 9.90 x 1.75 mm
