gowenrw/g0dzilla_vs/eda/g0dzilla_vs/3d_models/SW_PUSH_6mm.step

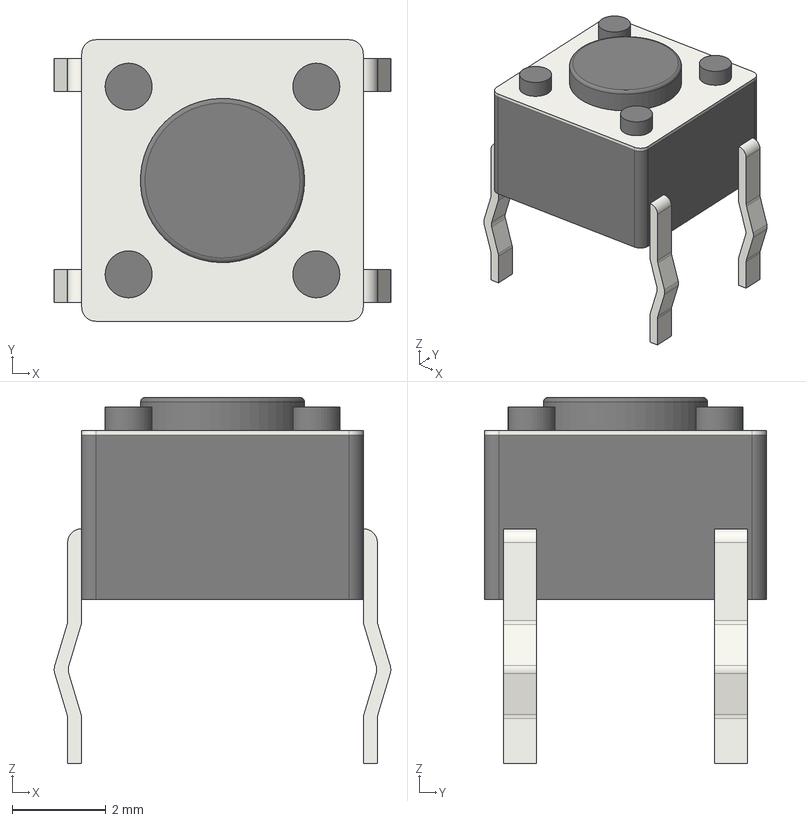
[picture p168: CAD file, 2024-03-11]
eda/g0dzilla_vs/3d_models/SW_PUSH_6mm.step
7.17 x 6.00 x 7.80 mm
