gowenrw/g0dzilla_vs/eda/g0dzilla_vs/3d_models/LED_D3.0mm.step

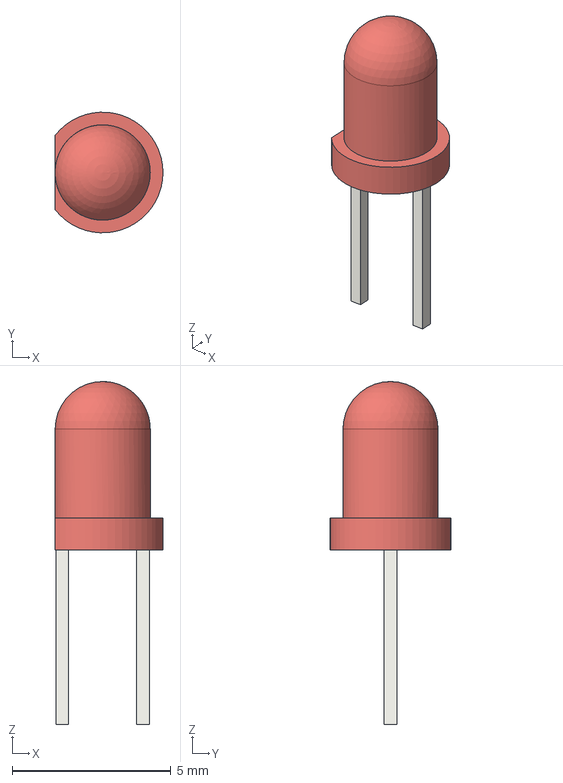
[picture p171: CAD file, 2024-03-11]
eda/g0dzilla_vs/3d_models/LED_D3.0mm.step
3.40 x 3.80 x 10.8 mm
