gowenrw/g0dzilla_vs/eda/g0dzilla_vs/3d_models/USB_Micro-B_Molex_47346-0001.step

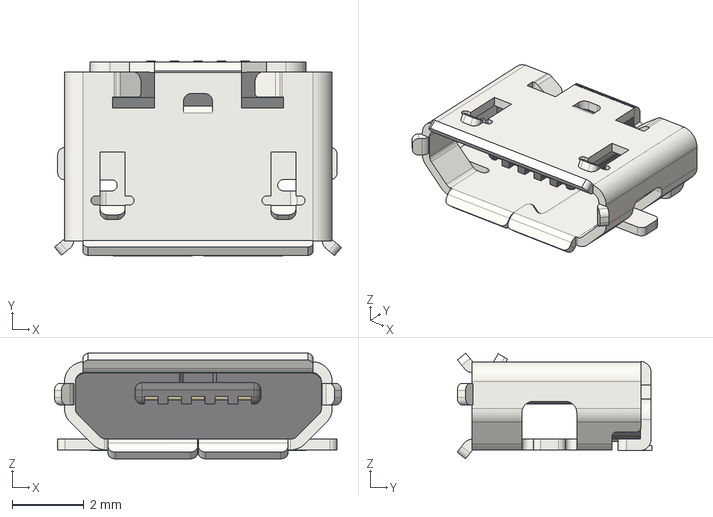
[picture p172: CAD file, 2024-03-11]
eda/g0dzilla_vs/3d_models/USB_Micro-B_Molex_47346-0001.step
7.98 x 5.42 x 2.94 mm
