gowenrw/g0dzilla_vs/eda/g0dzilla_vs/3d_models/TS2306A.step

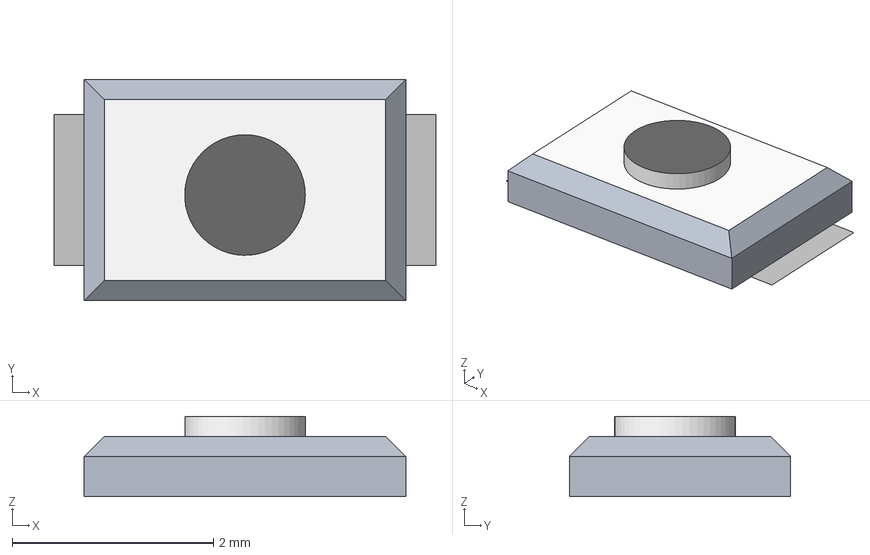
[picture p175: CAD file, 2024-03-11]
eda/g0dzilla_vs/3d_models/TS2306A.step
3.80 x 2.20 x 0.8 mm
Plane
