gowenrw/g0dzilla_vs/eda/g0dzilla_vs/3d_models/PinHeader_1x20_P2.54mm_Horizontal.step

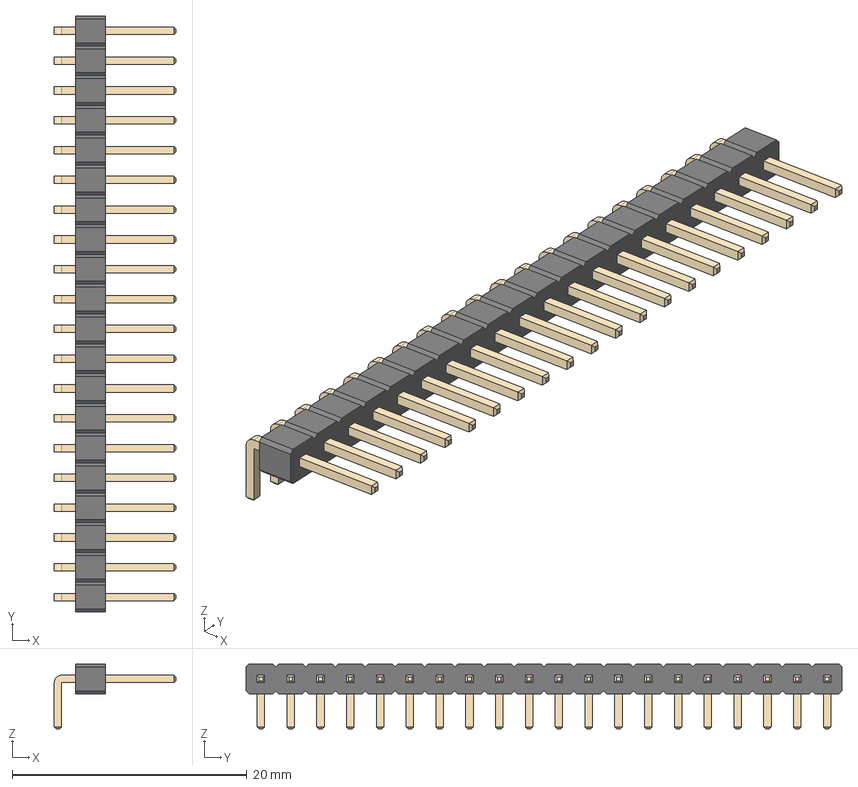
[picture p176: CAD file, 2024-03-11]
eda/g0dzilla_vs/3d_models/PinHeader_1x20_P2.54mm_Horizontal.step
10.4 x 50.8 x 5.54 mm
