gowenrw/g0dzilla_vs/eda/g0dzilla_vs/3d_models/C_0805_2012Metric.step

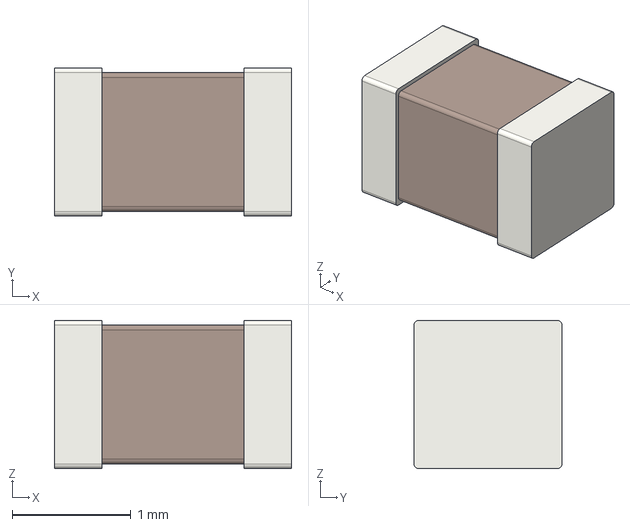
[picture p178: CAD file, 2024-03-11]
eda/g0dzilla_vs/3d_models/C_0805_2012Metric.step
2.00 x 1.25 x 1.25 mm
