gowenrw/g0dzilla_vs/eda/g0dzilla_vs/3d_models/PinSocket_1x15_P2.54mm_Vertical.step

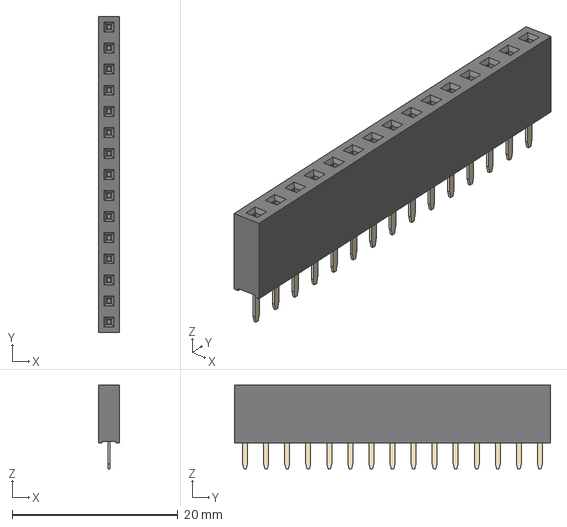
[picture p180: CAD file, 2024-03-11]
eda/g0dzilla_vs/3d_models/PinSocket_1x15_P2.54mm_Vertical.step
2.54 x 38.1 x 10.1 mm
