gowenrw/g0dzilla_vs/eda/g0dzilla_vs/3d_models/BatteryHolder_2468_2xAAA.step

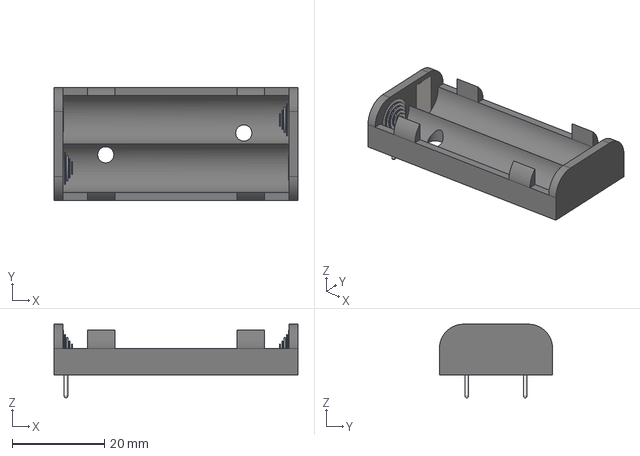
[picture p182: CAD file, 2024-03-11]
eda/g0dzilla_vs/3d_models/BatteryHolder_2468_2xAAA.step
53.0 x 24.6 x 16.0 mm
