gowenrw/g0dzilla_vs/eda/g0dzilla_vs/3d_models/GC9A01_1.28IN_240x240_v1.step

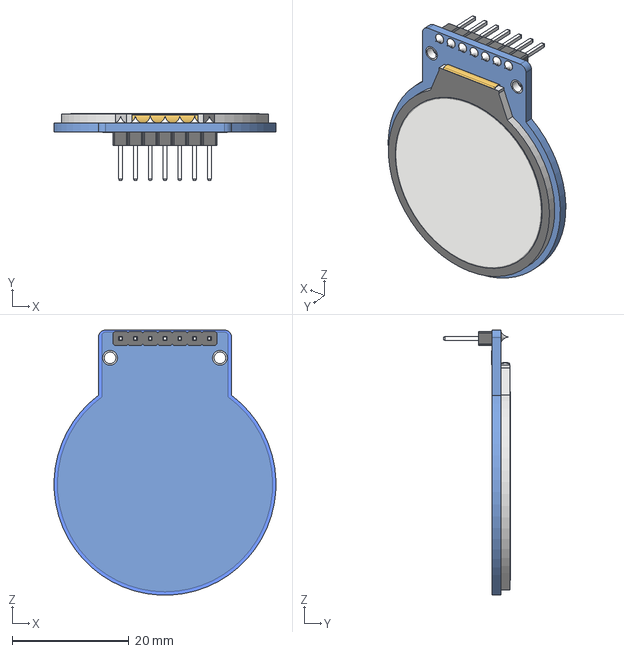
[picture p184: CAD file, 2024-03-11]
eda/g0dzilla_vs/3d_models/GC9A01_1.28IN_240x240_v1.step
38.1 x 11.5 x 45.5 mm
