gowenrw/g0dzilla_vs/eda/g0dzilla_vs/3d_models/R_0805_2012Metric.step

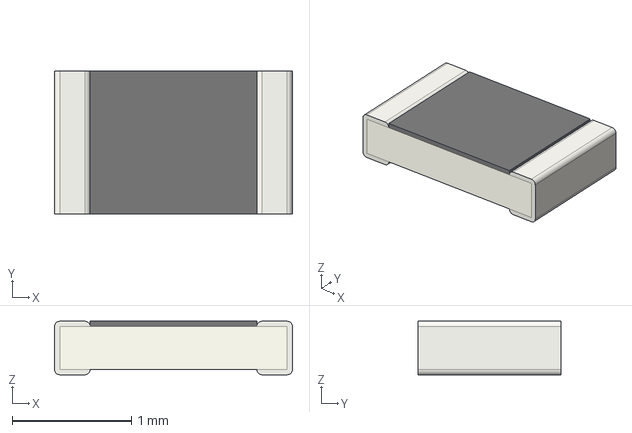
[picture p189: CAD file, 2024-03-11]
eda/g0dzilla_vs/3d_models/R_0805_2012Metric.step
2.00 x 1.20 x 0.45 mm
