gowenrw/g0dzilla_vs/eda/g0dzilla_vs/3d_models/LED_D3.0mm-3.step

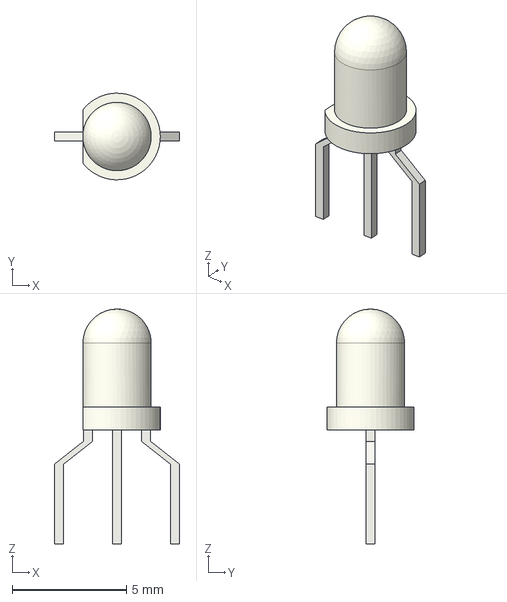
[picture p190: CAD file, 2024-03-11]
eda/g0dzilla_vs/3d_models/LED_D3.0mm-3.step
5.48 x 3.80 x 10.3 mm
