gowenrw/g0dzilla_vs/eda/g0dzilla_vs/3d_models/PinSocket_1x02_P2.54mm_Vertical.step

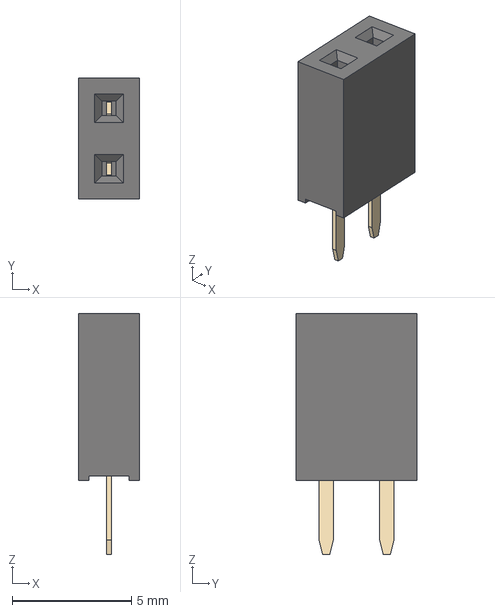
[picture p193: CAD file, 2024-03-11]
eda/g0dzilla_vs/3d_models/PinSocket_1x02_P2.54mm_Vertical.step
2.54 x 5.08 x 10.1 mm
