gowenrw/g0dzilla_vs/eda/g0dzilla_vs/3d_models/Battery_Holder_3xAAA_Simple.step

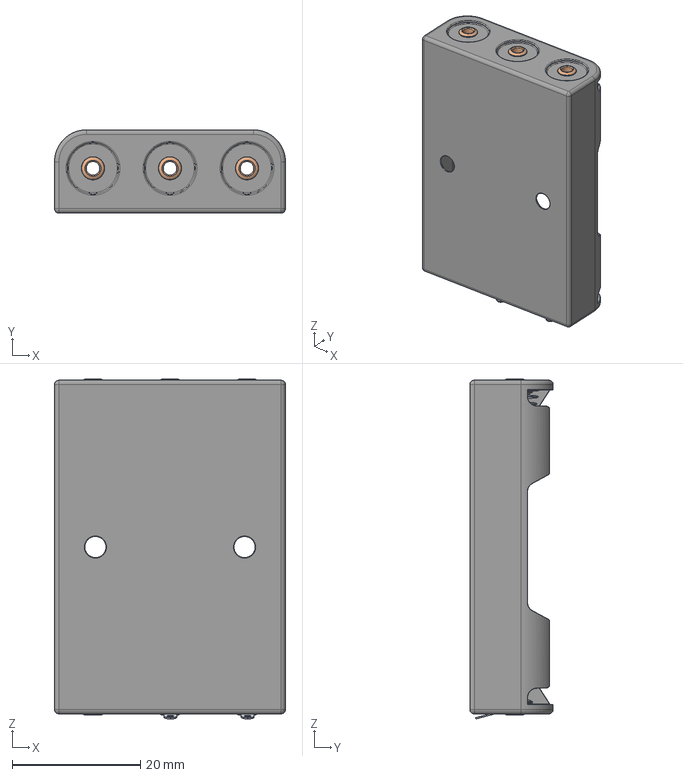
[picture p194: CAD file, 2024-03-11]
eda/g0dzilla_vs/3d_models/Battery_Holder_3xAAA_Simple.step
36.0 x 13.0 x 53.0 mm
