gowenrw/g0dzilla_vs/eda/g0dzilla_vs/3d_models/TO-92_Inline.step

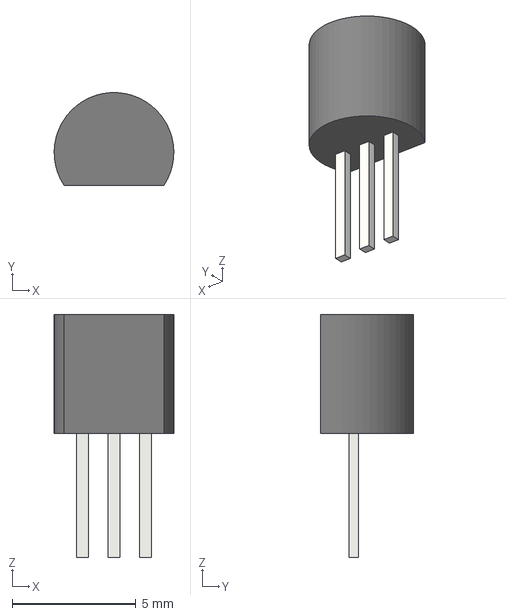
[picture p197: CAD file, 2024-03-11]
eda/g0dzilla_vs/3d_models/TO-92_Inline.step
4.83 x 3.74 x 9.80 mm
