gowenrw/g0dzilla_vs/eda/g0dzilla_vs/3d_models/PinSocket_1x01_P2.54mm_Horizontal.step

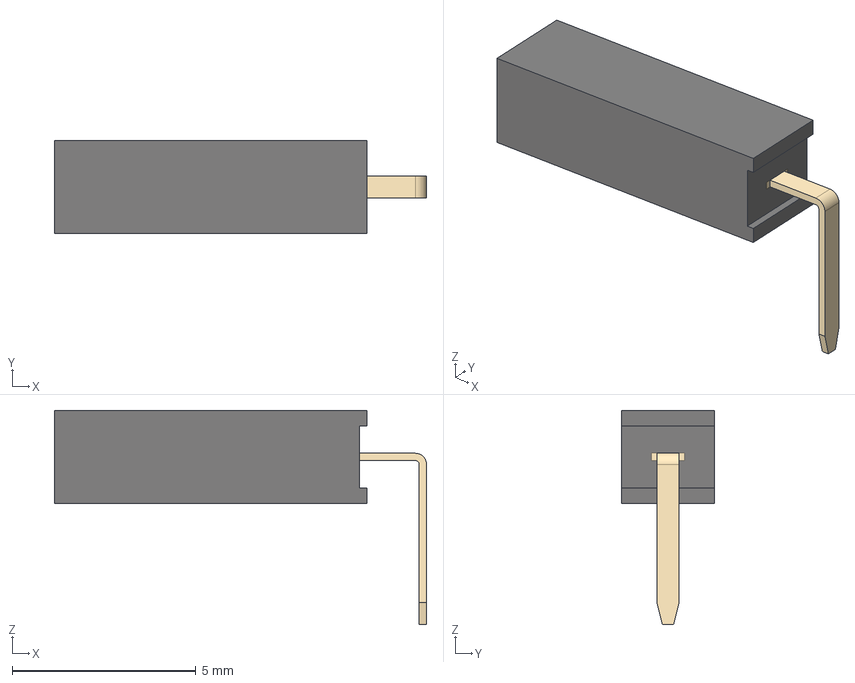
[picture p201: CAD file, 2024-03-11]
eda/g0dzilla_vs/3d_models/PinSocket_1x01_P2.54mm_Horizontal.step
10.1 x 2.54 x 5.84 mm
