gowenrw/g0dzilla_vs/eda/g0dzilla_vs/3d_models/PinSocket_1x03_P2.54mm_Vertical.step

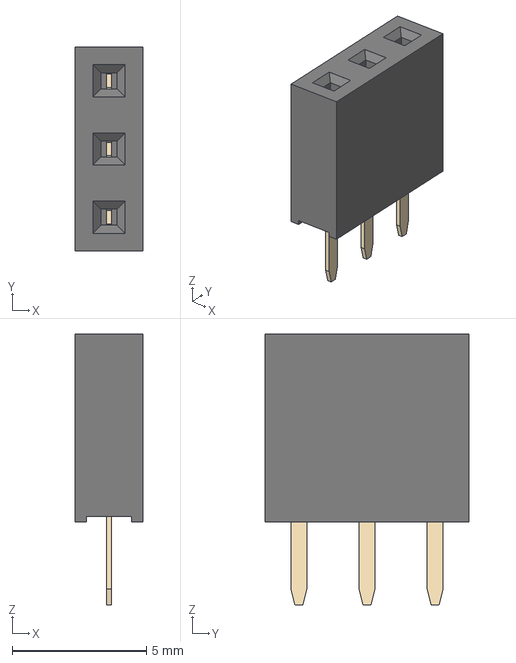
[picture p202: CAD file, 2024-03-11]
eda/g0dzilla_vs/3d_models/PinSocket_1x03_P2.54mm_Vertical.step
2.54 x 7.62 x 10.1 mm
