gowenrw/g0dzilla_vs/eda/g0dzilla_vs/3d_models/PinHeader_1x04_P2.54mm_Horizontal.step

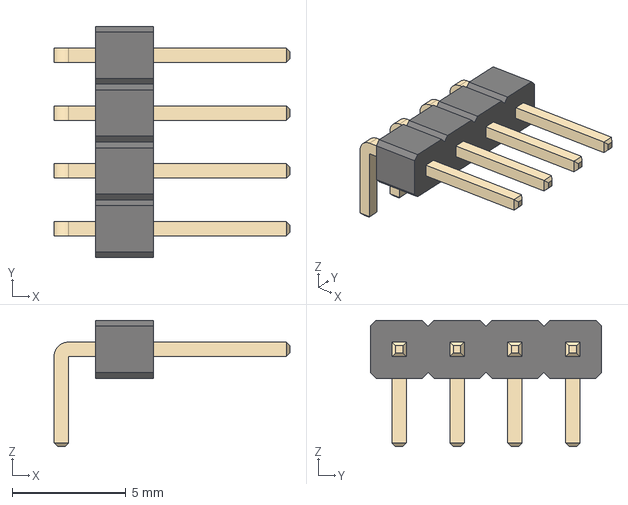
[picture p204: CAD file, 2024-03-11]
eda/g0dzilla_vs/3d_models/PinHeader_1x04_P2.54mm_Horizontal.step
10.4 x 10.2 x 5.54 mm
