gowenrw/g0dzilla_vs/eda/g0dzilla_vs/3d_models/LED_D5.0mm.step

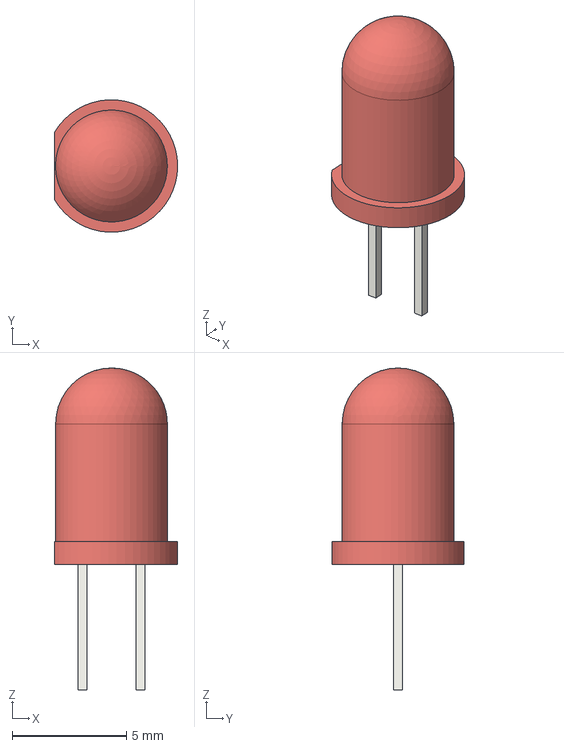
[picture p207: CAD file, 2024-03-11]
eda/g0dzilla_vs/3d_models/LED_D5.0mm.step
5.40 x 5.79 x 14.1 mm
