gowenrw/g0dzilla_vs/eda/g0dzilla_vs/3d_models/C_0603_1608Metric.step

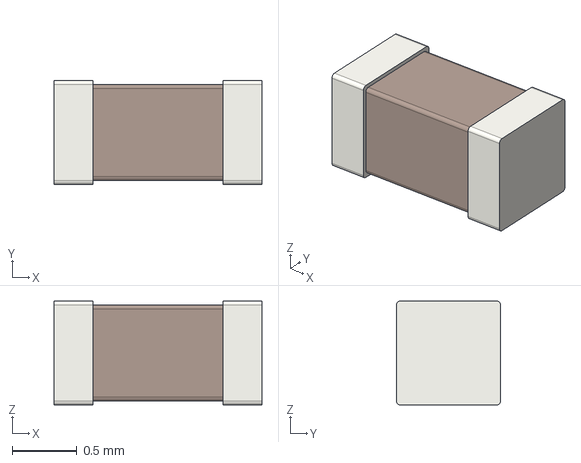
[picture p208: CAD file, 2024-03-11]
eda/g0dzilla_vs/3d_models/C_0603_1608Metric.step
1.60 x 0.8 x 0.8 mm
