gowenrw/g0dzilla_vs/eda/g0dzilla_vs/3d_models/SW_SPDT_PCM12.step

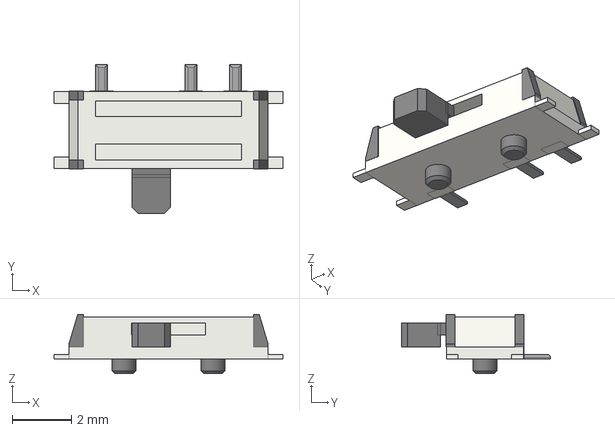
[picture p214: CAD file, 2024-03-11]
eda/g0dzilla_vs/3d_models/SW_SPDT_PCM12.step
7.70 x 5.00 x 2.00 mm
