gowenrw/g0dzilla_vs/eda/g0dzilla_vs/3d_models/SOT-23.step

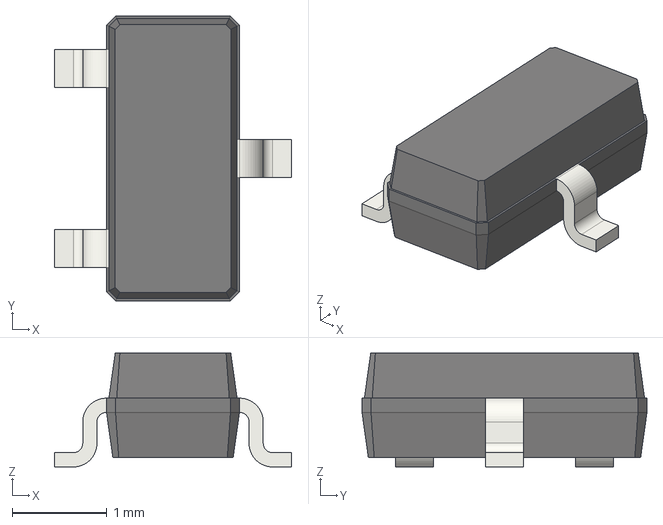
[picture p218: CAD file, 2024-03-11]
eda/g0dzilla_vs/3d_models/SOT-23.step
2.50 x 3.00 x 1.20 mm
