gowenrw/g0dzilla_vs/eda/g0dzilla_vs/3d_models/C_Disc_D3.0mm_W2.0mm_P2.50mm.step

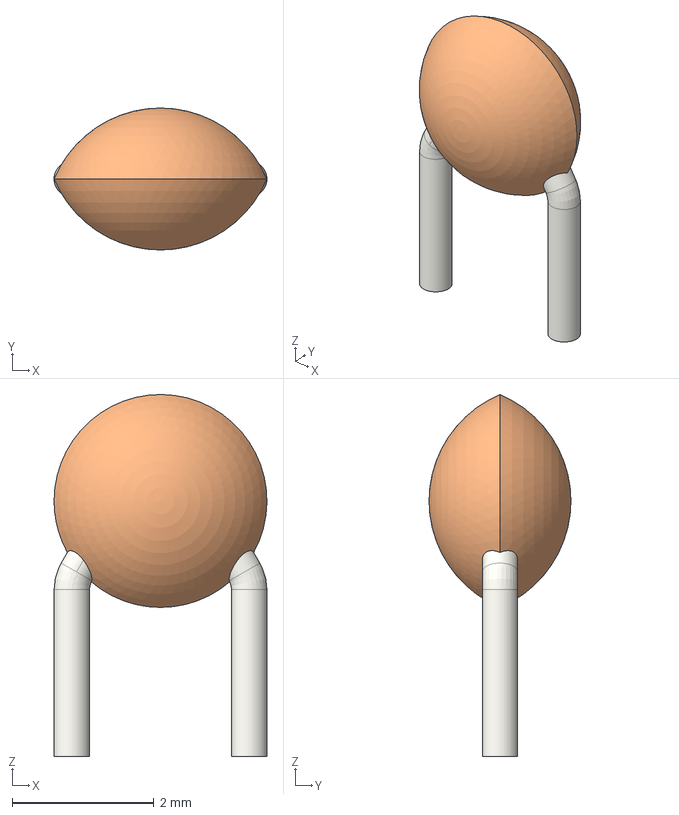
[picture p220: CAD file, 2024-03-11]
eda/g0dzilla_vs/3d_models/C_Disc_D3.0mm_W2.0mm_P2.50mm.step
3.00 x 2.00 x 5.10 mm
