gowenrw/g0dzilla_vs/eda/g0dzilla_vs/3d_models/PinHeader_1x05_P2.54mm_Horizontal.step

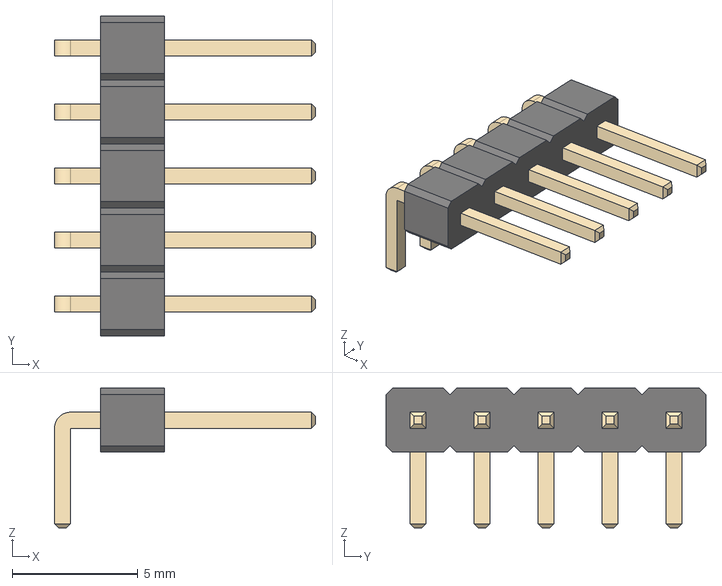
[picture p221: CAD file, 2024-03-11]
eda/g0dzilla_vs/3d_models/PinHeader_1x05_P2.54mm_Horizontal.step
10.4 x 12.7 x 5.54 mm
