gowenrw/g0dzilla_vs/eda/g0dzilla_vs/3d_models/PinHeader_1x08_P2.54mm_Horizontal.step

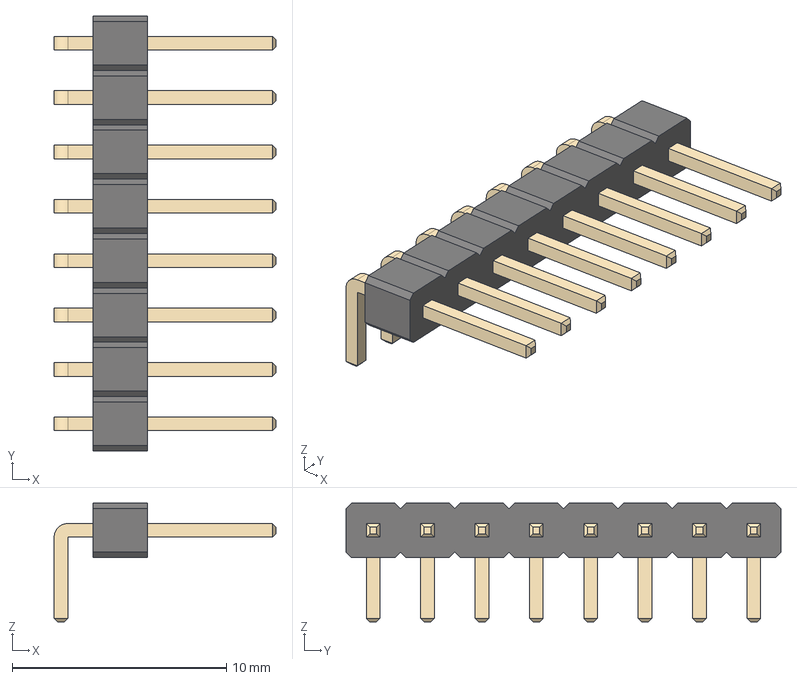
[picture p225: CAD file, 2024-03-11]
eda/g0dzilla_vs/3d_models/PinHeader_1x08_P2.54mm_Horizontal.step
10.4 x 20.3 x 5.54 mm
