gowenrw/g0dzilla_vs/eda/g0dzilla_vs/3d_models/CUI_PXO7803-500-M-TR.step

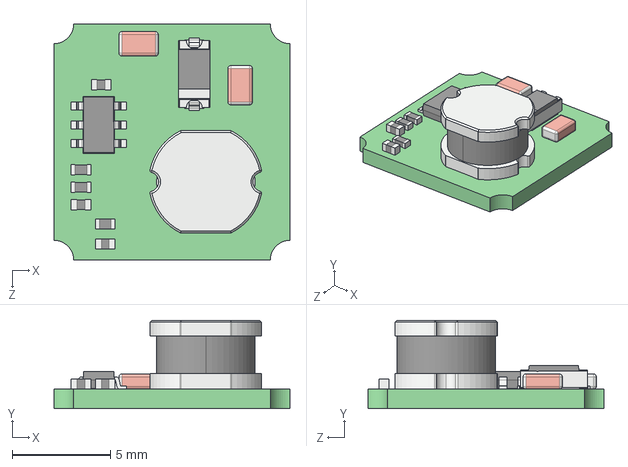
[picture p226: CAD file, 2024-03-11]
eda/g0dzilla_vs/3d_models/CUI_PXO7803-500-M-TR.step
12.0 x 4.50 x 12.0 mm
