gowenrw/g0dzilla_vs/eda/g0dzilla_vs/3d_models/R_1206_3216Metric.step

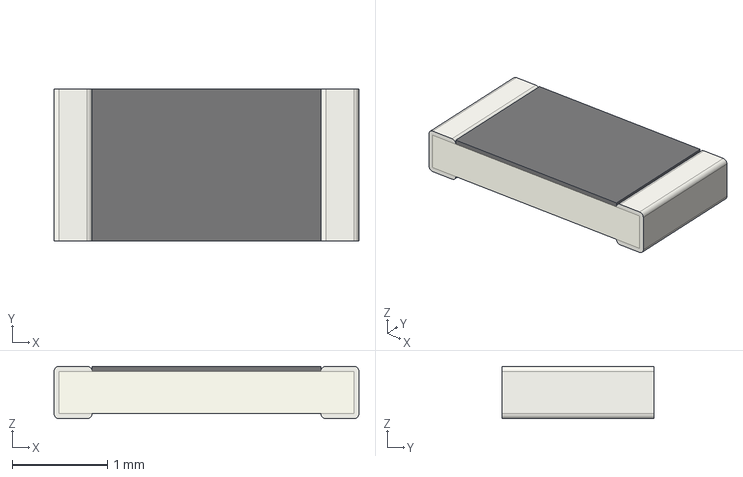
[picture p227: CAD file, 2024-03-11]
eda/g0dzilla_vs/3d_models/R_1206_3216Metric.step
3.20 x 1.60 x 0.55 mm
