gowenrw/g0dzilla_vs/art/inspiration/alt_bier_Godzilla_with_tail_raised_attacking_a_building_behind__874b4e45-1951-4f99-a692-f28d2c677aa9.png

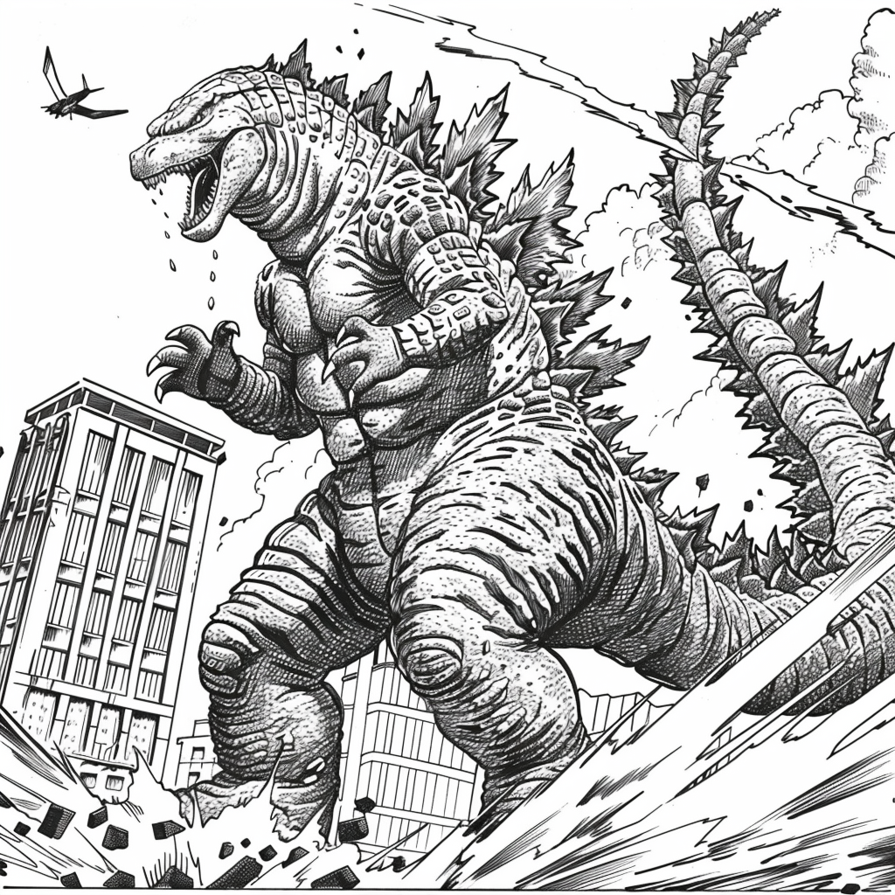
art/inspiration/alt_bier_Godzilla_with_tail_raised_attacking_a_building_behind__874b4e45-1951-4f99-a692-f28d2c677aa9.png
