gowenrw/g0dzilla_vs/art/inspiration/alt_bier_hand_holding_a_smoking_soldering_iron_simple_lineart_i_eb786b9e-26d6-4ee0-b8a0-1cdc269863c5.png

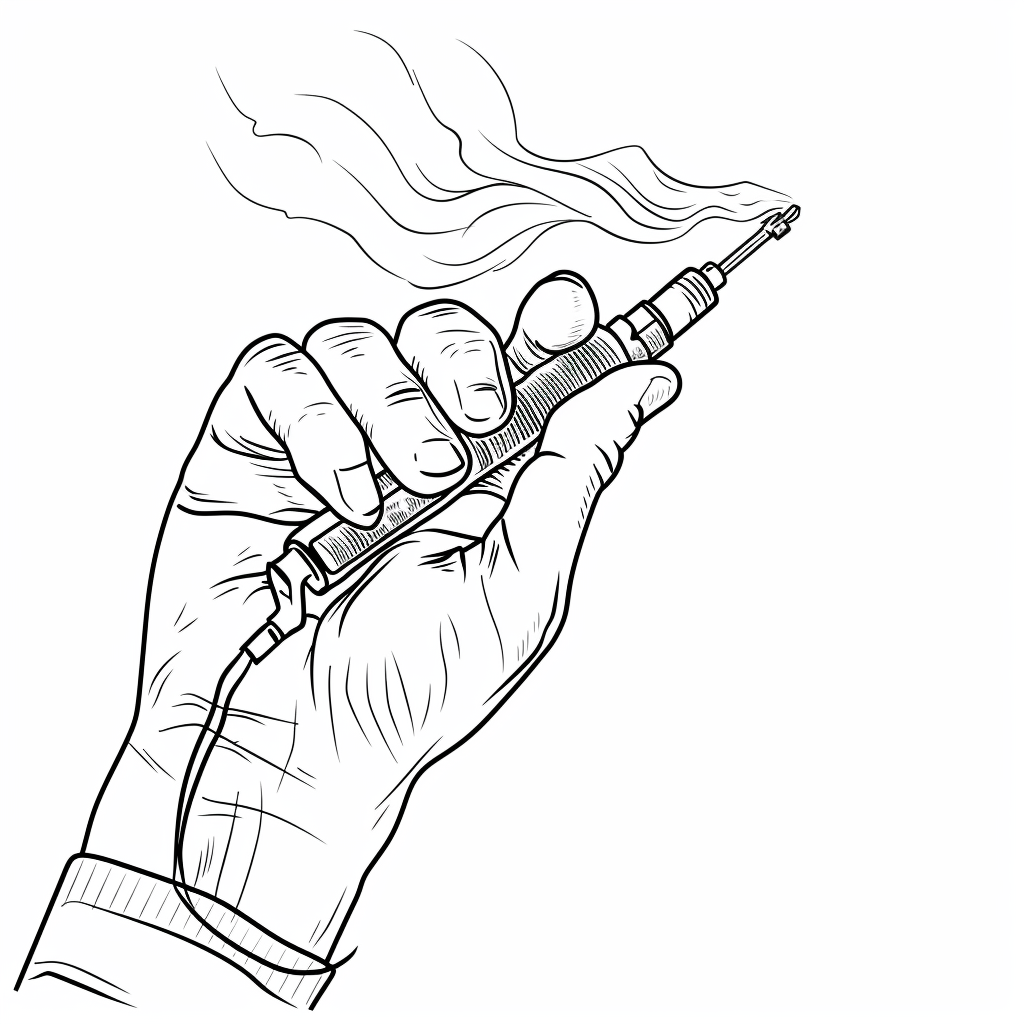
art/inspiration/alt_bier_hand_holding_a_smoking_soldering_iron_simple_lineart_i_eb786b9e-26d6-4ee0-b8a0-1cdc269863c5.png
