gowenrw/g0dzilla_vs/docs/images/AssemblyPic22.jpg

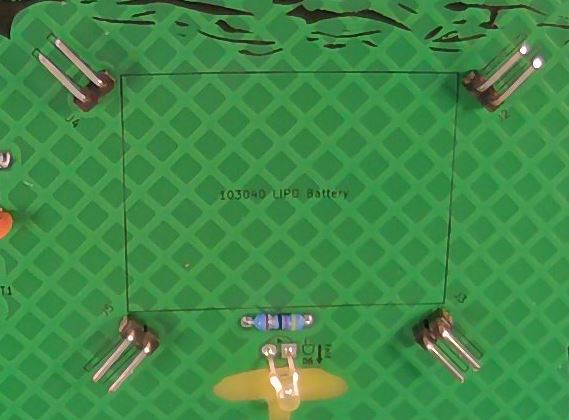
docs/images/AssemblyPic22.jpg
