gowenrw/g0dzilla_vs/docs/images/AssemblyPic24.jpg

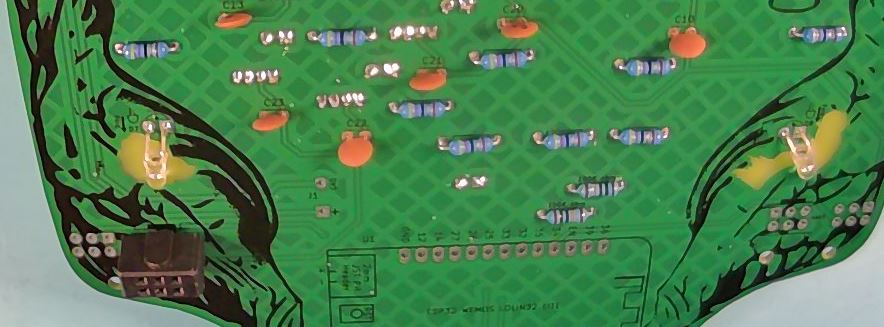
docs/images/AssemblyPic24.jpg
