gowenrw/g0dzilla_vs/docs/images/AssemblyPic25.jpg

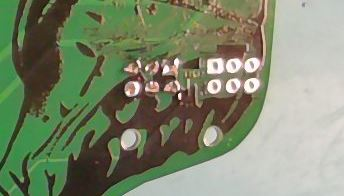
docs/images/AssemblyPic25.jpg
