gowenrw/g0dzilla_vs/docs/images/AssemblyPic26.jpg

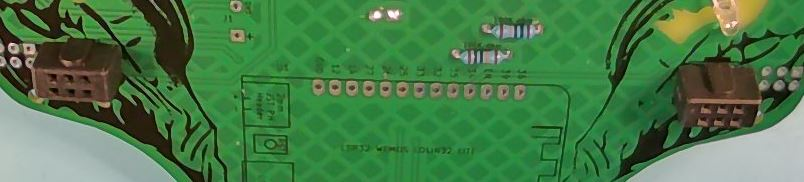
docs/images/AssemblyPic26.jpg
