gowenrw/g0dzilla_vs/docs/images/AssemblyPic27.jpg

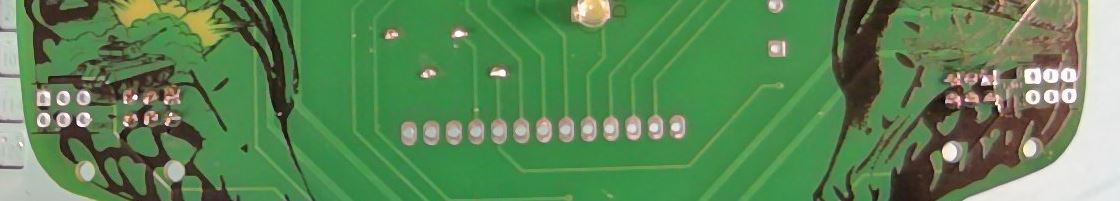
docs/images/AssemblyPic27.jpg
