gowenrw/g0dzilla_vs/docs/images/AssemblyPic28.jpg

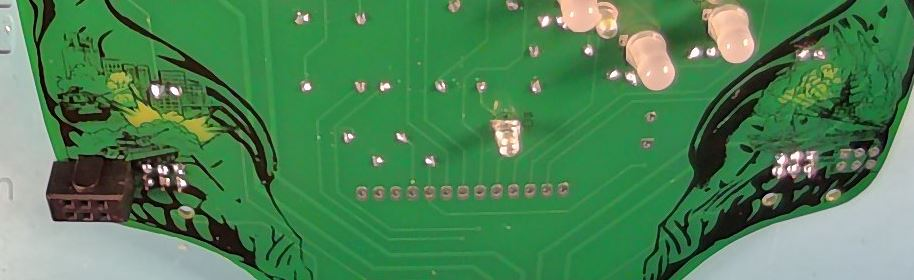
docs/images/AssemblyPic28.jpg
