gowenrw/g0dzilla_vs/docs/images/AssemblyPic29.jpg

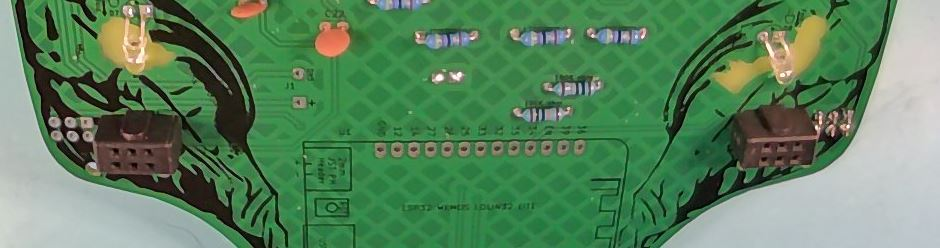
docs/images/AssemblyPic29.jpg
