gowenrw/g0dzilla_vs/docs/images/AssemblyPic30.jpg

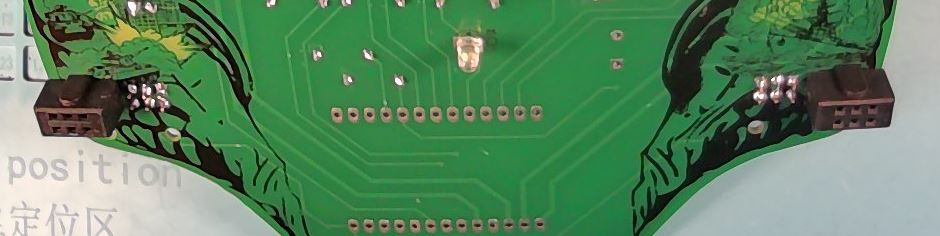
docs/images/AssemblyPic30.jpg
