gowenrw/g0dzilla_vs/docs/images/AssemblyPic31.jpg

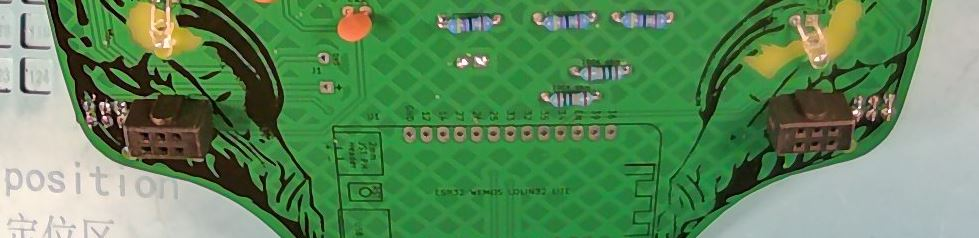
docs/images/AssemblyPic31.jpg
