gowenrw/g0dzilla_vs/docs/images/AssemblyPic33.jpg

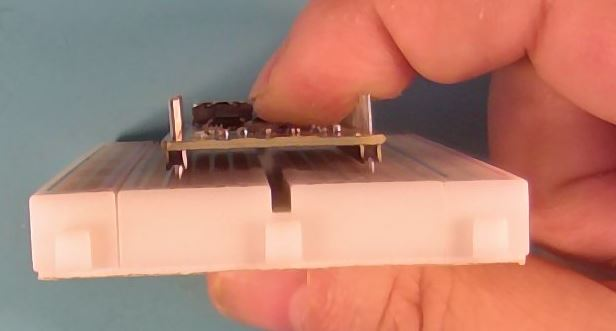
docs/images/AssemblyPic33.jpg
