gowenrw/g0dzilla_vs/docs/images/AssemblyPic37.jpg

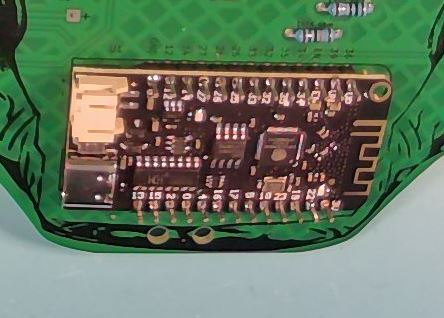
docs/images/AssemblyPic37.jpg
