gowenrw/g0dzilla_vs/docs/images/AssemblyPic38.jpg

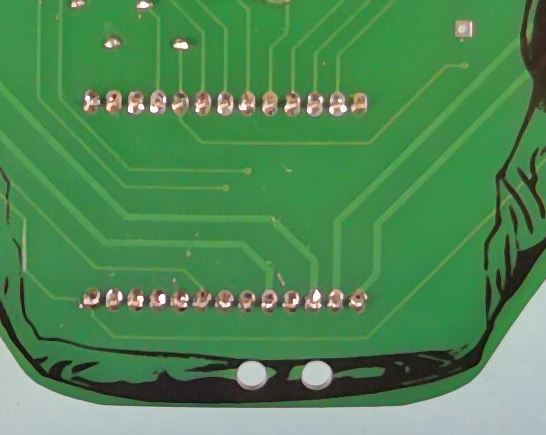
docs/images/AssemblyPic38.jpg
