gowenrw/g0dzilla_vs/docs/images/AssemblyPic52.jpg

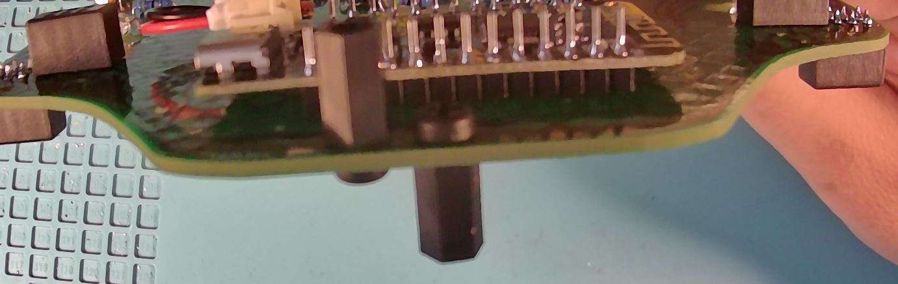
docs/images/AssemblyPic52.jpg
